Papipapito/MSXimus_138/docs/historico/informes_v2/INFORME_NIQUELADO.md

# Informe final — Investigación "niquelado" del repo MSXimus (v2.0)

**Contexto**: v2.0 recién publicada (V9968 + VRAM DDR3 con refresh arreglado + WiFi C6). Va a venir gente a mirar el repo, sobre todo el `opl4wave`, que quieren copiar. Cinco frentes auditados: opl4wave (bugs), audio OPL4-FM/mixer, shim DDR3, parches V9968, top/relojes, SD/USB/flash, y una pasada de presentabilidad ("opl4wave-bonito"). Todos los hallazgos aquí listados pasaron una fase de verificación adversaria (intento de refutación contra el RTL real); veredictos: **CONFIRMADO** = reproducción lógica cerrada en el código, **PLAUSIBLE** = mecanismo real verificado pero disparador no demostrado.

Rutas relativas a `C:\Users\alber\proyectosAI\msx\MSX_up\`.

---

## 1. Bugs verificados (ranked por severidad)

### Severidad ALTA

| # | Fichero:línea | Veredicto | Bug (una frase) | Esbozo de arreglo |
|---|---|---|---|---|
| 1 | `fpga/v9968/vdp_cpu_interface.v:309` | CONFIRMADO | El latch del bus acepta con `ff_bus_ready` CRUDO mientras el glue espera el `bus_ready` gateado (`:332`), así que una transacción I/O que caiga en el último ciclo de una ventana busy/inflight se ejecuta DOS veces — mecanismo cerrado ciclo a ciclo que explica el residuo histórico del "salto +1 del puerto CPU" (~0,1-0,3%), distinto del router +1 arreglado en _157. | Gatear el latch con las mismas condiciones que el output: `bus_valid && ff_bus_ready && !ff_busy && !ff_pf_inflight`; verificar con tb_t2cpuread + tráfico I/O a 5.37 MHz con latencias forzadas >2 µs. |
| 2 | `fpga/v9968/vdp_command_cache.v:177` | CONFIRMADO | Si un start de comando (escritura de R#46, legal sin esperar CE=0) llega durante un flush ya drenado (típico: comandos de solo lectura como POINT/SRCH/LMCM), `ff_busy` se pone a 1 y ningún camino lo limpia jamás: el comando nuevo nunca se ejecuta, CE cae igualmente y el software ve un rectángulo/copia fantasma; solo recupera la siguiente escritura de R#46. | En la rama start con flush en curso: `ff_busy <= w_dirty_any \| ff_vram_valid;` — o añadir en el estado 3'd1 del flush `if (!ff_vram_valid) ff_busy <= 1'b0;` para que TODO cierre de flush libere busy. |
| 3 | `fpga/src/v9968_vram_shim.v:28` | CONFIRMADO | En el build de respaldo _137 (VRAM del V9968 en la SDRAM compartida) la VRAM en 0x280000 cae DENTRO de la RAM de muestras del OPL4 (0x200000-0x3FFFFF, entera escribible según `opl4_pcm.v:575`): samples >512KB o la detección de RAM de MoonBlaster Wave machacan la VRAM en vivo, y viceversa. Desarmado en la v2.0 (VRAM en DDR3), pero armado en la línea de respaldo documentada. | Mover la familia wv2/wv3 a su propio bloque de filas (`{1'b1,2'b01,addr[21:12]}` en `memory.v`, filas 5120+ libres) o recortar la RAM visible del motor a 512KB (guard `e_addr22[21:19]==3'b100`); como mínimo, documentar el solape en la línea _137. |

### Severidad MEDIA — CONFIRMADOS

| # | Fichero:línea | Veredicto | Bug (una frase) | Esbozo de arreglo |
|---|---|---|---|---|
| 4 | `fpga/top.v:3509` | CONFIRMADO | El tono de test 440 Hz del bug #14 (_127H) sigue armado en release: activar el toggle "Sprite Limit" del menú (config2[3], que ADEMÁS sigue conectado a `maxspr_n` en la build commiteada) sustituye TODO el audio por una cuadrada a -12 dB, y el estado persiste en flash si se guarda la config. | Envolver la rama del tono en `` `ifdef DEBUG_TONE `` (o retirarla) y devolver config2[3] a su función única; si se conserva, moverlo a un bit SWIO no expuesto en el menú. |
| 5 | `fpga/src/opl4_pcm.v:726` | CONFIRMADO | `.IC_N(erst_n)` empatado con `.RST_N(erst_n)` deja muerta la rama de reset de chip del motor: MIXFM arranca en 0x00 en vez del canon 0x1B, así que VGMPlay/OPL3 (que nunca escribe F8) suena con el FM ~2,7× (+8,5 dB) más fuerte que un MoonSound real. | Retrasar IC_N unos ciclos respecto a RST_N en opl4_pcm (contador que suelte IC_N N ciclos después) para que la rama RES_N ejecute tras cada reset; o parchear la rama RST_N del motor con los valores canon (marcado `MSXimus:`). |
| 6 | `fpga/src/opl4_pcm.v:277` | CONFIRMADO | El acumulador de CE (24 bits, sin clamp) se envuelve a los ~32 µs de stall continuo; con los stalls reales de los watchdogs (~0,9 ms wave_ddr3, ~3,5 ms ifw) pierde ~39-153 muestras de crédito y, como productor y consumidor del FIFO _98 usan la fracción exacta 14112/15625, el colchón (armado a 8) cae a 0-1 PARA SIEMPRE: crujidos permanentes tras un único evento de watchdog, hasta reset. | Saturar el acumulador (`if (ce_acc < CE_MAX) ce_acc <= ce_acc + CE_INC`, tope 2-3 muestras) y/o re-armar el colchón del FIFO a 8 cuando `ifw_hits`/`wd_ops` incrementen. |
| 7 | `fpga/src/opl4_pcm.v:124` | CONFIRMADO | El latch host→motor de escrituras OPL4 es de 1 plaza con toggle y sin /WAIT: dos escrituras sin consumo intermedio se ANULAN por paridad (ambas desaparecen), alcanzable cuando el CE del motor se congela más de ~2,2 µs (escenario watchdog ~3,5 ms, con precedente en HW) — instrumento/nota/KEY-ON perdidos. | Mini-FIFO host→motor de 4-8 plazas, o contador Gray de 2 bits (las peticiones dejan de anularse por paridad), y/o extender `wave_wait_n` a las escrituras con la plaza ocupada. |
| 8 | `fpga/top.v:3021` | CONFIRMADO | Con el motor sonando, las escrituras por el puerto debug 34-37h van al puerto HOST de wave_sdram puenteando la caché por-slot de opl4_pcm (cuyo único flush es el wr_edge del propio motor): una palabra ya cacheada se sirve rancia indefinidamente, y para región ROM (parches de la YRW801) no existe NINGUNA vía de invalidación salvo miss o reset. | Cruzar un toggle `host_wrote` de top.v al dominio clk_eng que ejecute el flush total (lb_v/lb_pfb<=0, vaciar pfq), o bloquear las escrituras 34-37h mientras `wl_done==1`. |
| 9 | `fpga/src/opl4_pcm.v:179` | CONFIRMADO | `mix_fm` no está en la rama de reset y solo se refresca cuando el motor emite muestra; como todo reset relanza la copia+verify de 2 MB de la YRW801 (~5 s con el motor parado), si el software anterior dejó F8≠0 (F8=7 = MUTE) el FM del OPL4 arranca atenuado o mudo durante segundos tras cada reset caliente. | Añadir `mix_fm <= 6'd0;` a la rama `!rst_n` (0 dB, igual que el stub sin motor); y muestrear `eng_mixfm` junto al toggle `pcm_t_x` en el lado eng para el cruce de dominio (mismo protocolo que pcm_l_x/pcm_r_x). |
| 10 | `fpga/top.v:3485` | CONFIRMADO | Los dos PSG entran al mixer como unsigned 0..255<<6 (término siempre ≥0, hasta +32640 en mono) frente al resto bipolar: el headroom positivo del sat16 se agota casi solo con los PSG y el mixer recorta sistemáticamente solo el semiciclo positivo (distorsión asimétrica "sucia" al cargar la mezcla). | Centrar el PSG antes de mezclar (DC-blocker de 1 polo: `y = x − lpf(x)`, un acumulador de 24 bits) o restar un offset fijo equivalente al nivel medio; alternativa barata: entrar con `<<5`. |
| 11 | `fpga/top.v:784` | CONFIRMADO | El O_DA del PSG principal está sin conectar y IN 0xA2 devuelve 0xFF para todo registro salvo R14: el patrón canónico RDPSG(R7)→AND/OR→WRTPSG escribe basura en los enables de mezcla (canales deshabilitados), mientras el segundo PSG sí tiene readback real. | Conectar `O_DA` del psg1 y servirlo en IN 0xA2 para `psg_addr_latch != 14` (conservando la inyección de joystick USB en R14), igual que ya se hace con `psg2_dout`. |
| 12 | `fpga/src/v9968_vram_shim.v:1320` | CONFIRMADO | El camino de la VENTANA de prefetch (pww) hereda la carrera fill↔escritura que el _150 solo curó en la sc-cache (sin `wr_accept` en el commit ni matador de pendientes, y `pw_v` es set-only tras _140): una escritura del VDP coincidiendo con la completación del fill deja la ventana válida con el dato PRE-escritura, servido en hit ~1 frame parcial. | Replicar la cura _150 en pww: abortar el commit de `pww_*`/`pwv_set` si en el ciclo de completación hay `wr_accept` o `wrk_p1` con `wrk_addr1==cur_addrw` (comparador FF-FF, mismo coste que la línea 934); el word se autocura por miss. |
| 13 | `fpga/src/v9968_ddr3_backend.v:430` | CONFIRMADO | Todo el servicio de ST_IDLE (hits, emisión Y el rescate FFFF) vive dentro de `if (init_calib_complete)`, y el watchdog se resetea en IDLE con `iss_free`: si la calibración cae en marcha (el caso que `calib_drop` de _95 existe para cazar), una petición pendiente no recibe ni dato ni vacuna — CPU y comandos congelados hasta que el motor de reintentos de ~335 ms/intento (~1/7 de éxito) tenga suerte. | Rama en ST_IDLE: `!init_calib_complete && (a_req&&!a_srv \|\| b_req&&!b_srv) && op_wd[16] → completar FFFF` (dejando que op_wd cuente con petición pendiente sin calibración); motor de reintentos intacto. |
| 14 | `fpga/src/v9968_ddr3_backend.v:522` | CONFIRMADO | En el rescate _95 de ESCRITURA la caché de línea clA/clB ni se actualiza ni se invalida, pero la escritura retenida SÍ aterriza después en la DRAM: los hits de lectura posteriores sirven el dato pre-escritura persistentemente (una línea rancia nunca se autorrepara: leerla es hit) hasta que un miss ajeno la desaloje. | En la rama 522-530 aplicar la misma actualización de clA/clB (op_addr/op_wdata/op_wmask siguen vivos) o, más barato, invalidar (`clA_v/clB_v <= 0`) las líneas cuyo tag case con `op_addr[21:4]`. |
| 15 | `fpga/src/v9968_vram_shim.v:492` | CONFIRMADO | La fusión fill+escritura del _148 FIX B (`pf_one`/`pf_fuse`) es código muerto — cero consumidores en todo fpga/, las tres guardas reales siguen siendo `!pf_dirty` a secas — así que la mejora que la clasificación MISSCLS justificaba (6 de 11 miss de ráfaga) nunca entró en el netlist, y los comentarios de rd_complete describen un comportamiento que el RTL no tiene. | O cablear la fusión como anuncian los comentarios (guardas `!pf_drop`, dato `pf_fuse({w_hi,w_lo})`) y validarla en tb_menu_ddr3/tb_vbcoh, o retirar el bloque 480-510 y corregir los comentarios. |
| 16 | `fpga/v9968/vdp_command_cache.v:697` | CONFIRMADO | Tras abortar un comando con una lectura aceptada pero sin respuesta y caché limpia, la respuesta huérfana (14-90+ ciclos después) resucita una entrada con `ff_update_target` ya reseteado a 0: le cambia la dirección a la de la lectura ABORTADA conservando el byte del comando nuevo → 1 byte de VRAM corrupto en la dirección vieja + píxel perdido + pulso espurio que clobbrea `ff_read_pixel/ff_read_byte`. | Flag `ff_read_discard`: se arma en el start (ambas ramas) si había una lectura aceptada sin respuesta (registrar `ff_read_pending` entre aceptación y rdata_en); la rama 691 consume y descarta la primera respuesta con el flag armado. |
| 17 | `fpga/v9968/vdp_command_cache.v:313` | CONFIRMADO | El start no limpia `ff_cache_vram_rdata_en`: si el R#46 coincide con el pulso (ventana de 1 ciclo) y hay flush sucio, el strobe queda alto todo el flush y al cerrarse la rama :313 gana a la aceptación con ready ya a 1 — el motor cree aceptada su petición y espera un rdata_en que nunca llega (comando colgado con CE=1). | Añadir `ff_cache_vram_rdata_en <= 1'b0;` en AMBAS ramas del start (línea 165): restaura el invariante de 1 ciclo y la carrera del primer ciclo post-flush desaparece. |
| 18 | `fpga/v9968/vdp_timing_control_ssg.v:432` | CONFIRMADO | _120 NO es bit-exacto (ORIGEN.txt refutado): la resta del scroll de sprites usa `reg_horizontal_offset_l` VIVO mientras el original usaba el valor latcheado una vez por par de líneas — un split de R#27 por interrupción llega a los sprites hasta ~2 líneas antes que al fondo (desalineación 1-7 px) y puede desencuadrar la colección de sprites una línea. | Restar el valor que el latch tendrá de verdad: `((ff_v_count[0] && w_h_count_end) ? reg_horizontal_offset_l : ff_horizontal_offset_l)` — ahora sí bit-exacto conservando el registro _120. |
| 19 | `fpga/v9968/vdp_video_out.v:374` | CONFIRMADO | El snap del _142 a 8'd63 no selecciona "un solo píxel": el datapath del bilinear pesa coeff/256, así que 63 = 24,6% de mezcla — 1 de cada 3 fronteras de píxel conserva una columna fantasma al ~25% (y en la columna central la mezcla AUMENTA respecto al bilinear original), justo el artefacto que _142 quería eliminar. | Snap al valor que satura el datapath: `8'd255` (99,6%, error ≤1 LSB), o intercambiar taps; verificable en tb_geomfast/tb_textgeom con una frontera 0x00/0xFF que debe salir binaria. |
| 20 | `fpga/top.v:3650` | CONFIRMADO | El guardado de config (#42 bit6) es un pulso de 1 ciclo que flash_rw solo muestrea en STATE_LOAD_CMD, y el loader del YRW801 ocupa la SPI varios segundos justo cuando el menú ya corre: el guardado se pierde EN SILENCIO (sin busy, sin bit de error legible), y con bit7 el reset procede igualmente descartando los ajustes. | Latch pendiente `flash_write_req` mantenido hasta que el flash lo acepte, con el loader YRW801 pausando entre pasadas cuando haya write pendiente; opcional: bit "save pending/done" legible por el menú. |
| 21 | `fpga/top.v:3524` | CONFIRMADO | El stub `else` de ENABLE_SOUND ata `y8950_int_n` y `opl4pcm_wait_n` pero OLVIDA `opl4_int_n` (declarado solo dentro del bloque de sonido), que cuelga incondicionalmente del INT_n del Z80: un build sin sonido compila con una net implícita de 1 bit sin driver en la señal más crítica del CPU (lección EX3638 del propio repo). | Añadir `wire opl4_int_n = 1'b1;` al stub else (junto a y8950_int_n, línea 3534). |
| 22 | `fpga/top.v:3149` | CONFIRMADO | La matriz de defines ENABLE_* no tiene ninguna guarda y varias combinaciones documentadas solo en comentarios compilan con nets implícitas sin driver: OPL4_WAVE sin WAVE_DDR3 (motor en reset eterno), WAVE_LOADER sin WAVE_DDR3 (dirección de flash truncada a 1 bit), sin CONFIG (warm-reset/turbo huérfanos), sin SDCARD (`sd_busy_w`) — rotura silenciosa dependiente de la herramienta, el patrón exacto que ya mordió en la _40. | Bloque de guardas al inicio de top.v (`` `ifdef ENABLE_OPL4_WAVE `ifndef ENABLE_WAVE_DDR3 `` → instanciar módulo inexistente para forzar error) + stubs en los else de CONFIG/SDCARD (`config_reset_req=0`, `pana41_wr=0`, `sd_busy_w=0`). Coste cero en el build normal. |
| 23 | `fpga/src/wondertang/sd_reader.sv:294` | CONFIRMADO | Los seis estados de la cola de init SD (CMD2/3/9/10/7/16) quedaron fuera del acotado de reintentos del AUDIT #4: en timeout reintentan para siempre, `rbusy` queda a 1 eterno y `timeout_error` nunca sube — tarjeta marginal o extraída a mitad de init = driver Nextor colgado sin bit de error, hasta reset. | Extender el patrón AUDIT #4: en cada uno de esos estados, si `timeout\|\|syntaxe` y `retry_cnt==RETRY_MAX`, volver a IDLING con `retry_fail=1` (que ya se refleja en timeout_error). |
| 24 | `fpga/src/megaram.v:226` | CONFIRMADO | En modo ASCII16 el bit 6 del valor de banco se descarta (se guarda en `megaram_reg_L/H`, registros sin ningún lector — código muerto): los bancos 0x40-0x7F colapsan sobre 0x00-0x3F y una ROM ASCII16 >1 MB (homebrew/traducciones) se ejecuta con el segundo megabyte aliasado sobre el primero. | Usar `{cpu_dout[6:0], mitad}` como página (7 bits de banco de 16K = 2 MB completos); o documentar el límite y que el menú rechace ASCII16 >1 MB. |

### Severidad MEDIA — PLAUSIBLES (mecanismo real, disparador no demostrado)

| # | Fichero:línea | Veredicto | Bug (una frase) | Esbozo de arreglo |
|---|---|---|---|---|
| 25 | `fpga/src/opl4_pcm.v:493` | PLAUSIBLE | El consumo del toggle de done no lleva ID de operación: si un done llegara con >3,5 ms de retraso DESPUÉS de un rescate del watchdog, se atribuiría a la op nueva y envenenaría la caché con tag válido y dato viejo (releído en hit cada muestra) — mecanismo verificado, pero el precedente histórico real es un done PERDIDO (inofensivo), no retrasado, y no hay ruta demostrada al retraso. | Bit/contador de secuencia que viaje con el done (o flag `op_zombie` que el watchdog arme y descarte el PRIMER done posterior sin rellenar la caché), más invalidar la entrada `{cur_op_slot}` implicada al disparar el watchdog. |
| 26 | `fpga/src/v9968_cpu_glue.v:64` | PLAUSIBLE | El glue descarta en silencio un flanco de csw_n/csr_n que llegue con otra transacción en vuelo (sin cola ni /WAIT); la ruta de exposición por escrituras quedó refutada (cpu_vram_ready no se gatea por vram_stall), pero la ventana por LECTURAS/pre-lecturas del #98 (respuesta por rq con prioridad MÍNIMA del backend, inanición no acotada y con precedente _136) sigue abierta sin traza que la demuestre. | Bit `pend` que registre el flanco perdido (addr/dato cuasi-estáticos) y lo despache al liberar bus_ready; o /WAIT al Z80 mientras bus_valid siga pendiente; contador de flancos-descartados hacia la dbg_uart para confirmar en placa. |

---

## 2. Refutados (para el registro)

- **"vdp_int cruza clk_86→clk_54m sin sincronizador y con la ruta cortada en el SDC"** — los hechos citados son correctos (no hay 2FF en top.v, el SDC declara clk_86 asíncrono, t80.vhd:976 captura INT_n con un flop) pero la conclusión de bug es errónea: el clock-enable ES el sincronizador efectivo del camino. No tocar.

---

## 3. Plan de pulido (presentabilidad)

Inventario de hallazgos de presentabilidad (severidad baja + "opl4wave-bonito"), agrupados por lo que cuestan y lo que aportan, en TRES opciones acumulativas.

### Opción A — "Mínimo digno" (~1 sesión)

Lo imprescindible para que quien abra el `opl4wave` no encuentre mentiras ni un incumplimiento de licencia. Cero riesgo de regresión (comentarios + 2 cambios de RTL triviales).

1. **Cabecera del fichero estrella** (`fpga/opl4wave/ymf278b_gowin.v:1`, hallazgo ALTA de presentabilidad): es el único fichero del motor que entra en el build (`build.tcl:52`) y arranca en `module YMF278B (` sin una sola línea de comentario — sin atribución BSD-3 (MAME: Belmont/Galibert/hap), sin el permiso de srg320, sin la marca de GENERADO. Redistribuirlo así incumple la licencia que la cabecera del .sv promete conservar. **Arreglo**: que `postproc.py` inyecte una cabecera fija al regenerar (procedencia srg320+MAME, BSD-3 con titulares, "FICHERO GENERADO por sv2v — NO EDITAR; regenerar con convert.sh", fecha/hash de fuentes). ~10 líneas de Python.
2. **Cabeceras con contratos falsos** (`opl4_pcm.v:9`, `wave_sdram.v:15/35`, `opl4fm.v:22`, hallazgo ALTA): las tres cabeceras cuentan TRES contratos de reloj/backend distintos y ninguno es el del build (real: clk_eng=37.5 MHz CLKOUT4, acumulador 14112/15625, backend wave_sdram; y la IRQ del OPL3 SÍ está cableada desde _108 — un porter que se fíe de la cabecera la omite y rompe VGMPlay/MBWave). **Arreglo**: actualizar las tres al estado _104+/_108+ con nota histórica de wave_ddr3.
3. **Changelog de `YMF278B.sv:19`** ("la lógica del motor está INTACTA / Sin cambios MSXimus" — falso a la vista de los parches _114 y compañía): reescribirlo enumerando los cambios reales marcados `MSXimus:`.
4. **Telemetría que miente** (`opl4_pcm.v:836`): restaurar `fr[15] <= {ifw_hits, alive}` como documenta la propia spec de la trama (:758) y espera `tools/dbg_reader.py` — el diagnóstico _114diag dejó `{vid_s1, alive}` y los hits del watchdog (el centinela de los bugs #6 y #25 de este informe) son hoy invisibles por UART.
5. **Borrar lógica muerta delatora**: el always 299-308 + declaraciones de `vdp_vram_interface.v` (selector de fase fija pre-_157) y el bloque `pf_fuse` 480-510 del shim con sus comentarios corregidos (o nota "NO CABLEADO", si se pospone la decisión del bug #15).

**Gana el visitante**: el fichero que va a copiar tiene licencia y procedencia, los comentarios que lea dicen la verdad, y la telemetría cuadra con su documentación.

### Opción B — "Escaparate" (A + ~2-3 sesiones más)

Para que el que viene a copiar el opl4wave pueda PORTARLO sin arqueología, y el repo quede legalmente impecable.

6. **Paquete opl4wave portable + `PORTING.md`**: documento único con (a) inventario de ficheros y cuál compila el build (ymf278b_gowin.v generado vs YMF278B*.sv fuente, convert.sh/postproc.py); (b) contrato de relojes real (clk_eng 37.5 MHz, CE fraccionario 14112/15625, por qué); (c) contrato del puerto de memoria (wave_sdram vs wave_ddr3, latencias, watchdogs, qué asume el motor); (d) requisitos de la YRW801 (loader, 2 MB, verify) y el mapa de puertos MSX (C4-C7/7E-7F, 34-37h debug); (e) formato de la trama de telemetría + dbg_reader.py; (f) lista exacta de defines necesarios.
7. **Guardas de la matriz ENABLE_*** (= aplicar el fix del bug #22): bloque de `ifdef que fuerza error de compilación en combinaciones rotas + stubs (`opl4_int_n`, `config_reset_req`, `pana41_wr`, `sd_busy_w`). Protege directamente a los porters, que son quienes van a tocar los defines.
8. **Licencias y créditos repo-wide**: NOTICE/sección de créditos por origen (MAME BSD-3, srg320, jtopl2 LGPL, upstream V9958, hra1129, tiny9990 BSD-3...) — cierra además el pendiente "Créditos del MSXimus" ya anotado para la publicación.
9. **Quick-wins de vergüenza visible**: retirar/ifdef el tono 440 Hz (bug #4 — dos líneas, y es lo primero que un usuario del menú va a pisar), `psgPB` reg de 1 bit conducido por O_IOB (`top.v:2247` — mina para cuando se arregle el bug #11), comentario RWAIT desfasado de `sd_reader.sv:414`.

**Gana el visitante**: puede levantar el opl4wave en su placa siguiendo un documento, sin leerse 4000 líneas de top.v; y nadie puede acusar al repo de redistribuir MAME sin aviso.

### Opción C — "Museo" (B + ~3-5 sesiones más)

Repo auditable de punta a punta; cada comentario dice la verdad.

10. **Pasada completa de comentarios fósiles**: `pw_v` "gana la INVALIDACIÓN" (pre-_140), coeficientes "0..63" del bilinear, "~36us" del acumulador CE, comentarios de contrato en cabecera de CADA fichero tocado por un _NNN; instaurar y documentar la regla de casa: *cuando un _NNN cambia un contrato, se retoca la cabecera del fichero, no solo el punto del cambio*.
11. **Robustez "baja" restante** (mecánica, sin rediseño): resets simétricos del bridge CDC (`v9968_sdram_bridge.v:83`) y de wave_sdram (`wave_sdram.v:147`, done fantasma); 2FF para `init_calib_complete` (`v9968_ddr3_backend.v:134`); gate RstSeq en los takes de `memory.v:392`; contador `c_rqdrop` + `rq_room_soft<=11` en el shim (`v9968_vram_shim.v:1181`); filtro de plausibilidad del termómetro RO (`ro_osc.v:70`/`fan_ctrl.v:146`); puente de desaserción de reset por dominio y retirar `clock_reset` del SDC (`msx_console60k.sdc:59`); re-init SD en caliente (`top.v:4284` + IDLING→CMD0); timeouts SD recalibrados a la frecuencia real (`sd_reader.sv:478`); decode Konami4 fiel (`megaram.v:148`); clear del teclado companion (`hid.v:93`); unificar bloqueante/no-bloqueante en flash_rw/top; off-by-one del psg_filter (`psg_filter.v:28`); anti-alias barato en la decimación 3.6M→44.1k (`msx2hdmi_v9968.sv:594`, CIC/media móvil).
12. **Poda de docs/ y tools/**: dejar en raíz solo lo vigente; mover crónicas de investigación a `docs/history/`; que ningún .md contradiga al RTL (verificado contra los hallazgos de este informe).

**Gana el visitante**: cualquier auditoría externa (y el Albert de dentro de un año) encuentra un repo donde código, comentarios y docs son coherentes al 100%.

---

## 4. Recomendación

**Opción B**, y en paralelo un **v2.0.1 correctivo** con los cuatro arreglos de pocas líneas y máximo retorno: los tres ALTA (#1 doble ejecución I/O — además el mejor candidato de siempre al salto +1 en caza —, #2 deadlock del flush, y para #3 basta de momento documentar el solape en la línea de respaldo _137) más el tono 440 Hz (#4), que es la única bomba que un usuario normal pisa desde el menú. La opción A se queda corta justo en lo que la gente viene a buscar (portar el opl4wave necesita el PORTING.md y las guardas de defines), y la C no bloquea a nadie: puede fluir después como sesiones sueltas de la lista del punto 11, empezando por las que tocan ficheros que ya se abran por otros motivos.
