Papipapito/MSXimus_138/docs/tecnica/05-v9968.md

# 05. El V9968 en el MSXimus

Qué es el V9968, de dónde sale el que lleva el MSXimus_138, en qué versión está, qué se le ha cambiado y cómo se comprueba. Sale de `fpga/v9968/ORIGEN.txt`, del RTL y del repositorio de HRA!. El core y su integración son los mismos que en el MSXimus 60K; lo que cambia en el 138K es el reloj del dominio del VDP y el arranque del PLL de la DDR3, apartado 5.

## 1. Qué es

El **V9968** es el VDP que diseñó Takayuki Hara (HRA!) como continuación del V9958: un superconjunto reimplementado desde cero en Verilog, pensado para un "MSX2++". Se presenta como un V9958 hasta que el software le pide lo nuevo:

- Comandos de bloque más rápidos (modo HS) y dos comandos nuevos: LRMM, que rota y escala una imagen al copiarla, y LFMM.
- Paleta ampliada de 5 bits por componente, 32768 colores.
- Modo 3 de sprites: 16 por línea, escalado y translucidez, con conjuntos de paleta por sprite.
- VRAM de 256 KB.
- Entrelazado plano, interrupción de fin de comando, sprites que no siguen al scroll vertical.

Todo se activa por registros, así que el software de MSX2 y MSX2+ corre sin enterarse. HRA! lo desarrolla como cartucho para la Tang Nano 20K y documenta el interfaz en su manual del programador; el MSXimus lo integra como VDP interno.

## 2. De dónde sale el nuestro

| | |
|---|---|
| Repositorio | `hra1129/V9968_Cartridge`, carpeta `fpga/V9968_Cartridge_TangNano20K/src/v9968` |
| Revisión fijada | `5978d18`, 8 de julio de 2026 |
| Licencia | La de HRA!, tipo BSD, no comercial: redistribución con los avisos intactos, venta no |
| Clon local para comparar | `proyectosAI/msx/V9968_Cartridge` |

Los 21 ficheros del core están en `fpga/v9968/`. Dos llevan parches del MSXimus marcados en el código con "MSXimus:": el interfaz de VRAM, que enruta las respuestas por etiqueta para admitir latencia variable, y el módulo superior, que saca esas etiquetas al exterior. El resto está intacto respecto a la revisión fijada, más los parches de temporización y las correcciones que enumera `ORIGEN.txt`, cada una con el commit del MSXimus donde entró y, cuando viene de HRA!, con el commit suyo.

`ORIGEN.txt` es el documento canónico del árbol: lleva la lista de fixes de HRA! posteriores al snapshot y dice cuáles están aplicados, cuáles ya los teníamos y cuáles se descartaron y por qué.

## 3. Las generaciones del interfaz de registros

El V9968 ha tenido tres definiciones de los registros de control R#20 y R#21, y no son compatibles entre sí. Es la fuente principal de confusión alrededor de este chip, así que va con detalle.

| Generación | Desde | R#20 | R#21 | Quién la lleva |
|---|---|---|---|---|
| **A**, "th9958" | Octubre de 2025 hasta el 2 de junio de 2026 (tag v0.5) | bit 5 comandos extendidos, bit 6 VRAM de 256 KB | bit 0 identificador falso, bit 6 entrelazado plano, bit 7 interrupción de fin de comando | TangCartMSX, el openMSX de buppu3, DEVCON con 0xFF, las demos de terceros de septiembre de 2026 compiladas contra el emulador |
| **B**, "V58" | 2 de junio de 2026 (tags v0.6 a v0.72) | bit 0 HS, 1 SVNS, 2 ILNS, 3 modo 3 de sprites, 4 paleta ampliada, 5 entrelazado plano, 6 interrupción de fin de comando, 7 16 sprites por línea | bit 0 V58: a 1 se presenta como V9958 y es el valor por defecto; a 0 pasa a identificarse como V9968 con comandos nuevos y 256 KB, todo junto | El MSXimus desde la build _163 del 30 de julio de 2026 hasta la v3.6g del 60K, DEVCON y V9968DM con 0x9F, el manual del programador |
| **C**, "bloqueo" | 4 de agosto de 2026, sin tag ni manual | Como B | Como B, pero las escrituras a R#20 y R#21 se ignoran mientras el bit 7 del puerto 4 esté a 1, que es el estado tras reset | El bitstream actual del cartucho de HRA! y **el MSXimus desde la v3.6h del 60K (17 de septiembre de 2026, commit 679b8f0), que es lo que hereda la v3.7 del 138** |

Detección canónica de un V9968 en generación B: escribir 3Ah en R#21, leer S#1 y mirar el identificador en los bits 5-1: 2 es un V9958, 3 es un V9968.

Compatibilidad cruzada, que es lo que importa al probar software:

- Software B en hardware B: bien. Fue nuestro caso, con DEVCON, V9968DM y el benchmark de renatus, hasta la v3.6g del 60K.
- Software A en hardware B: **mal**. El bit 5 de R#20, que para él significa comandos extendidos, aquí es entrelazado plano, y la imagen sale revuelta a franjas. La cura es un byte: el valor de R#20 (0xFF pasa a 0x9F en DEVCON, 0x31 pasa a 0x11 en la demo técnica de renatus).
- Software C en hardware B: bien. La escritura de desbloqueo va a un puerto que aquí no responde, y el resto es B.
- Software B en hardware C: no detecta el V9968, porque R#21 se ignora. Es nuestro caso desde la v3.6h del 60K y en la v3.7 del 138: DEVCON con 0x9F, V9968DM y la demo técnica no ven el V9968 hasta que hagan `OUT (9Ch),0` antes de tocar R#20 y R#21.

La decisión de julio de 2026 fue quedarse en B porque es la que HRA! documenta en su manual y la que había aguantado sin cambios; el bloqueo C apareció después sin documentar y sin que su propio DEVCON lo use. El 15 de septiembre de 2026 la caza del marcador en blanco de Xevious Fardraut Saga, en la Zynq y en la Console 60K, obligó a portarlo (commit 679b8f0, v3.6h del 60K, heredado por la v3.7 del 138): la BIOS MSX2 escribe R#20..R#23 = 0 en cada init del VDP y, en B, ese R#21[0] = 0 encendía el modo nativo, con el A17 vivo en las bases de tabla, sin que nadie lo pidiera. Con el bloqueo, más la máscara del A17 en las cinco bases de tabla en modo V9958, el marcador aparece. Portarlo exigía primero lo del apartado siguiente.

## 4. El puerto 4

El V9968 define un cuarto puerto, 9Ch en el rango interno y 8Ch en el de cartucho, con los flags de interrupción de cuadro, línea y fin de comando en lectura y su borrado en escritura, y desde la generación C el bit 7 que bloquea R#20 y R#21. Hasta la v3.6g el MSXimus no lo decodificaba: el decodificador de `top.v` solo aceptaba los rangos 98h-9Bh y 88h-8Bh, y el glue fijaba a cero el bit de dirección que lo distinguía. Desde la v3.6h del 60K, y por tanto en la v3.7 del 138, `top.v` acepta también 9Ch y 8Ch (9Dh-9Fh y 8Dh-8Fh siguen fuera) y el modo del glue, `fpga/src/v9968_cpu_glue.v`, pasó de 2 a 3 bits. Lo que hace el puerto:

- Lectura: bit 7 el bloqueo de R#20/R#21, bits 2-0 los flags de fin de comando, línea y cuadro. Escritura: un 1 en los bits 0, 1 o 2 borra el flag correspondiente, y el bit 7 se copia al bloqueo. Con ello la interrupción de fin de comando (CEIE) ya es utilizable desde el software.
- Tras el reset el bloqueo está a 1: el software de generación B tiene que hacer `OUT (9Ch),0` antes de tocar R#20 y R#21; el de generación C ya lo hace.
- El core lo lleva en `fpga/v9968/vdp_cpu_interface.v`, marcado con el commit `ceeecd7` de HRA!. En el 138 está compilado, no visto en placa (pendiente de verificar en placa).

## 5. Cómo está integrado

El core va en su propio dominio de 85,909 MHz, 27 × 35/11, cero ppm respecto a 24 veces la subportadora de color NTSC. En el 138K ese reloj sale de `pll_86` en cascada desde los 27,000 MHz exactos de `pll_27`, porque el GW5AST no tiene PLLA y sus PLL van con `PLL_INIT` (capítulo 01), y su dominio `clk_86` está **sobre-restringido a 11,30 ns** en `fpga/constraints/msx_v9968.sdc` cuando el periodo real es 11,64: es la forma de obligar al rutador de Gowin, que cumple el periodo y para, a dejar margen. Un gate OK con 0,07 ns contra 11,30 son unos 0,41 ns reales. Este dominio, con el shim de VRAM como peor camino, es el que decide las campañas del 138: cierra alrededor de uno de cada tres dados (capítulo 07). Entre él y el resto del MSXimus hay tres piezas propias:

| Pieza | Fichero | Qué hace |
|---|---|---|
| Glue del bus | `fpga/src/v9968_cpu_glue.v` | Registra el bus del Z80 y emite una transacción valid/ready por ciclo de E/S. Hace el alias de 88h-8Bh sobre el mismo chip |
| Shim de VRAM | `fpga/src/v9968_vram_shim.v` | Sirve el contrato de ocho ciclos del core con una caché de línea y prefetch, y traduce a palabras de 32 bits con máscara de bytes hacia el backend. Dos canales en paralelo para los modos de 256 bytes por línea |
| Backend DDR3 | `fpga/src/v9968_ddr3_backend.v` | Los 256 KB de VRAM en la DDR3 del SOM, con su propio controlador: la misma IP x16 a 297 MHz que el 60K. En el 138K el `pll_stop` de la IP va directo a `ENCLK2` del PLL de 297, en vez de la danza mDRP con `pll_mDRP_intf` del 60K; el motor de reintentos escalonado y los puertos 2Ah-2Ch de la V3.7b son los mismos, así que la lotería de calibración por dado del 60K es igual de aplicable aquí (pendiente de verificar en placa). La alternativa con la VRAM en la SDRAM compartida, `v9968_sdram_bridge.v`, se conserva como respaldo |
| Puente HDMI | `fpga/video720/msx2hdmi_v9968.sv` | De la salida del VDP a 720p60, con el audio embebido |

El detalle de esa cadena está en el capítulo 01. Las cazas de errores de la integración, desde las rayas del DEVCON hasta el salto de dirección en la VRAM, están contadas en los informes de `docs/historico/`.

## 6. Cómo comprobarlo

**En placa**. Tres programas de referencia, todos en generación B, así que desde la v3.6h necesitan el `OUT (9Ch),0` previo del apartado 4 para detectar el V9968. En el 138K ninguno se ha ejecutado todavía: el V9968 del porte está compilado y verificado en simulación, y lo que sigue está validado en el 60K.

- **DEVCON.COM** de HRA!: detección, paletas por conjunto, sprites volteados, VRAM alta. Es el examen final.
- **V9968DM.COM**: la demo del cartucho.
- **ru66-v9968-demo** de herraa1: el DEVCON portado a MSXgl, que busca el V9968 en 88h-8Bh y por eso existe el alias.

Más las demos de terceros de septiembre de 2026: el benchmark de renatus-xxxx corre tal cual, la demo técnica con el byte de R#20 cambiado, y en el MSXimus 60K dan los mismos cuadros por segundo que el emulador con Z80. Están preparadas en `files/20260911/demos_v9968/` del repositorio del 60K.

**En el emulador**. Hay un solo emulador con V9968, el fork de openMSX de buppu3 (`buppu3/openMSX`, rama `v9968`, binario `d884c4b` sobre openMSX 21.0), y está en **generación A**. Sirve como referencia visual de las demos de esa generación y de todo lo que es V9958 estándar; no sirve para software de generación B. Se instala poniendo su `openmsx.exe` sobre una instalación normal de openMSX 21.0 y una máquina con `<version>V9968</version>` en el VDP; en este PC está montado aparte en `proyectosAI/msx/openmsx-v9968/` con la máquina C-BIOS del instalador de renatus-xxxx. Sus diferencias declaradas con el silicio: los tiempos de vídeo son los de un V9958, no hay exclusión entre comandos y el puerto 0, y los contadores NX y NY cuentan hacia abajo.

**En simulación**. `tools/v9968_sim/` tiene los bancos en Icarus Verilog que se usaron en las cazas: `tb_skip1` para el salto de dirección, `tb_sprite3` y `tb_textgeom` para los sprites y la geometría de texto, y `alias_idx.py` para el índice de la caché del shim.

## 7. Lo que queda

- Pasar DEVCON, V9968DM y las demos en una placa 138K: el V9968 del porte nunca se ha visto en pantalla, y con él la calibración de la DDR3 con el `pll_stop` en `ENCLK2` y el margen real del dominio `clk_86`.
- Que HRA! documente la generación C en su manual; mientras tanto, DEVCON, V9968DM y la demo técnica necesitan el `OUT (9Ch),0` previo para detectar el V9968.
- La geometría de 50 Hz no está medida; el puente solo hace 720p60.
- Vigilar `hra1129/V9968_Cartridge`: dos commits después de nuestro snapshot, el bloqueo y una revisión del manual, y nada más desde el 4 de agosto.
