Papipapito/MSXimus_138/docs/historico/GW5A_IP.md

# Port MSXnano → Tang Console 60K (GW5AT-60): regeneración de IPs de reloj y memoria (GW5A)

**Objetivo del documento.** Plan para regenerar, para la familia **Gowin GW5A / GW5AT-60 (Arora V)**, las
cuatro IPs de reloj actuales del core MSXnano (rPLL 108 MHz, dos CLKDIV, rPLL 135 MHz TMDS) y el
controlador de memoria (SDRAM → **DDR3 512 MB**), preservando el contrato de la interfaz `ram_*` / `vram_*`.

**Regla de anclaje.** Todo lo que sigue está anclado a `file:line` del árbol limpio
`C:\Users\alber\proyectosAI\msx\_MSXnano_dev_ref`. Los datos externos citan fuente. Lo que no he podido
confirmar contra fuente primaria va marcado **INCIERTO** con el motivo.
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
