Papipapito/MSXimus_138/docs/historico/MEMORY_CONTRACT.md

# MEMORY_CONTRACT.md — Contrato de la interfaz de memoria a preservar en el port SDRAM → DDR3

**Proyecto**: MSXnano — port Tang Nano 20K (Gowin GW2AR-18C, SDRAM integrada) → Tang Console 60K (SOM Tang Mega 60K = Gowin GW5AT-60, DDR3 512MB).
**Fuente**: copia limpia de `dev` en `C:/Users/alber/proyectosAI/msx/_MSXnano_dev_ref`.
**Regla**: todo anclado a `file:line` real. Lo no confirmado va marcado **INCIERTO**.
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
