Papipapito/MSXimus_138/fpga/top.v

`define ENABLE_V9958
`define ENABLE_BIOS
`define ENABLE_SOUND //v9958, bios required
`define ENABLE_MAPPER //bios required
`define ENABLE_SCAN_LINES
`define ENABLE_SDCARD
`define ENABLE_CONFIG
`define ENABLE_MIXER  //V3.7 (17/09/2026): mezclador por fuente (puerto #44 extendido) traido de la Zynq (5d3b409); niveles persistidos en la cola del pack (bytes 6..10)
`define ENABLE_WAIT //extra wait state for mreq+wr
//`define ENABLE_WAIT_ADAPTIVE //wait required
`define ENABLE_M1_WAIT //STANDALONE: 1 wait-state per M1 opcode fetch (the real-MSX brake). Comment out to disable.
//`define SWAP23
// ============ v3.0 BASE MINIMA (Fase 1-REDUX, 2026-07-09) ============
// Video 720p por puente BRAM (video720/msx2hdmi.sv) + subsistemas fuera.
// IMPORTANTE: VIDEO720 tambien esta `define'd en tn_vdp_v3_v9958/src/
// v9958_top.v (ficheros de compilacion distintos) — mantener SINCRONIZADOS.
`define VIDEO720
`define ENABLE_WIFI       // F1 (_73): WiFi UNAPI por el BL616 ONBOARD (UART en V14/U15, ver uwifi)
`define ENABLE_WIFI_ESP32 // _153: la UART del WiFi va al ESP32-C6 externo por el conector J10 (2x20 libre, fila PAR: 12=GND, 14=TX(W21), 16=RX(N17)) en vez del BL616 (sin antena/fw). Mismo wifi_lite, mismo baud 27M/31: el fw ducasp/ESP32-UNAPI a 859372 ya esta validado con este prescaler en el MSXnano.
//`define WIFI_PMOD_TEST  // (_77diag) UART del WiFi al PMOD1 — apagado
//`define WIFI_TAP_BL616TX  // _78diag (APAGADO en _111c: llevaba desde la _78 robandole E22 a todo; la telemetria _111 nunca salio por su culpa)
`define ENABLE_OPLL         // F3 (_38): OPLL de vuelta — 1a pieza re-añadida sobre la base validada
`define ENABLE_Y8950        // F2 (_79): MSX-Audio (Y8950) FM via jtopl2 (core ya vendido en fpga/jtopl/), puertos C0/C1. VALIDADO EN HW (juego OK)
`define ENABLE_Y8950_ADPCM  // F2 (_80): ADPCM-B del Y8950 — y8950_adpcm.v (glue openMSX-exacto) + decoder jt10_adpcmb + RAM samples 32KB BSRAM (NMS-1205 de serie). VALIDADO HW+VGMPlay
`define ENABLE_Y8950_IRQ    // F2 (_81): IRQ del Y8950 (timers+EOS+BUF ya enmascarados) al /INT del Z80 (wired-AND como el Music Module real). Arranca todo enmascarado = sin IRQ hasta que el software la pida
`define ENABLE_OPL4FM       // F2 (_82-_85): MoonSound FM (OPL3) en C4-C7 + stub wave 7E/7F. VALIDADO EN HW (reloj 96/98, limpio)
`define ENABLE_WAVE_DDR3    // F2 (_86): bring-up de la DDR3 del SOM para la memoria de ondas OPL4 (cliente independiente + puerto debug I/O 34-37h). Fase wavetable
`define ENABLE_WAVE_LOADER  // F2 (_87): carga de la YRW801 (2MB) de flash 0x500000 a DDR3 en BACKGROUND tras el boot (no bloquea el arranque). Status: bit2 de IN 36h = cargando
`define ENABLE_OPL4_WAVE    // F2 (_89): motor PCM 24 slots del OPL4 (YMF278B.sv de srg320 + permiso) en clk_x1 de la DDR3, CE fraccionario 44.1kHz con stall. REQUIERE ENABLE_WAVE_DDR3+LOADER. Con esto el MoonSound esta COMPLETO (FM+wavetable)
`define ENABLE_USB_KBD      // F3 (_39): teclado por USB-A DIRECTO al fabric (usb_hid_host, sin hub)
`define ENABLE_SCC          // F3 (_40): SCC de vuelta — scc_wave2v Verilog puro (el VHDL scc_wave_mul era BARRIDO por la sintesis GW5A)
`define ENABLE_TURBO       // P1: turbo WSX 5.37 de vuelta con la receta v1.9 (turbo_eff sin glitch + boot-turbo solo en frio)
// ¡OJO! ENABLE_V9968_VDP y ENABLE_VRAM_DDR3 se ven comentados AQUI y aun
// asi ESTAN ACTIVOS en las entregas: tools/lanzar_campana.ps1 los descomenta
// en el CLON antes de sintetizar (y aborta si no lo consigue). O sea que
// leer este fichero a secas te dice lo que NO lleva el bitstream. Para saber
// que hay de verdad en un .fs, mira el script de campana, no estas lineas.
//`define ENABLE_V9968_VDP   // F1 V9968: VDP de HRA! (fpga/v9968, tag+eco) + shim VRAM a SDRAM compartida (puerto wv2) + puente 800px (msx2hdmi_v9968). Sustituye v9958_top ENTERO. Activar en el build _117
//`define ENABLE_VRAM_DDR3   // _128X EXPERIMENTO: la VRAM del V9968 en la DDR3 del SOM (v9968_ddr3_backend; requiere ENABLE_V9968_VDP y USE_VRAM_DDR3=1 en build.tcl). ADVERTENCIA: DDR3 analogicamente marginal en esta placa (saga _94-_103)
//`define TURBO_SIN_GUARDA_SDRAM  // 🧪 EXPERIMENTO 26/08 — **PROBADO Y DESCARTADO**: sin la guarda el MSX SE CUELGA al poner el turbo (placa, 26/08). La guarda NO estaba obsoleta pese a que la VRAM se mudo a la DDR3: lo que la justifica no es la CONTENCION del VDP sino la LATENCIA de la SDRAM (y su refresco), que a 5,37 no cabe en un T-estado de 186 ns. Se deja el define por si algun dia se acelera el controlador. Coste medido de la guarda: 18% (4,41 de 5,37).
`define ENABLE_TURBOR_ID   // V3.1: S1990 del turboR (E4h-E7h) — la maquina se identifica como turboR y CHGCPU mueve el turbo. NO hay R800: ver fpga/src/msx_s1990.v
// ---- DIETA 16/09 (V3.6h): fuera de produccion la telemetria COM11, la tira
// WS2812, el ventilador por temperatura y el segundo PSG, y un solo
// decodificador de teclado. RETIRADA el 17/09: con un 5 % menos de logica el
// placer 1 rutaba PEOR (0 de 13 colocaciones distintas sin rutar, contra 9 de
// 16 con el netlist completo; el control v36q sin dieta dio 2 de 2 al primer
// intento, dado 4001 con 0,771 ns). Es la leccion del 08/08 otra vez: al 96-98 %
// de CLS manda la congestion local, no el area. Queda como opcion por si sirve
// en una caza: DIETA_V36H enciende el conjunto.
//`define DIETA_V36H
`ifndef DIETA_V36H
`define ENABLE_TELEMETRIA  // dbg_uart por E22/USB-C con los contadores del shim, DDR3, audio, fan
`define ENABLE_WS2812      // tira de 8 LEDs WS2812 en la carcasa
`define ENABLE_FAN_TEMP    // ventilador por temperatura (fan_ctrl + oscilador de anillo); sin el, fijo a ON
`define ENABLE_PSG2        // segundo PSG (OCM 2a gen) en 10h-12h con su filtro
`endif
`define ENABLE_IOSYS       // V3.1 PELDANO 1 (TangCore): iosys_bl616 + textdisp por la UART del BL616 (V14/U15) y overlay sobre el HDMI. Sin firmware en el MCU todavia: el overlay se enciende solo unos segundos al arrancar para demostrar la cadena y luego se aparta.
//`define DISABLE_BOOT_MENU  // _127D: arranque MSX DIRECTO (enmascara la firma AB del menu; tambien salta el init FM de esa pagina). Solo builds de prueba.

// _159: la RAM de muestras del ADPCM-B pasa de 32KB en BSRAM a los 256KB
// COMPLETOS del Y8950 servidos desde la SDRAM (adpcm_sdram.v -> puerto wv2,
// filas 5120+). Esto NO se decide a mano: se DERIVA, porque solo es legal
// cuando wv2 esta libre. Lo esta con el V9968 apagado y con el V9968 + VRAM
// en DDR3 (la linea principal _138); en la linea de respaldo _137 (VRAM del
// V9968 en la SDRAM) lo conduce el bridge del V9968 y el ADPCM cae solo a
// los 32KB de BSRAM de siempre (adpcm_sdram con FALLBACK_BSRAM=1). Derivarlo
// hace IMPOSIBLE por construccion la combinacion con dos drivers de wv2.
`ifdef ENABLE_Y8950_ADPCM
 `ifndef ENABLE_V9968_VDP
  `define ENABLE_ADPCM_SDRAM
 `else
  `ifdef ENABLE_VRAM_DDR3
   `define ENABLE_ADPCM_SDRAM
  `endif
 `endif
`endif

module top
#(
    parameter SD_SLOT = 3
)(
    input wire ex_clk_27m,  // Console 60K: 50 MHz (pin V22); el nombre se conserva del TN20K
    input wire s1,
    input wire s2,

    // --- STANDALONE MERGE: MSX bus ports removed; replaced by USB (BL616) + LED ---
    // The old external MSX bus signals (ex_bus_wait_n/int_n/reset_n/clk_3m6,
    // ex_bus_data, ex_msel, ex_bus_m1_n/rfsh_n/mreq_n/iorq_n/rd_n/wr_n,
    // ex_bus_data_reverse_n, ex_bus_mp) are now INTERNAL wires/tie-offs (see below).

    // SPI to on-board BL616 (FPGA Companion) - USB KEYBOARD and gamepads
    // (Console 60K: puertos m0s del dock M0S eliminados; companion BL616 onboard)
    input  wire spi_sclk,
    input  wire spi_csn,
    output wire spi_dir,
    input  wire spi_dat,
    output wire spi_irqn,
    // _153: WiFi por ESP32-C6 externo (Waveshare C6-LCD-1.3, fw ESP32-UNAPI-
    // Firmware rama msxnano, 859372 bps) en el CONECTOR J10 (el 2x20 libre,
    // "SDRAM1 CONN." del esquematico oficial 32001C; el modulo SDRAM del core
    // va en el otro). Peticion de Albert (v2, foto de la placa): los pines en
    // FILA UNICA para cable plano de una hilera -> COLUMNA PAR, pines 12-14-16
    // consecutivos: GND(12) TX(14=W21) RX(16=N17). El +5V (pin 11) queda en la
    // columna impar, asi que el C6 se alimenta por su USB-C.
    // esp_rx_i PULL_UP = idle UART correcto sin modulo pinchado.
    // ⚠ Si algun dia se pincha un 2o modulo SDRAM en J10, esto se muda.
    input  wire esp_rx_i,    // N17 = J10 pin 16 (SDRAM1_D10) <- IO16 (TX) del C6
    output wire esp_tx_o,    // W21 = J10 pin 14 (SDRAM1_D12) -> IO17 (RX) del C6
    // _156: indicador de TURBO en la pantalla del C6 (mismo esquema que el
    // nano: turbo_status pin 29 -> GPIO3, Display.ino TURBO_PIN con pulldown).
    // J10 pin 18 = el siguiente par del bloque => cable plano de 4 seguidos:
    // 12=GND 14=TX 16=RX 18=TURBO. Cablear al GPIO3 del C6. Peticion de Albert.
    output wire esp_turbo_o, // N13 = J10 pin 18 (SDRAM1_D8) -> GPIO3 del C6
    // Console 60K, mecánica JTAG→SPI (estilo C64Nano): jtagseln (NET_LOC
    // V_JTAGSELN) entrega los pines JTAG al fabric cuando vale 1; el BL616
    // reclama JTAG subiendo bl616_jtagsel (PULL_UP: sin firmware companion la
    // placa queda en modo JTAG = siempre reprogramable).
    input  wire bl616_jtagsel,
    output wire jtagseln,
    // V3.1 (TangCore): TX del enlace con el BL616. U15 = GPIO27 RX del MCU, y
    // quedo LIBRE cuando el companion SPI se mudo al J10 (spi_irqn -> AB22).
    // El RX no necesita pad nuevo: bl616_jtagsel YA ES el V14 = GPIO28 TX.
    output wire iosys_uart_tx,

    // discrete status LEDs (active low)
    output wire [5:0] led,
    output wire ws2812_led,   // external WS2812B status strip (case)

    // ---- DEBUG BRING-UP 60K: "electrocardiograma" por los dos PMODs ----
    //  (se retirará al terminar el bring-up; pines de C64Nano, LVCMOS33)
    //  PMOD1 io[0..5]=W19,W20,F19,F20,E22,D22 · PMOD0=V19,V18,G22,G21,E18
    output wire [4:0] dbg_pmod1,   // (D22/bit5 liberado para uart_pmod_rx)
    output wire [4:0] dbg_pmod0,
    input  wire uart_pmod_rx,      // PMOD1 D22: RX del WiFi en modo WIFI_PMOD_TEST (PC-de-ESP)

    //hdmi out
    output wire [2:0] data_p,
    output wire [2:0] data_n,
    output wire clk_p,
    output wire clk_n,

    // flash
    output wire mspi_cs,
    output wire mspi_sclk,
    inout wire mspi_miso,
    inout wire mspi_mosi,
    // Console 60K: la flash va cableada QSPI (W25Q64) — /WP y /HOLD deben ir a
    // nivel alto o la flash puede bloquearse/pausarse con los pines flotando.
    output wire mspi_wp,
    output wire mspi_hold,

    // MicroSD
    output wire sd_sclk,
    inout wire sd_cmd,      // MOSI
    inout  wire sd_dat0,     // MISO
    output wire sd_dat1,     // 1
    output wire sd_dat2,     // 1
    output wire sd_dat3,     // 1

    // F1 (_73): los puertos uart_tx/uart_rx del ESP-01S (nano) NO existen en el
    // 60K — la UART del WiFi va al BL616 ONBOARD por los pads ya constreñidos
    // bl616_jtagsel (V14 = GPIO28 TX del BL616) y spi_irqn (U15 = GPIO27 RX).

    //usb uart
    output wire usb_uart_tx,

`ifdef ENABLE_USB_KBD
    // F3 (_39): los 2 USB-A de la Console 60K van DIRECTOS al fabric
    // (H13/G13, M15/M16 — verificado en los .cst de TangCore; el esquematico
    // de Sipeed esta mal). Soft-host low-speed 1.5Mbps por puerto.
    inout wire usb1_dp,
    inout wire usb1_dn,
    inout wire usb2_dp,
    inout wire usb2_dn,
`endif

    // Magic ports for SDRAM to be inferred
    output wire O_sdram_clk,
    output wire O_sdram_cke,
    output wire O_sdram_cs_n, // chip select
    output wire O_sdram_cas_n, // columns address select
    output wire O_sdram_ras_n, // row address select
    output wire O_sdram_wen_n, // write enable
    inout wire [15:0] IO_sdram_dq, // 16 bit bidirectional data bus (Console 60K: SDR externa W9825G6KH)
    output wire [12:0] O_sdram_addr, // 13 bit multiplexed address bus
    output wire [1:0] O_sdram_ba, // two banks
    output wire [1:0] O_sdram_dqm, // 16/2

    // ---- _86: DDR3 del SOM (memoria de ondas OPL4; cliente independiente,
    //      la SDRAM/memory.v NO se toca). Pines del ddr3_framebuffer_gowin.
    output wire [14:0] ddr_addr,
    output wire [2:0]  ddr_bank,
    output wire        ddr_cs,
    output wire        ddr_ras,
    output wire        ddr_cas,
    output wire        ddr_we,
    output wire        ddr_ck,
    output wire        ddr_ck_n,
    output wire        ddr_cke,
    output wire        ddr_odt,
    output wire        ddr_reset_n,
    output wire [1:0]  ddr_dm,
    inout  wire [15:0] ddr_dq,
    inout  wire [1:0]  ddr_dqs,
    inout  wire [1:0]  ddr_dqs_n,

    // Ventilador de la Console 60K (FAN_EN, pin AB12 Bank9 1.5V): la placa
    // conmuta los 5V del conector SH1.0 con 1 = ON. Gobernado por fan_ctrl
    // (termometro de anillo de latches, ver fan_ctrl.v / ro_osc.v).
    output wire        fan_en_o

    //output wire SLTSL3

);

// ============================================================================
// GUARDAS de la matriz ENABLE_* (niquelado B, bug #22 del informe): las
// combinaciones rotas COMPILABAN con nets implicitas de 1 bit sin driver
// (el patron que ya mordio en la _40). Ahora fallan en sintesis instanciando
// un modulo inexistente cuyo NOMBRE es el mensaje de error. Coste cero en
// builds sanos.
`ifdef ENABLE_OPL4_WAVE
 `ifndef ENABLE_WAVE_DDR3
    ERROR_ENABLE_OPL4_WAVE_requiere_ENABLE_WAVE_DDR3 u_guarda_def1();
 `endif
 `ifndef ENABLE_WAVE_LOADER
    ERROR_ENABLE_OPL4_WAVE_requiere_ENABLE_WAVE_LOADER u_guarda_def2();
 `endif
 `ifndef ENABLE_OPL4FM
    ERROR_ENABLE_OPL4_WAVE_requiere_ENABLE_OPL4FM u_guarda_def3();
 `endif
`endif
`ifdef ENABLE_WAVE_LOADER
 `ifndef ENABLE_WAVE_DDR3
    ERROR_ENABLE_WAVE_LOADER_requiere_ENABLE_WAVE_DDR3 u_guarda_def4();
 `endif
`endif
`ifdef ENABLE_VRAM_DDR3
 `ifndef ENABLE_V9968_VDP
    ERROR_ENABLE_VRAM_DDR3_requiere_ENABLE_V9968_VDP u_guarda_def5();
 `endif
`endif
// Stubs para builds SIN estos subsistemas (nets que el resto del top consume
// incondicionalmente — sin ellos, net implicita sin driver):
`ifndef ENABLE_CONFIG
    wire config_reset_req = 1'b0;   // warm-reset: sin bloque config no hay peticion
    wire pana41_wr        = 1'b0;   // turbo Panasonic: sin config no hay decode
`endif
`ifndef ENABLE_SDCARD
    wire sd_busy_w = 1'b0;
`endif

initial begin

end
    //`default_nettype none

    //assign SLTSL3 = bus_mreq_disable ^ bus_iorq_disable ^ xffh ^ xffl ^ mapper_read ^ exp_slotx_req_r ^ bios_req ^ subrom_req ^ vdp_csr_n;

    // ===== STANDALONE MERGE: internalized MSX bus signals =====
    // These used to be top-level ports driven/sensed by a real MSX board.
    // Now: data bus is internal, WAIT/INT tied inactive, RESET from button + PLL lock,
    // 3.58MHz CPU clock generated internally. (Ported verbatim from MSXnano/fpga/top.v.)
    wire [7:0] ex_bus_data;          // internal (no external bus); see assign below
    wire ex_bus_wait_n  = 1'b1;      // no external wait
    wire opl4pcm_wait_n;             // _89: /WAIT del motor PCM OPL4 (IN 7Fh)
    wire ex_bus_int_n   = 1'b1;      // INT comes from internal VDP only

    wire clock_locked;
    wire ex_bus_reset_n;
    // Console 60K: los botones S1/S2 son ACTIVOS A NIVEL BAJO (PULL_UP en el CST,
    // reposo=1, pulsado=0 — C64Nano los llama key_*_n). En el TN20K eran activos
    // a nivel ALTO: con el pull-up del 60K, el ~s1 original dejaba ex_bus_reset_n
    // =0 PERMANENTE = todo el core MSX en reset eterno (causa raiz del bring-up
    // muerto 2026-07-07/08). Normalizamos a "press" activo-alto:
    wire s1_press = ~s1;
    wire s2_press = ~s2;
    assign ex_bus_reset_n = ~s1_press && clock_locked;   // s1 pulsado = reset


    // 108 MHz / 30 = 3.6 MHz internal CPU clock (replaces ex_bus_clk_3m6 pin)
    wire ex_bus_clk_3m6;
    reg [4:0] div30_cnt;
    reg clk_3m6_internal;

    // dangling sinks for the (now internal) bus-control nets the old logic still drives
    wire [1:0] ex_msel;
    wire ex_bus_m1_n;
    wire ex_bus_rfsh_n;
    wire ex_bus_mreq_n;
    wire ex_bus_iorq_n;
    wire ex_bus_rd_n;
    wire ex_bus_wr_n;
    wire ex_bus_data_reverse_n;
    wire [7:0] ex_bus_mp;

    //clocks
    // Console 60K: un unico Gowin_PLL (PLLA GW5A) sustituye a las 3 IPs GW2A
    // (rPLL CLK_108P + CLKDIV /4 + CLKDIV /2). clk_108m_n (fase CLKOUTP del
    // rPLL viejo) no tenia consumidores y se ha eliminado.
    wire clk_108m;
    wire clk_135;               // TMDS x5 del HDMI (mismo VCO: 135 = 5 x 27 exacto)
    wire clk_wave375; // _104: 37.5 MHz del PLLA (motor OPL4) — declarado ANTES
                      // de su primer uso (leccion Gowin de los implicitos)
    // 138K: CASCADA. El PLL del 138 exige PFD 19-81,25 MHz y VCO 650-1300: desde el
    // pad de 50 no salen 108/54/27 exactos y enteros. pll_27 (50/2 x27 = VCO 675)
    // da 27,000 exactos y de ahi cuelgan pll_main (x40 = VCO 1080), pll_86 y
    // pll_ddr3 (x33 = VCO 891), que a su vez presta 891/12 = 74,25 al PLL del HDMI.
    wire clk27_video;           // 27,000 de pll_27: referencia de pll_main, pll_86 y pll_ddr3
    wire clk_hdmi;              // 74.25 MHz pixel 720p
    wire clk_hdmi5;             // 371.25 MHz TMDS x5
    wire pll27_lock;            // gatea el reset de pll_main y del PLL DDR3
    wire clk_7425;              // 74,25 del PLL de la DDR3 (VCO 891/12): referencia de pll_74
    Gowin_PLL pll_main (
        .clkin  (clk27_video),  // 138K: 27,000 de pll_27 (cascada; PFD 27, VCO 1080)
        .reset  (~pll27_lock),  // 138K: PLL_INIT en reset hasta que el 27 engancha
        .clkout0(clk_108m),     // 108.000000 MHz (fraccional, exacto)
        .clkout1(clk_54m),      //  54.000000 MHz
        .clkout2(clk_27m),      // v3.0: 27M del PLLA (fase CONOCIDA vs 54/108, como el
                                //  rPLL del TN20K). Ya NO alimenta ningun OSER10 (el
                                //  TMDS vive a 74.25/371.25 en pll_74) -> la restriccion
                                //  que motivo el CLKDIV desaparece con el video 720p.
        .clkout3(clk_135),      // 135.000000 MHz (TMDS; sustituye al CLK_135 del tn_vdp)
        .clkout4(clk_wave375),  // 138K: 36.000 MHz (motor OPL4 wave; VCO 1080/30, misma fase que 27/54/108)
        .lock   (clock_locked),
        .mdclk  (ex_clk_27m)    // reloj de init del PLLA (secuencia mDRP)
    );

    // clk_27m = CLKDIV ÷5 del 135 (patrón nestang/z8086/Gowin en GW5A): el par
    // PCLK(27)/FCLK(135) de los OSER10 del TMDS queda alineado POR CONSTRUCCIÓN.
    // Dos salidas independientes del PLLA NO garantizan la fase de arranque de
    // sus divisores → serialización TMDS muerta (bring-up 2026-07-07: z8086
    // funcionaba en la placa y nuestro _06 no; este era el delta restante).
    // v2.4: CLKDIV/5 RESTAURADO (el OSER10 lo exige; _28 lo demostro en placa).
    // Su fase vs 54M es arbitraria -> NADA con bus de CPU debe clockear a 27M:
    // el PSG se movio al dominio 54M (v2.4); el arbitro DH/DL queda como unico
    // frente de fase pendiente (F11) — plan B: cruce en el linebuffer.
    // ================================================================
    // v3.0 FASE 1-REDUX: cadena de video 720p CALCADA de monitorcore
    // (la plantilla oficial de nand2mario para esta placa, validada por
    // Albert 10/10 arranques compilada con NUESTRA toolchain). Cascada
    // 50(pad) -> pll_27 -> 27 -> pll_74 -> 74.25 (pixel) + 371.25 (x5
    // TMDS), PLLA crudas identicas a las suyas. El CLKDIV desaparece:
    // clk_27m del MSX sale ahora del PLLA principal (clkout2, arriba) y
    // el HDMI ya no comparte NADA con el arbol del MSX — el cruce es
    // solo el ring BRAM dual-clock + toggles 2FF de msx2hdmi.
    // ================================================================
    pll_27 pll27_video (
        .init_clk(ex_clk_27m),  // 138K: reloj del PLL_INIT (50 MHz)
        .clkin  (ex_clk_27m),   // pad 50 MHz
        .clkout0(clk27_video),
        .lock_o (pll27_lock)
    );
    pll_74 pll74_video (
        .init_clk(ex_clk_27m),  // 138K: reloj del PLL_INIT (50 MHz)
        .clkin  (clk_7425),     // 138K: 74,25 del PLL de la DDR3 -> x10 entero (VCO 742,5)
        .clkout0(clk_hdmi),
        .clkout1(clk_hdmi5)
    );

    // _84: el OPL3 corre en clk_27m (PLLA principal, HERMANO de clk_54m):
    // cruce host_if emparentado que el STA cronometra (la afifo llevaba
    // ASYNC_REG de Xilinx que Gowin ignora — con PLLs distintos el CDC iba
    // sin blindar: candidato a las escrituras poco fiables de la _82/_83).
    // Sin 3er PLL. El pkg compensa: CLK_DIV_COUNT=545 -> fs 49.541 kHz
    // (+0.05%). pll_3375.v queda en el arbol por si se quiere volver.

    // JTAG→SPI del companion (estilo C64Nano): los pines JTAG se entregan al
    // fabric (SPI del BL616) solo con el PLL en lock y sin petición de JTAG del
    // BL616 (bl616_jtagsel, PULL_UP). Sin término de botón: s2 es el reset MSX
    // y no debe flapear el modo JTAG.
`ifdef ENABLE_WIFI
    // F1 (_73): GPIO28 del BL616 pasa a ser su UART TX (idle ALTO + trafico) ->
    // la mecanica jtagsel/companion queda invalida (el companion-SPI se
    // sacrifica: el teclado sigue por el soft-host USB-A). JTAG fijo en modo
    // JTAG: el flasheo del FPGA via partner queda intacto y sin flapeos.
    assign jtagseln = 1'b0;
`else
`ifdef ENABLE_IOSYS
    // 🚨 CON EL FIRMWARE TANGCORE, V14 YA NO SIGNIFICA "reclamo el JTAG":
    // es el TX de la UART del MCU (GPIO28) a 2 Mbps. Mantener la mecanica
    // C64Nano aqui haria que el fabric arrebatase y soltase los pines JTAG
    // con CADA BIT que mande el MCU -- y son justo los pines por los que el
    // BL616 programa la FPGA.
    // Se le dejan al BL616 y punto. No cuesta nada: el companion SPI que
    // vivia en ellos se mudo al J10 hace tiempo, asi que hoy no hay ni una
    // senal del diseno en esos pads (verificado en el .cst).
    assign jtagseln = 1'b0;
`else
    assign jtagseln = clock_locked & ~bl616_jtagsel;
`endif
`endif

    // ================================================================
    //  VENTILADOR por temperatura, TOMA 2 (_122): en HW la toma 1 no
    //  disparo con el disipador caliente (umbral +30C demasiado alto o
    //  pendiente del anillo menor que la estimada). Albert pide disparo
    //  ~40C: umbral RELATIVO bajado a ~+7-10C sobre el arranque
    //  (K_ON=10/1024 ~1%, K_OFF=5/1024) — con el die tibio deberia
    //  arrancar solo. Fail-safe intacto (anillo muerto -> ON).
    //  TOMA 3 (_123): en HW _122 TAMPOCO disparo con el disipador bien
    //  caliente — la pendiente real del anillo es aun menor. Umbral a
    //  K_ON=5/1024 (~0.5%) y, sobre todo, dbg_cnt del termometro SALE
    //  por el COM11 (4a palabra de la telemetria) para calibrar de una
    //  vez con lecturas reales frio/caliente en vez de seguir adivinando.
    //  TOMA 4 (_124): CALIBRADO con la telemetria de HW _123 — pendiente
    //  real ~6x menor (frio 386400, caliente-que-Albert-quiere-fan
    //  ~385400, WIN 2^17). Umbrales ABSOLUTOS (inmunes al reflasheo en
    //  caliente que envenenaba la baseline relativa) con WIN doblada a
    //  2^18 (menos ruido; cuentas x2: frio ~772800, ON <771600,
    //  OFF >772300).
    // ================================================================
    wire        fan_ro_en, fan_ro_rst;
    wire [19:0] fan_ro_cnt;
    wire [19:0] fan_dbg_cnt;
    //  TOMA 5 (_125): los umbrales ABSOLUTOS de la toma 4 murieron al
    //  rebuild (el anillo de la _124 corria un 8% mas rapido que el de la
    //  _123: la frecuencia depende del placement). Modo RELATIVO con la K
    //  real medida (K_ON=2/1024 = -0.195%, el punto de Albert era -0.26%)
    //  + garantia por tiempo: fan FIJO a los 6 min si no ha disparado.
    // _152: ventilador ~5 grados MAS TARDE + EL DOBLE DE HISTERESIS.
    // Albert reporto DOS cosas: que arranca pronto y que "se enciende y apaga
    // bastante" (ciclado audible, visible en el COM11: la columna fan alterna
    // ON/of cada pocos segundos). Lo segundo es histeresis corta, no umbral.
    // Un paso de K vale 1/1024 = 0.0977% de la cuenta del anillo; con la
    // pendiente REAL medida en placa (~0.0167%/grado, ver cabecera de
    // fan_ctrl.v: 6x menor que la teorica de 0.1%/grado) eso son ~5.9 grados.
    // Subiendo SOLO K_ON se arreglan las dos a la vez: el arranque sube ~5.9
    // grados y la banda pasa de 1 a 2 unidades (~5.9 -> ~11.7 grados), asi que
    // una vez encendido sopla el doble antes de parar y cicla la mitad.
    //   K_ON  2->3 : arranca a ~17.5 grados sobre el frio (antes ~11.7)
    //   K_OFF 1    : para    a  ~5.9 grados sobre el frio (SIN CAMBIO)
    // _173 EXPERIMENTO (peticion de Albert, 03/08): VENTILADOR SIEMPRE ON.
    // Motivo doble: (1) en placa el ventilador NO gira NUNCA, ni siquiera
    // pasados los 360 s de la garantia FORCE_ON_SEC — o sea que o el control
    // no llega al pin o el camino fisico (conector/polaridad/fan) esta mal, y
    // clavar el pin a 1 separa las dos cosas; (2) hay sospecha de margen
    // TERMICO en el arranque (bucle de resets en SCREEN 1 con la placa
    // caliente): con el fan fijo la temperatura deja de ser variable.
    // El fan_ctrl se queda instanciado SOLO como termometro: fan_dbg_cnt
    // sigue saliendo por el COM11 (columna T), su decision se ignora.
    wire fan_en_ctrl;  // decision del control, hoy ignorada (telemetria)
`ifdef ENABLE_FAN_TEMP
    fan_ctrl #(.WIN_CYC(32'd262144), .K_ON(10'd3), .K_OFF(10'd1),
               .FORCE_ON_SEC(32'd360)) u_fanctrl (
        .clk        (clk_27m),
        .reset_n    (clock_locked),
        .ro_en      (fan_ro_en),
        .ro_cnt_rst (fan_ro_rst),
        .ro_cnt     (fan_ro_cnt),
        .fan_en     (fan_en_ctrl),
        .dbg_cnt    (fan_dbg_cnt)
    );
`else
    // DIETA 16/09: ventilador FIJO a ON (decision de Albert). Fuera el control
    // por temperatura y su oscilador de anillo (el que daba los holds del
    // gate). El termometro nunca estuvo calibrado.
    assign fan_en_ctrl = 1'b1;
    assign fan_dbg_cnt = 20'd0;
    assign fan_ro_en   = 1'b0;
    assign fan_ro_rst  = 1'b0;
`endif
    // _175: experimento _173 CERRADO — con el pin a 1 el ventilador giro
    // perfecto en placa (03/08): el camino fisico (AB12/conector/fan) esta
    // BIEN. El "no gira nunca" de las s006/s007 tiene explicacion mundana:
    // sesiones con power-cycle cada 100-200s (up_sec nunca llega a los 360
    // de FORCE_ON_SEC) + baseline envenenada por reflasheo en caliente
    // (leccion _124). Vuelta al control automatico como en la v2.0.
    assign fan_en_o = fan_en_ctrl;
`ifdef ENABLE_FAN_TEMP
    ro_osc u_roosc (
        .ro_en   (fan_ro_en),
        .cnt_rst (fan_ro_rst),
        .cnt_out (fan_ro_cnt)
    );
`else
    assign fan_ro_cnt = 20'd0;
`endif

    // ================================================================
    //  DEBUG BRING-UP 60K — latidos de reloj y estado vital por PMODs
    // ================================================================
    wire [5:0] dbg_video_w;   // sondas de video r2: {reset_w, video_reset, tick_pal, tick_ntsc, vdp_hdmi_reset, pal_mode}
`ifdef VIDEO720
    wire [5:0] dbg_bridge_w;  // v3.1: diagnostico del puente msx2hdmi (a PMOD0)
`endif
    reg [24:0] dbg_cnt50  = 0;  always @(posedge ex_clk_27m) dbg_cnt50  <= dbg_cnt50  + 1'b1;  // XO 50MHz REAL (independiente del PLL)
    reg [23:0] dbg_cnt27  = 0;  always @(posedge clk_27m)    dbg_cnt27  <= dbg_cnt27  + 1'b1;
    reg [24:0] dbg_cnt54  = 0;  always @(posedge clk_54m)    dbg_cnt54  <= dbg_cnt54  + 1'b1;
    reg [25:0] dbg_cnt108 = 0;  always @(posedge clk_108m)   dbg_cnt108 <= dbg_cnt108 + 1'b1;
    reg [26:0] dbg_cnt135 = 0;  always @(posedge clk_135)    dbg_cnt135 <= dbg_cnt135 + 1'b1;

    // PMOD1 = relojes: [0] lock fijo · [1] 50M · [2] 27M · [3] 54M · [4] 108M · [5] 135M(TMDS)
    // (los assigns de dbg_pmod1 viven en el bloque de debug del final del
    //  fichero, junto a los divisores de frame que los alimentan)

    wire clk_enable_27m;
    wire clk_enable_54m;
    reg [1:0] cnt_clk_enable_27m;
    always @ (posedge clk_108m) begin
        cnt_clk_enable_27m <= cnt_clk_enable_27m + 1;
    end
    assign clk_enable_27m = ( cnt_clk_enable_27m == 2'b00 ) ? 1: 0;
    assign clk_enable_54m = ( cnt_clk_enable_27m[0] == 1 ) ? 1: 0;


    wire bus_clk_3m6;
    PINFILTER dn1(
        .clk(clk_54m),
        .reset_n(1),
        .din(ex_bus_clk_3m6),
        .dout(bus_clk_3m6)
    );

    reg bus_clk_3m6_27;
    reg bus_clk_3m6_27_0;
    reg bus_clk_3m6_27_1;
    reg bus_clk_3m6_27_2;
    reg bus_clk_3m6_27_3;
    reg bus_clk_3m6_27_4;
    reg bus_clk_3m6_27_5;
    reg bus_clk_3m6_27_6;

    always @ (posedge clk_27m) begin
        bus_clk_3m6_27_6 <= bus_clk_3m6;
        bus_clk_3m6_27_5 <= bus_clk_3m6_27_6;
        bus_clk_3m6_27_4 <= bus_clk_3m6_27_5;
        bus_clk_3m6_27_3 <= bus_clk_3m6_27_4;
        bus_clk_3m6_27_2 <= bus_clk_3m6_27_3;
        bus_clk_3m6_27_1 <= bus_clk_3m6_27_2;
        bus_clk_3m6_27_0 <= bus_clk_3m6_27_1;
        bus_clk_3m6_27 <= bus_clk_3m6_27_0;
    end

    wire clk_enable_3m6_27;
    wire clk_falling_3m6_27;
    reg bus_clk_3m6_prev_27;
    always @ (posedge clk_27m) begin
        bus_clk_3m6_prev_27 <= bus_clk_3m6_27;
    end
    assign clk_enable_3m6_27 = (bus_clk_3m6_prev_27 == 0 && bus_clk_3m6_27 == 1);
    assign clk_falling_3m6_27 = (bus_clk_3m6_prev_27 == 1 && bus_clk_3m6_27 == 0);

    wire clk_54m;   // Console 60K: generado por pll_main (clkout1); antes Gowin_CLKDIV2 /2

    wire clk_enable_3m6_54;
    wire clk_falling_3m6_54;
    reg bus_clk_3m6_54;
    reg bus_clk_3m6_prev_54;
    always @ (posedge clk_54m) begin
        bus_clk_3m6_54 <= bus_clk_3m6;
        bus_clk_3m6_prev_54 <= bus_clk_3m6_54;
    end
    assign clk_enable_3m6_54 = (bus_clk_3m6_54 == 0 && bus_clk_3m6 == 1);
    assign clk_falling_3m6_54 = (bus_clk_3m6_54 == 1 && bus_clk_3m6 == 0);

    wire bus_wait_n;
    PINFILTER dn2(
        .clk(clk_54m),
        .reset_n(1),
        .din(ex_bus_wait_n),
        .dout(bus_wait_n)
    );

    wire bus_reset_n;
    // (Se probo meter aqui un warm-reset pedido por el lanzador y se REVIRTIO:
    // pulsar S1 -- que hace exactamente eso -- NO recuperaba la maquina, o sea
    // que el problema no era ese. Y tocar bus_reset_n es de las cosas mas caras
    // de equivocar: si el termino se queda pegado, la maquina no arranca nunca.)
    PINFILTER dn3(
        .clk(clk_54m),
        .reset_n(1),
        .din(ex_bus_reset_n & ~config_reset),
        .dout(bus_reset_n)
    );

    // STANDALONE: generate the 3.58MHz CPU bus clock internally (was ex_bus_clk_3m6 pin).
    // 108 MHz / 30 = 3.6 MHz. (Ported verbatim from MSXnano/fpga/top.v.)
    always @(posedge clk_108m or negedge bus_reset_n) begin
        if (~bus_reset_n) begin
            div30_cnt <= 0;
            clk_3m6_internal <= 0;
        end else begin
            if (div30_cnt == 5'd14) begin
                clk_3m6_internal <= ~clk_3m6_internal;
                div30_cnt <= 0;
            end else begin
                div30_cnt <= div30_cnt + 1;
            end
        end
    end
    assign ex_bus_clk_3m6 = clk_3m6_internal;

    wire bus_int_n;
//    PINFILTER dn4(
//        .clk(clk_108m),
//        .reset_n(1),
//        .din(ex_bus_int_n),
//        .dout(bus_int_n)
//    );
    denoise dn4 (
		.data_in (ex_bus_int_n),
		.clock(clk_54m),
		.data_out (bus_int_n)
    );

    reg [7:0] bus_data;
    genvar i;
    generate
        for (i = 0; i <= 7; i++)
        begin: bus_din
            PINFILTER dn(
                .clk(clk_54m),
                .reset_n(1),
                .din(ex_bus_data[i]),
                .dout(bus_data[i])
            );
//            denoise2 dn (
//                .data_in (ex_bus_data[i]),
//                .clock(clk_108m),
//                .data_out (bus_data[i])
//            );
        end
    endgenerate

//    always @ (posedge clk_108m) begin
//        bus_data <= ex_bus_data;
//    end

    // ========================================================================
    // 16/09 (V3.6g): EL MSX NO ARRANCA HASTA QUE LA DDR3 DE LA VRAM HA CALIBRADO
    // ------------------------------------------------------------------------
    // La VRAM del V9968 vive en la DDR3 del SOM y su calibracion es una loteria
    // con reintentos de 335 ms (v9968_ddr3_backend, _131). Hasta hoy NADIE
    // esperaba a `ready`: la secuencia reset1/2/3 soltaba el streamer del pack y
    // el Z80 a los ~120 ms, y si la calibracion iba por el 2o o 3er intento la
    // BIOS escribia la VRAM en el vacio (o el bridge se quedaba esperando un
    // done que no llega) = PANTALLA EN NEGRO SIN LOGO, y la maquina viva por
    // debajo. Como cada dado calibra distinto, unos arrancaban y otros no con el
    // MISMO RTL: el 3557 (v36e) y el 3623 (v36h) se quedaban en negro desde el
    // cargador y arrancaban desde el USB del PC (otra rampa, otro tiempo); el
    // 3593 arrancaba siempre. Puede que la V3.6d nunca tuviera la culpa.
    // Ahora el paso a reset3_n espera a `vddr_ready` (sincronizado a 27 MHz),
    // con un tope de ~5 s (127 pasos de rst_step de ~39 ms) para que una DDR3
    // que no calibre nunca deje arrancar a ciegas como hasta ahora, en vez de
    // dejar la placa muerta.
    // ========================================================================
    wire vddr_ready_por;                       // ready del backend DDR3 (1 sin DDR3)
    reg  [1:0] vddr_rdy_s = 2'b00;             // 2 FF a clk_27m (viene del dominio x1)
    always @(posedge clk_27m) vddr_rdy_s <= {vddr_rdy_s[0], vddr_ready_por};
    // V3.7b: tope de ~10 s (255 pasos de ~39 ms): el motor de reintentos de la
    // DDR3 ya escalona las ventanas y un dado lento (4139: >10 s) calibra sin
    // que el MSX haya arrancado a ciegas y perdido el logo. Sin video no hay
    // nada que hacer antes, asi que esperar no cuesta.
    reg  [7:0] vddr_wait_steps = 8'd0;         // pasos de rst_step esperando (255 = tope)
    // V3.7b: diagnostico del arranque de la DDR3 (puertos 2Ah-2Ch, ver ver_req_r)
    wire [6:0] vddr_att;                       // intentos de calibracion fallidos
    wire [7:0] vddr_calib10, vddr_boot100;     // duracion del intento bueno (10 ms) / arranque (100 ms)

    //startup logic
    reg reset1_n_ff;
    reg reset2_n_ff;
    reg reset3_n_ff;
    wire reset1_n;
    wire reset2_n;
    wire reset3_n;

    reg [20:0] counter_reset = 0;
    reg [1:0] rst_seq;
    reg rst_step;

    always @ (posedge clk_27m or negedge bus_reset_n) begin
        if (bus_reset_n == 0) begin
            rst_step <= 0;
            counter_reset <= 0;
        end
        else begin
            rst_step <= 0;
            if ( counter_reset <= 21'b100000000000000000000 ) 
                counter_reset <= counter_reset + 1;
            else begin
                rst_step <= 1;
                counter_reset <= 0;
            end
        end
    end

    always @ (posedge clk_27m or negedge bus_reset_n ) begin
        if (bus_reset_n == 0 ) begin
            rst_seq <= 2'b00;
            reset1_n_ff <= 0;
            reset2_n_ff <= 0;
            reset3_n_ff <= 0;
            vddr_wait_steps <= 8'd0;
        end
        else begin
            case ( rst_seq )
                2'b00:
                    if (rst_step == 1 ) begin
                        reset1_n_ff <= 1;
                        rst_seq <= 2'b01;
                    end
                2'b01:
                    if (rst_step == 1) begin
                        reset2_n_ff <= 1;
                        rst_seq <= 2'b10;
                    end
                2'b10:
                    // V3.6g: reset3_n (streamer del pack + Z80) solo cuando la
                    // DDR3 de la VRAM esta calibrada, o tras ~10 s a ciegas (V3.7b).
                    if (rst_step == 1) begin
                        if (vddr_rdy_s[1] || vddr_wait_steps == 8'd255) begin
                            reset3_n_ff <= 1;
                            rst_seq <= 2'b11;
                        end
                        else
                            vddr_wait_steps <= vddr_wait_steps + 8'd1;
                    end
            endcase
        end
    end
    assign reset1_n = reset1_n_ff;
    assign reset2_n = reset2_n_ff;
    assign reset3_n = reset3_n_ff;

    //bus demux
    reg [1:0] msel;
    reg [7:0] bus_mp;
    reg [4:0] mp_cnt;
    wire [15:0] bus_addr;
    assign ex_msel = msel;
    assign ex_bus_mp = bus_mp;

    localparam IDLE = 2'd0;
    localparam LATCH = 2'd1;
    localparam FINISH1 = 2'd3;
    localparam FINISH2 = 2'd2;
    localparam [3:0] TON = 4'd3;
    localparam [3:0] TP = 4'd1; //prefetch time
    reg [1:0] state_demux;
    reg [3:0] counter_demux;
    reg low_byte_demux;
    wire update_demux;
    assign bus_mp = ( low_byte_demux == 0 ) ? bus_addr[15:8] : bus_addr[7:0];
    always @ (posedge clk_108m) begin
        if (~bus_reset_n) begin
            state_demux <= LATCH;
            counter_demux <= 4'd0;
            low_byte_demux <= 0;
        end 
        else begin
            counter_demux = counter_demux + 4'd1;
            casex ({state_demux, counter_demux})
                {IDLE, 4'bxxxx}: begin
                    msel <= 2'b00;
                    counter_demux <= 4'd0;
                    low_byte_demux <= 0;
                    if (update_addr == 1 ) begin
                        state_demux <= LATCH;
                    end
                end
                {LATCH, 4'd1} : begin
                    msel[1] <= 1;
                end
                {LATCH, 4'd1 + TON} : begin
                    msel[1] <= 0;
                end
                {LATCH, 4'd1 + TON + TP} : begin
                    low_byte_demux <= 1;
                end
                {LATCH, 4'd1 + TON + TP + TP} : begin
                    msel[0] <= 1;
                end
                {LATCH, 4'd1 + TON + TP + TP + TON} : begin
                    msel[0] <= 0;
                    msel[1] <= 0;
                    state_demux <= FINISH1;
                end
                {FINISH1, 4'bxxxx}: begin
                    if (update_addr == 0 ) begin
                        state_demux <= IDLE;
                    end
                end
                {FINISH2, 4'bxxxx}: begin
                    if (update_addr == 0 ) begin
                        state_demux <= IDLE;
                    end
                end
            endcase
        end
    end




    //bus isolation
    wire bus_data_reverse;
    wire bus_m1_n;
    wire bus_mreq_n;
    wire bus_iorq_n;
    wire bus_rd_n;
    wire bus_wr_n;
    wire bus_rfsh_n;
    reg [7:0] cpu_din;
    wire [7:0] cpu_dout;
    wire bus_mreq_disable;
    wire bus_iorq_disable;
    wire bus_disable;
    assign ex_bus_m1_n = bus_m1_n;
    assign ex_bus_rfsh_n = bus_rfsh_n;
    assign ex_bus_data_reverse_n = ~ bus_data_reverse;
    //assign ex_bus_data_reverse = bus_data_reverse;
    //assign ex_bus_mreq_n = bus_mreq_n;
    //assign ex_bus_iorq_n = bus_iorq_n;
    //assign ex_bus_rd_n = bus_rd_n;
    //assign ex_bus_wr_n = bus_wr_n;

    assign bus_mreq_disable = 0;
    assign bus_iorq_disable = (
                                0
                        `ifdef ENABLE_V9958
                                || vdp_csr_n == 0 || vdp_csw_n == 0 
                        `endif 
                                ) ? 1 : 0;

    assign bus_disable = bus_mreq_disable | bus_iorq_disable;
//    assign ex_bus_data = ( bus_data_reverse == 1 && slot0_req_w == 0 ) ? cpu_dout : 
//                         ( slot0_req_w == 1 ) ? 8'hff :  8'hzz;
`ifndef SWAP23
    assign ex_bus_data =  ( bus_data_reverse == 1 ) ? cpu_dout : 8'hzz;
`else

    function [1:0] swap;
        input [1:0] entrada;
        begin
            case (entrada)
                2'b00: swap = 2'b00;
                2'b01: swap = 2'b01;
                2'b10: swap = 2'b11;
                2'b11: swap = 2'b10;
                default: swap = 2'b00; // Por seguridad
            endcase
        end
    endfunction

    wire [7:0] cpu_dout_swap;
    assign cpu_dout_swap = { swap(cpu_dout[7:6]), swap(cpu_dout[5:4]), swap(cpu_dout[3:2]), swap(cpu_dout[1:0]) };

    reg ppi_swap;
    always @ (posedge clk_27m) begin
        if (~bus_reset_n) begin
            ppi_swap <= 0;
        end
        else begin
            if (ppi_swap == 0) begin
                if (bus_data_reverse == 1  && ppi_req_w == 1) begin
                    ppi_swap <= 1;
                end
            end
            else begin
                if (bus_data_reverse == 0) begin
                    ppi_swap <= 0;
                end
            end
        end
    end

    assign ex_bus_data =  ( bus_data_reverse == 1  && ppi_swap == 0) ? cpu_dout :
                          ( bus_data_reverse == 1  && ppi_swap == 1) ? cpu_dout_swap : 8'hzz;
`endif

// ===== STANDALONE MERGE: USB joystick (PSG 0xA2/reg14) — ported from MSXnano/fpga/top.v =====
wire psg_req_r;
assign psg_req_r = (bus_addr[7:0] == 8'hA2 && bus_iorq_n == 0 && bus_m1_n == 1 && bus_rd_n == 0) ? 1 : 0;

// Gamepads USB. Antes los servia el companion SPI (el ESP32-S3); desde el
// 25/08 los lee el BL616 y llegan por hid1/hid2 del iosys (comando 9).
wire [7:0] joystick0;
wire [7:0] joystick1;

// Track which PSG register was last latched via I/O A0h
reg [3:0] psg_addr_latch;
always @(posedge clk_54m or negedge bus_reset_n) begin
    if (!bus_reset_n)
        psg_addr_latch <= 4'd0;
    else if (bus_addr[7:0] == 8'hA0 && bus_iorq_n == 0 && bus_wr_n == 0 && bus_m1_n == 1)
        psg_addr_latch <= cpu_dout[3:0];
end

// Seleccion de puerto de joystick: registro 15 del PSG, BIT 6 Y SOLO EL BIT 6.
//   bit6 = 0 -> puerto 1     bit6 = 1 -> puerto 2
//
// ⚠️ CORREGIDO 18/08. Antes esto miraba los bits [7:6] y trataba el bit 7 como
// "seleccionar puerto 2" activo a nivel bajo. El bit 7 del registro 15 NO es
// un selector: es el LED DE KANA. Con el bit 7 en alto (que es lo normal, LED
// apagado) el puerto 2 devolvia 0xFF SIEMPRE, hiciera lo que hiciera el
// software. Por eso el raton no se detectaba, y por eso el joystick USB del
// puerto 2 tampoco podia funcionar.
//
// Verificado contra el One Chip MSX (esemsx3/src/sound/psg/psg.vhd:115-119),
// que lo dice con todas las letras:
//     -- psg register #15 bit6 - joystick select : 0=port-a, 1=port-b
// y en la misma fuente, los pines 8: stra <= regb(4), strb <= regb(5).
reg psg_reg15_port2;
always @(posedge clk_54m or negedge bus_reset_n) begin
    if (!bus_reset_n)
        psg_reg15_port2 <= 1'b0;
    else if (bus_addr[7:0] == 8'hA1 && bus_iorq_n == 0 && bus_wr_n == 0 && bus_m1_n == 1
             && psg_addr_latch == 4'd15)
        psg_reg15_port2 <= cpu_dout[6];
end

// ===== AUTOFIRE (turbo) on the otherwise-unused joystick buttons 3 & 4 =====
// The FPGA-Companion joy byte uses bits 0-5 (dirs + A + B); bits 6/7 carry the
// extra pad buttons 3/4 (unused by the MSX 2-button joystick). While button 3
// is held it pulses TrigA, button 4 pulses TrigB, at ~10 Hz (50 ms ON / 50 ms
// OFF). Each phase must outlast one MSX PSG scan (~1 frame @50/60 Hz) so every
// press AND release is sampled; 50 ms = 2.5-3 frames is safe even on PAL.
// Ported from the goauld+RP2040 fork (there it lived in firmware; here, no
// RP2040 -> it lives in the FPGA on the PSG joystick-injection path).
//   54 MHz * 0.050 s = 2,700,000 cycles per half period.
reg        af_phase = 1'b0;
reg [21:0] af_cnt   = 22'd0;
always @(posedge clk_54m) begin
    if (af_cnt >= 22'd2700000) begin
        af_cnt   <= 22'd0;
        af_phase <= ~af_phase;
    end else begin
        af_cnt   <= af_cnt + 22'd1;
    end
end
// fire = manual press OR (autofire button held AND square-wave high). If the pad
// has no button 3/4 (bits 6/7 stay 0) this reduces to the original behaviour.
wire af_fa0 = joystick0[4] | (joystick0[6] & af_phase);   // joy0 TrigA: manual + btn3 turbo
wire af_fb0 = joystick0[5] | (joystick0[7] & af_phase);   // joy0 TrigB: manual + btn4 turbo
wire af_fa1 = joystick1[4] | (joystick1[6] & af_phase);   // joy1 TrigA
wire af_fb1 = joystick1[5] | (joystick1[7] & af_phase);   // joy1 TrigB

// Companion joy byte (active-high): bit0=Right, bit1=Left, bit2=Down, bit3=Up, bit4=A, bit5=B
// MSX PSG Port A (active-low):      bit0=Up,    bit1=Down,  bit2=Left, bit3=Right, bit4=TrigA, bit5=TrigB
wire [7:0] joy0_msx = {2'b11, ~af_fb0, ~af_fa0, ~joystick0[0], ~joystick0[1], ~joystick0[2], ~joystick0[3]};
wire [7:0] joy1_msx = {2'b11, ~af_fb1, ~af_fa1, ~joystick1[0], ~joystick1[1], ~joystick1[2], ~joystick1[3]};
// ===== RATON MSX (era V3) =====
// Emulado sobre un raton USB de PC. Vive en el PUERTO 2, que es donde lo
// espera el software de MSX, y solo se hace cargo del puerto cuando hay un
// raton USB enchufado; si no lo hay, el puerto 2 sigue siendo joystick como
// siempre. El protocolo entero esta en fpga/src/msx_mouse.v (y su banco en
// tools/mouse_sim). Los drivers detectan el raton solos ejecutando el
// handshake, asi que no hay nada que configurar en el MSX.
wire [7:0] msx_mouse_data;      // lo que el raton presenta en el registro 14
wire       msx_mouse_present;   // hay un raton USB vivo

wire [7:0] psg_joy_data = (!psg_reg15_port2) ? joy0_msx
                                              : (msx_mouse_present ? msx_mouse_data
                                                                   : joy1_msx);

// ===== STANDALONE MERGE: USB keyboard (PPI port B 0xA9 read / port C 0xAA latch) =====
wire ppi_portb_req_r = (bus_addr[7:0] == 8'hA9 && bus_iorq_n == 0 && bus_m1_n == 1 && bus_rd_n == 0) ? 1 : 0;
wire ppi_portc_req_w = (bus_addr[7:0] == 8'hAA && bus_iorq_n == 0 && bus_m1_n == 1 && bus_wr_n == 0);

// 🚨 PUERTO ABh — REGISTRO DE CONTROL DEL 8255. Faltaba, y por eso el LED de
// CAPS no funcionaba NUNCA (descubierto el 26/08 al no verse en el OSD).
//
// El MSX no enciende el CAPS escribiendo el puerto C entero por AAh: la rutina
// CHGCAP de la BIOS hace `OUT (0ABh),A` con el comando de BIT SET/RESET del
// 8255. Sin decodificar ABh esa escritura se perdia y ppi_port_c[6] se quedaba
// como estuviera. Como su unico consumidor era la tira WS2812 (que no siempre
// esta conectada), el fallo llevaba ahi sin que nadie lo viera.
//
// Formato del comando (bit 7 = 0 lo distingue del comando de MODO, que no nos
// afecta porque el modo del PPI del MSX es fijo):
//     bit 7   = 0   -> bit set/reset
//     bits 3:1      -> que bit del puerto C
//     bit 0         -> 1 = ponerlo, 0 = quitarlo
// Con esto funcionan de golpe los tres usos reales del MSX: LED de CAPS (bit 6),
// click de tecla (bit 7) y motor del casete (bit 4).
wire ppi_ctrl_req_w = (bus_addr[7:0] == 8'hAB && bus_iorq_n == 0 && bus_m1_n == 1 && bus_wr_n == 0);

// 🚨 LECTURA DEL PUERTO C (AAh) — FALTABA, Y ERA LA CAUSA DE RAIZ.
//
// El 8255 en modo 0 con el puerto C de salida deja RELEER el latch, y la BIOS
// del MSX cuenta con ello: para cambiar de fila de teclado hace
//     IN A,(0AAh) / AND 0F0h / OR fila / OUT (0AAh),A
// o sea LEE, conserva los bits altos (CAPS, click, motor) y devuelve el byte.
//
// Sin camino de lectura, ese IN devolvia FF del bus flotante -> la BIOS se
// quedaba con F0 -> y escribia F0|fila, BORRANDO los tres bits altos en CADA
// barrido del teclado (~60 veces por segundo).
//
// Medido en placa el 26/08 con la sonda del OSD: `ab6 225` (la BIOS SI escribia
// el bit del CAPS por ABh, 225 veces) y `PC FA` (= F0|fila 10) -- el valor
// exacto que predice esta explicacion.
//
// Esto es tambien la causa REAL del bug del motor de casete del MSXnano, que
// alli se parcheo con un registro aparte (`cas_motor_on`): no era solo que
// faltara decodificar ABh, es que ademas le borraban el bit.
wire ppi_portc_req_r = (bus_addr[7:0] == 8'hAA && bus_iorq_n == 0 && bus_m1_n == 1 && bus_rd_n == 0);

wire [3:0] keyboard_addr;
reg [7:0] keyboard_data;
wire [1:12] function_keys;

reg [7:0] ppi_port_c = 8'h00;   // R4: ppi_port_c did not exist in base — created here
always @(posedge clk_54m or negedge bus_reset_n) begin
    if (!bus_reset_n)
        ppi_port_c <= 8'h00;
    else if (ppi_portc_req_w)
        ppi_port_c <= cpu_dout;
    else if (ab_fin && ab_dat[7] == 1'b0)
        ppi_port_c[ab_dat[3:1]] <= ab_dat[0];
end

// 🚨 EL BIT SET/RESET SE APLICA UNA VEZ, AL TERMINAR LA ESCRITURA.
//
// La primera version lo hacia por NIVEL (`if (ppi_ctrl_req_w) ...`), igual que
// la escritura de AAh. Para AAh eso es inofensivo: escribe el byte ENTERO en
// cada flanco y gana el ultimo, que es el estable. Pero aqui el dato elige
// QUE BIT se toca, asi que un valor intermedio inestable escribe un bit AL AZAR
// -- incluyendo los bits 0..3, que son la SELECCION DE FILA DEL TECLADO.
//
// La pista estaba delante y la desprecie: la sonda del 26/08 veia pasar valores
// como 0xD0 y 0xF7, con el bit 7 a uno, o sea comandos de MODO del 8255 que
// ninguna BIOS manda a ese ritmo. Eran datos a medio formar. Con el uso normal
// no se notaba porque la BIOS reescribe constantemente; con INDEV.COM, que
// sondea el hardware a conciencia, la maquina se colgaba.
//
// Ahora se sigue el dato mientras dura la escritura y se aplica UNA sola vez,
// en el flanco de subida de la peticion, con el ultimo valor -- que es el que el
// Z80 mantiene hasta el final del ciclo.
reg       ab_req_d = 1'b0;
reg [7:0] ab_dat   = 8'd0;
wire      ab_fin   = ab_req_d & ~ppi_ctrl_req_w;
always @(posedge clk_54m or negedge bus_reset_n) begin
    if (!bus_reset_n) begin
        ab_req_d <= 1'b0; ab_dat <= 8'd0;
    end else begin
        ab_req_d <= ppi_ctrl_req_w;
        if (ppi_ctrl_req_w) ab_dat <= cpu_dout;
    end
end

// SONDA (26/08): ¿escribe la BIOS en ABh, y con que? Sin esto solo se puede
// adivinar. Se manda en el estado del OSD reaprovechando los dos bytes que
// eran del termometro (retirado por inutil).
assign keyboard_addr = ppi_port_c[3:0];

    // FPGA/bitstream version readable on I/O port 0x2F. The boot menu reads it and
    // warns if you flashed mismatched .fs/.bin (e.g. a v1.8 bitstream + a v1.7 BIOS pack).
    // Encoding 0xMN = version M.N. Bump FPGA_VERSION each release together with the pack.
    //
    // era V3 (18/08): 0x19 -> 0x30. La linea v3 es la version 3.0, la primera
    // sin SSRAM (problema de silicio del GW5AT-60B) y la que estrena el raton
    // MSX sobre raton USB.
    //
    // ⚠️ ESTO VA EMPAREJADO CON EL PACK. El menu de arranque compara este byte
    // con el que espera y AVISA si no cuadra. El fuente del menu NO esta en
    // este repo (docs/ROADMAP.md:39: "traerlo a la carpeta menu/ cuando toque
    // tocarlo"), asi que hasta que se regenere el pack con el menu esperando
    // 0x30, arrancar este bitstream con el pack_bios_v2.1b da un aviso de
    // version desemparejada. Es cosmetico -- el sistema arranca igual -- pero
    // hay que cerrarlo antes de publicar la 3.0.
    // V3.5 (06/09/2026): 0x30 -> 0x35. Ajustes lo muestra como "3.5".
    localparam [7:0] FPGA_VERSION = 8'h38;   // V3.8: OSD con color + actualizar el core desde el MSX (flash_bridge.v)
    // 27/09/2026 (regla de Albert): las lineas Tang solo reciben ARREGLOS y estos suben el tercer digito: 3.7.1, 3.7.2...
    // Puerto #29 (lectura) = FPGA_PATCH; el menu lo imprime tras "M.m" si vale 1..15 (un core sin el puerto devuelve FFh).
    // 3.7.1 = HRA x3 (sprites borde izq., R#26/27 por linea, colision 1/linea) + HMMM SCREEN 2 CMD=1 + menu EXTBIO/ASCII16-X.
    // 3.7.2 = + mandos HID genericos (Report ID, hat, sticks) por los USB-A (usb_pad_rid.v).
    // 3.7.3 = + host USB robusto ante mandos que responden rapido (alineacion al SYNC) y sin IZQUIERDA pegada tras enumerar.
    // 3.7.4 = + mux de lectura de la CPU (cpu_din) por grupos (timing) y navegador ordenado sin ocultos (menu).
    // 3.7.5 = + mando USB-A: un ZLP ya no deja IZQUIERDA clavada (el eje X del byte 0 se decide con el 2o byte; con
    //         Report ID el decodificador SNES suelta sus direcciones). En el menu devolvia 18 atras toda seleccion >= 18.
    //         Y (timing) las escrituras a los puertos de config #40-#46 y al mapper FC-FF con una etapa de registro,
    //         como el #44 de la V3.7: su cruce 54->27 era el peor camino de casi todos los dados rechazados.
    // 3.7.6 = + tres arreglos del upstream de HRA del 29/09 (V9968): el par del puerto 1 se cancela con cualquier lectura y
    // con una escritura al puerto 0 (Fleet Commander II), DIY con el origen arriba (ds4), paso de pixel registrado.
    // 3.8   = 01/10/2026: version NUEVA (Albert, 01/10: "ya sera una version nueva"): el OSD del BL616 con color
    //         (textdisp.v, BSRAM 2048x9 con tabla de atributos por fila) y el estado del core con version, ajustes,
    //         USB e idioma del menu; puente de la flash SPI para actualizar el core sin programador.
    localparam [7:0] FPGA_PATCH   = 8'd0;
    wire ver_req_r = (bus_iorq_n == 1'b0 && bus_m1_n == 1'b1 && bus_rd_n == 1'b0 && bus_addr[7:0] == 8'h2F);
    // 2Fh y 29h en UN solo termino del mux de cpu_din (un escalon mas en esa cadena costo -0,1 ns en el 60K): las dos
    // constantes se eligen por bus_addr[2] (2Fh = ...1111, 29h = ...1001) y la sintesis las pliega por bit.
    wire verpat_req_r = (bus_iorq_n == 1'b0 && bus_m1_n == 1'b1 && bus_rd_n == 1'b0 && bus_addr[7:3] == 5'b00101 && bus_addr[0] == 1'b1 && bus_addr[2] == bus_addr[1]);
    wire [7:0] verpat_data = bus_addr[2] ? FPGA_VERSION : FPGA_PATCH;   // 3.7.x

    // Puerto 0x2E — DIAGNOSTICO DEL RATON. Desde BASIC: PRINT HEX$(INP(&H2E))
    //   bit7 = hay raton USB detectado (typ==2 en alguno de los USB-A)
    //   bit6 = el MSX tiene seleccionado el PUERTO 2 (reg15 bit6)
    //   bit5 = nivel del pin 8 del puerto 2 (reg15 bit5) = el strobe
    //   bit4..2 = fase de la maquina del raton (0..7)
    //   bit1..0 = cuenta de informes USB recibidos (deberia cambiar al mover)
    // Lo que dice cada cosa si el raton no va:
    //   bit7=0            -> el USB no lo ha enumerado como raton
    //   bit7=1, bit6=0    -> el software esta sondeando el PUERTO 1, no el 2
    //   bit5 no cambia    -> el software no mueve el pin 8: no habla el protocolo
    //   bits1..0 quietos  -> el raton USB no envia informes
    wire mdbg_req_r = (bus_iorq_n == 1'b0 && bus_m1_n == 1'b1 && bus_rd_n == 1'b0 && bus_addr[7:0] == 8'h2E);
    wire [7:0] mouse_dbg = {msx_mouse_present, psg_reg15_port2, psgPB[5], msx_mouse_phase, mo_rep_cnt[1:0]};

    // Puerto 0x2D — DIAGNOSTICO DEL LADO USB. PRINT HEX$(INP(&H2D))
    //   bit7   = error de conexion en USB2
    //   bit6   = error de conexion en USB1
    //   bit5-4 = typ de USB2   (0 nada, 1 teclado, 2 RATON, 3 gamepad)
    //   bit3-2 = typ de USB1
    //   bit1-0 = cuenta de informes de CUALQUIER tipo (mueve el raton: si esto
    //            cambia, el USB habla; si no, no llega nada)
    // Este puerto existe porque el 0x2E solo dice "no hay raton" sin decir POR
    // QUE: con el typ a la vista se distingue "no enumerado" de "enumerado como
    // otra cosa" (que es lo que pasaba: los ratones sin subclass Boot se
    // clasificaban como gamepad).
    wire udbg_req_r = (bus_iorq_n == 1'b0 && bus_m1_n == 1'b1 && bus_rd_n == 1'b0 && bus_addr[7:0] == 8'h2D);
    wire [7:0] usb_dbg = {usb2_conerr, usb1_conerr, usb2_typ, usb1_typ, any_rep_cnt[1:0]};
    // V3.7b: puertos 2Ah-2Ch = DIAGNOSTICO DEL ARRANQUE DE LA DDR3 (la VRAM). Desde BASIC:
    //   ?INP(&H2C) AND 127  -> intentos de calibracion FALLIDOS (0 = a la primera)
    //   ?INP(&H2C) AND 128  -> 128 = la DDR3 esta calibrada
    //   ?INP(&H2B)*10       -> ms que tardo el intento que calibro (255 = 2,55 s o mas)
    //   ?INP(&H2A)/10       -> segundos del arranque a la calibracion (255 = 25 s o mas)
    // Es la respuesta al negro-desde-el-cargador de los dados 3557/3623/4139/4153.
    wire ddra_req_r = (bus_iorq_n == 1'b0 && bus_m1_n == 1'b1 && bus_rd_n == 1'b0 && bus_addr[7:0] == 8'h2A);
    wire ddrb_req_r = (bus_iorq_n == 1'b0 && bus_m1_n == 1'b1 && bus_rd_n == 1'b0 && bus_addr[7:0] == 8'h2B);
    wire ddrc_req_r = (bus_iorq_n == 1'b0 && bus_m1_n == 1'b1 && bus_rd_n == 1'b0 && bus_addr[7:0] == 8'h2C);
    reg [23:0] vddr_dbg_s1 = 24'd0, vddr_dbg_s2 = 24'd0;   // 2 FF desde el dominio g50 (cuasi-estaticos)
    always @ (posedge clk_54m) begin
        vddr_dbg_s1 <= {vddr_rdy_s[1], vddr_att, vddr_calib10, vddr_boot100};
        vddr_dbg_s2 <= vddr_dbg_s1;
    end
    // El mux de lectura de la CPU (cpu_din) esta al final del modulo, por grupos.


//    wire ex_bus_rd_n_test;
//    wire ex_bus_wr_n_test;
//    wire ex_bus_iorq_n_test;
//    wire ex_bus_mreq_n_test;
    reg ex_bus_rd_n_ff;
    reg ex_bus_wr_n_ff;
    reg ex_bus_iorq_n_ff;
    reg ex_bus_mreq_n_ff;
    localparam IDLE_ISO = 2'd0;
    localparam ACTIVE_ISO = 2'd1;
    localparam WAIT_ISO = 2'd2;
    reg [1:0] state_iso;
    reg [2:0] counter_iso;
    wire io_active;

    //assign ex_bus_rd_n = ( bus_rd_n | ex_bus_rd_n_ff | bus_disable);
    assign ex_bus_rd_n = bus_rd_n;
    //assign ex_bus_wr_n = ( bus_wr_n | ex_bus_wr_n_ff | bus_disable);
    assign ex_bus_wr_n = bus_wr_n;
    assign ex_bus_iorq_n = ( bus_iorq_n | bus_iorq_disable );
    assign ex_bus_mreq_n = ( bus_mreq_n | bus_mreq_disable );
    assign io_active = ( state_iso != IDLE_ISO ) ? 1 : 0;

    always @ ( posedge clk_108m ) begin
        if (~bus_reset_n) begin
            state_iso <= IDLE_ISO;
            ex_bus_rd_n_ff <= 1;
            ex_bus_wr_n_ff <= 1;
        end 
        else begin
            counter_iso = counter_iso + 3'd1;
            casex ({state_iso, counter_iso})
                {IDLE_ISO, 3'bxxx}: begin
                    ex_bus_rd_n_ff <= 1;
                    ex_bus_wr_n_ff <= 1;
                    counter_iso <= 3'd0;
                    if (bus_rd_n == 0 || bus_wr_n == 0 ) begin
                        state_iso <= ACTIVE_ISO;
                    end
                end
                {ACTIVE_ISO, 3'd2} : begin
                    ex_bus_rd_n_ff <= bus_rd_n;
                    ex_bus_wr_n_ff <= bus_wr_n;
                    state_iso <= WAIT_ISO;
                end
                {WAIT_ISO, 3'bxxx} : begin
                    if ( bus_rd_n == 1 && bus_wr_n == 1 ) begin
                        state_iso <= IDLE_ISO;
                    end
                end
            endcase
        end
    end

    // v2.1 60K: declarados AQUI (antes del FSM de waits) para poder alinear la
    // LIBERACION del wait al tren ACTIVO de la CPU en turbo. En el 60K el tren
    // 3m6 nace del dominio 27M (CLKDIV, fase arbitraria) y el 5m4 del 108M:
    // liberar con uno y consumir con el otro = carrera dependiente de fase
    // (en el TN20K ambos dominios salian ALINEADOS del mismo rPLL).
    reg  turbo = 1'b0;
    reg  turbo_eff = 1'b0;   // P1-iter.2: adelantado (el FSM de waits lo consume)
    wire clk_enable_cpu_54;
    wire clk_falling_cpu_54;

`ifdef ENABLE_WAIT
    wire wait_io;
    reg wait_io_ff = 1;

    reg [6:0] wait_cycles;
    reg [6:0] state_wait;
    localparam WAIT_IDLE = 7'd0;
    localparam WAIT_STATE1 = 7'd1;
    localparam WAIT_STATE2 = 7'd3;
    localparam WAIT_STATE3 = 7'd2;
    localparam WAIT_STATE4 = 7'd4;
    localparam WAIT_RELEASE = 7'd5;

    assign wait_io = wait_io_ff;

  `ifndef ENABLE_WAIT_ADAPTIVE
    always @ (posedge clk_54m) begin
        if (~bus_reset_n) begin
            state_wait <= WAIT_IDLE;
            wait_io_ff <= 1;
        end 
        else begin
            case (state_wait)
                WAIT_IDLE: begin
                    // P1-iter.2 (_64): handshake de LECTURA con la SDRAM, SOLO en
                    // turbo (turbo_eff) — a 5.37 los T-states (186ns) ya no tapan
                    // la latencia/contencion de la SDRAM externa (VDP+refresh) y
                    // la CPU leia basura ("se vuelve loco y se cuelga"; la nota
                    // iter.2 del port lo predijo). A 3.58 el termino es INERTE:
                    // camino validado byte-identico.
                    // P1-iter.2b (_66, DEFINITIVA): guard por NIVEL en TODA lectura
                    // SDRAM turbo, ciclos M1 incluidos. Post-mortem de las variantes:
                    //  - iter.2c (_67, flanco): bench 10-12 "MHz" de basura -> lecturas
                    //    corruptas. RETIRADA.
                    //  - iter.2d (_68, eximir M1): NI ARRANCA en turbo -> el T-state del
                    //    freno M1 NO cubre la latencia real de la SDRAM; los fetch salian
                    //    corruptos. RETIRADA.
                    // Moraleja: cuando ram_busy=1 los datos NO estan; no hay margen en el
                    // handshake. Ir mas alla de ~4.3 efectivos exige acelerar el propio
                    // controlador de memoria (P1c), no apostar en el guard.
`ifdef TURBO_SIN_GUARDA_SDRAM
                    // 🧪 sin el termino de ram_busy: queda EXACTAMENTE la
                    // condicion del MSXnano, que llega a 5,36 sin problemas.
                    if ( ram_write == 1 || (ex_bus_iorq_n == 0)&& (bus_rd_n == 0 || bus_wr_n == 0) ) begin
`else
                    if ( ram_write == 1 || (turbo_eff == 1 && bus_mreq_n == 0 && bus_rd_n == 0 && ram_busy == 1) || (ex_bus_iorq_n == 0)&& (bus_rd_n == 0 || bus_wr_n == 0) ) begin  // P2: sin Compatible Mode (= v1.9 nano)
`endif
                        wait_io_ff <= 0;
                        state_wait <= WAIT_STATE1;
                    end
                end
                // P1-iter.2b (_66): medir y liberar con el tren ACTIVO de la CPU
                // (la intencion declarada del v2.1). Con el release fijo a 3m6,
                // cada espera en turbo costaba hasta 280ns (cuantizacion del tren
                // lento) y z80bench leia 4.11 en vez de 5.37 (medido en HW). A
                // 3.58 (turbo_eff=0) las expresiones colapsan al 3m6 original:
                // camino validado byte-identico. OJO: pulsos SIN gatear (los
                // gateados estan parados por el propio wait -> deadlock).
                WAIT_STATE1: begin
                    if ( (turbo_eff ? clk_enable_5m4_54 : clk_enable_3m6_54) == 1 ) begin
                        state_wait <= WAIT_STATE2;
                    end
                end
                // P1-iter.2: en turbo, ademas, NO liberar con la SDRAM ocupada.
                WAIT_STATE2: begin
`ifdef TURBO_SIN_GUARDA_SDRAM
                    if ( (turbo_eff ? clk_falling_5m4_54 : clk_falling_3m6_54) == 1 ) begin
`else
                    if ( (turbo_eff ? clk_falling_5m4_54 : clk_falling_3m6_54) == 1 && (turbo_eff == 0 || ram_busy == 0) ) begin
`endif
                        wait_io_ff <= 1;
                        state_wait <= WAIT_STATE3;
                    end
                end
                WAIT_STATE3: begin
                    if ( bus_rd_n == 1 && bus_wr_n == 1) begin
                        state_wait <= WAIT_IDLE;
                    end
                end
            endcase
        end
    end
  `else
    always @ (posedge clk_54m) begin
        if (~bus_reset_n) begin
            state_wait <= WAIT_IDLE;
            wait_io_ff <= 1;
        end 
        else begin
            case (state_wait)
                WAIT_IDLE: begin
                    if ( (ex_bus_iorq_n == 0 || bus_mreq_n == 0 ) && (bus_rd_n == 0 || bus_wr_n == 0) ) begin
                        wait_io_ff <= 0;
                        wait_cycles <= 7'd6;
                        state_wait <= WAIT_STATE1;
                    end
                end
                WAIT_STATE1: begin
                    wait_cycles <= wait_cycles - 1;
                    if ( wait_cycles == 0 ) begin
                        state_wait <= WAIT_STATE2;
                    end
                end
                WAIT_STATE2: begin
                    if ( ram_busy == 0 && clk_enable_3m6_54 == 1 ) begin
                        state_wait <= WAIT_STATE3;
                    end
                end
                WAIT_STATE3: begin
                    // v2.2: semantica v1.9 restaurada — con la fase 27<->54
                    // alineada (clk27_align) la disciplina original es valida
                    if ( clk_falling_3m6_54 == 1 ) begin
                        wait_io_ff <= 1;
                        state_wait <= WAIT_STATE4;
                    end
                end
                WAIT_STATE4: begin
                    if ( bus_rd_n == 1 && bus_wr_n == 1) begin
                        state_wait <= WAIT_IDLE;
                    end
                end
            endcase
        end
    end
  `endif

`endif

    // v1.9: los wires de cadencia de CPU estan declarados ARRIBA (v2.1) junto
    // al FSM de waits; se asignan en el bloque de turbo de abajo.

`ifdef ENABLE_M1_WAIT
    // ===== STANDALONE M1 wait-state generator (frenado a ~100% MSX) =====
    // A real MSX inserts exactly 1 wait-state in every M1 (opcode-fetch) cycle.
    // The goauld got this from the MSX board via ex_bus_wait_n; standalone tied
    // ex_bus_wait_n=1 (top.v ~95), losing the brake -> CPU ran ~16% too fast.
    //
    // MECHANISM: GATE the CPU clock-enable, do NOT use WAIT_n.
    // The earlier WAIT_n version released the pulse at the T1->T2 boundary, so it
    // was already high when the core sampled WAIT_n inside T2 -> no wait inserted
    // (bench stayed at 116%). Instead we mirror the proven wait_io stall: mask
    // exactly one full CPU-clock period (one clk_enable_cpu_54 + one
    // clk_falling_cpu_54, i.e. the ACTIVE cadence) per M1 opcode fetch. Skipping one
    // removes exactly one T-state of progress = one wait-state, independent of
    // the core's internal T-state sampling. RFSH is T3/T4 with M1_n already high
    // (t80.vhd:1077), so refresh cycles are NOT slowed. clk_54m domain.
    reg  wait_m1 = 1'b1;            // active-high CPU clock-enable allow (0 = stall)
    reg  bus_m1_n_prev_54 = 1'b1;
    reg  m1_active = 1'b0;          // currently inserting the wait for this M1
    reg  m1_masked_en = 1'b0;       // masked one clk_enable pulse this wait
    reg  m1_masked_fall = 1'b0;     // masked one clk_falling pulse this wait

    always @ (posedge clk_54m) begin
        if (~bus_reset_n) begin
            wait_m1          <= 1'b1;
            bus_m1_n_prev_54 <= 1'b1;
            m1_active        <= 1'b0;
            m1_masked_en     <= 1'b0;
            m1_masked_fall   <= 1'b0;
        end else begin
            bus_m1_n_prev_54 <= bus_m1_n;
            if (!m1_active) begin
                // Falling edge of M1_n = new opcode fetch -> start one wait.
                if (bus_m1_n_prev_54 == 1'b1 && bus_m1_n == 1'b0) begin
                    m1_active      <= 1'b1;
                    wait_m1        <= 1'b0;   // stall CPU clock from next cycle
                    m1_masked_en   <= 1'b0;
                    m1_masked_fall <= 1'b0;
                end
            end else begin
                // While stalled (wait_m1==0) the coincident enable/falling pulses
                // are masked out of the CPU clock-enable. Track one of each, then
                // release -> exactly one CPU-clock period (one T-state) inserted.
                // v1.9: tracks the MUXED cadence so the wait is exactly 1 T-state
                // in both 3.6 (normal) and 5.37 (turbo) modes.
                if (clk_enable_cpu_54)  m1_masked_en   <= 1'b1;
                if (clk_falling_cpu_54) m1_masked_fall <= 1'b1;
                if ((m1_masked_en  || clk_enable_cpu_54) &&
                    (m1_masked_fall || clk_falling_cpu_54)) begin
                    wait_m1   <= 1'b1;   // release on next cycle
                    m1_active <= 1'b0;
                end
            end
        end
    end
`endif

    // ===== v1.9-fh: retraso de power-on para el ESP-01S (WiFi) =====
    // El INIT del driver ESP corre en el escaneo de slots ~1-2s tras dar
    // corriente, pero el ESP-01S tarda ~3-5s en arrancar: quedaba instalado
    // "sin ESP" (discovery UNAPI = 0 implementaciones) hasta re-init manual
    // via el setup W. Retener el Z80 en reset ~3s SOLO en el power-on da
    // tiempo al ESP y el INIT lo encuentra a la primera. El contador SATURA
    // y no se re-arma: los soft-reset siguen siendo instantaneos (regla de la
    // megaram) y el coste real es ~1.5-2s extra (el stream de flash ya tapa
    // parte). Sin ENABLE_WIFI no aplica.
    // El LANZADOR POR SPI DEL ESP32-S3 (destinos 2 y 3) se RETIRA el 25/08.
    // Nunca llego a leer la SD de forma fiable y el enlace SPI resulto
    // intermitente; su sustituto es el iosys_bl616 de TangCore por UART, que
    // ya pinta y detecta el core (core_id=77 validado en placa).
    // Con el se van launcher_svc, sdc_bridge, mcu_spi, hid y sysctrl:
    // ~3.325 LUT y ~4.749 registros, y -- lo que mas importa -- CINCO
    // multiplexores que vivian en el bus del V9968, en clk_86.

`ifdef ENABLE_WIFI
    reg [26:0] esp_boot_cnt = 0;
    reg        esp_boot_tmr = 0;
    always @(posedge clk_27m) begin
        if (!esp_boot_tmr) begin
            if (esp_boot_cnt == 27'd81000000)   // ~3.0s @ 27 MHz
                esp_boot_tmr <= 1;
            else
                esp_boot_cnt <= esp_boot_cnt + 1'b1;
        end
    end
    // Sin lanzador, el temporizador vuelve a ser lo que era: dar tiempo al ESP
    // antes de soltar al Z80.
    wire esp_boot_ok = esp_boot_tmr;
`else
    wire esp_boot_ok = 1'b1;
`endif

    // ===== S1990 del turboR (puertos E4h-E7h) =====
    // Se declara aqui porque el mux de lectura de E/S vive mas arriba en el
    // fichero; la instancia va abajo, junto al resto de dispositivos.
    wire [7:0] s1990_dout;
    wire       s1990_req;
    wire       s1990_turbo_set, s1990_turbo_val;

    // ===== Turbo mode toggle (F11) =====
    // Default turbo=0 -> M1 wait active -> ~100% real-MSX speed (3.58MHz behaviour).
    // Press F11 (USB HID usage 0x44 = keyboard[68]) to toggle. v1.9: turbo=1 switches
    // the CPU cadence to 5.37 MHz (WSX-style) while the per-M1 wait STAYS active, like
    // the real T9769 does at 5.37 MHz -> benchmarks report ~5.37 (150%). (The v1.8
    // "bypass M1 wait" turbo stacked on the 5.4 clock read as ~6.2 MHz on HW.)
    // Toggle survives MSX soft-reset; powers on in real-MSX mode. LED5 shows the state.
    // NOTE: F12 is captured by the BL616 FPGA-Companion firmware (its OSD) and never
    // reaches the FPGA, so F11 (which does reach it, verified on HW) is used instead.
    // (reg turbo declarado arriba, v2.1)
    // P1 (receta MSXnano v1.9 ce46ef9): los eventos escriben `turbo` DIRECTO y el
    // conmutado seguro lo hace turbo_eff (mas abajo): limite de T-estado limpio
    // (fix de cadencia del nano, validado en su HW) COMBINADO con el guard de
    // bus/memoria en reposo propio del 60K (SDRAM externa: no conmutar con un
    // acceso en vuelo). El esquema turbo_req anterior queda sustituido.
`ifdef ENABLE_TURBOR_ID
    // clk_27m -> clk_54m. El pulso se convierte en un TOGGLE que sobrevive al
    // cruce; el valor viaja al lado y se muestrea cuando el toggle cambia (para
    // entonces lleva ciclos estable).
    reg s1990_tg = 1'b0, s1990_val_h = 1'b0;
    always @(posedge clk_27m) if (s1990_turbo_set) begin
        s1990_tg    <= ~s1990_tg;
        s1990_val_h <= s1990_turbo_val;
    end
    reg s1990_tg_s1 = 1'b0, s1990_tg_s2 = 1'b0, s1990_tg_s3 = 1'b0;
    reg s1990_val_s1 = 1'b0, s1990_val_s2 = 1'b0;
    always @(posedge clk_54m) begin
        s1990_tg_s1 <= s1990_tg;   s1990_tg_s2 <= s1990_tg_s1;  s1990_tg_s3 <= s1990_tg_s2;
        s1990_val_s1 <= s1990_val_h; s1990_val_s2 <= s1990_val_s1;
    end
`endif

    reg boot_done = 1'b0;   // 1 tras la PRIMERA (fria) salida de reset; sobrevive warm resets
    reg f11_s0  = 1'b0;
    reg f11_s1  = 1'b0;
    reg f11_prev= 1'b0;
    always @ (posedge clk_54m) begin
        f11_s0   <= keyboard[68];   // sync HID F11 state into clk_54m domain
        f11_s1   <= f11_s0;
        f11_prev <= f11_s1;
`ifdef ENABLE_TURBO
        if (f11_s1 & ~f11_prev)     // rising edge = F11 pressed
            turbo <= ~turbo;        // toggle real-MSX <-> turbo
`endif
`ifdef ENABLE_TURBOR_ID
        // Tercera fuente: CHGCPU por el S1990. El software pide "R800" y aqui
        // eso significa turbo. Llega de clk_27m, asi que se cruza por TOGGLE
        // (un pulso de un ciclo de 27 MHz podria no verse desde 54, o verse dos
        // veces). FIJA el valor, no conmuta: el software dice cual quiere.
        if (s1990_tg_s2 != s1990_tg_s3)
            turbo <= s1990_val_s2;
`endif
        // v1.9: control software Panasonic — OUT &H41,n con el dispositivo 8
        // seleccionado (decode pana41_wr junto al bloque config). bit0 activo-bajo:
        // 0 = turbo 5.37 MHz, 1 = 3.58. Puesto tras el F11: si coinciden en el
        // mismo ciclo gana el software (en el T9769 real el puerto es el unico control).
`ifdef ENABLE_TURBO
        if (pana41_wr)
            turbo <= ~cpu_dout[0];
`endif
        // v1.9: "Boot Turbo" persistido (ajuste del menu, puerto #45). Siembra el
        // turbo durante la ventana config_init del stream de flash. Va el ULTIMO
        // del bloque de eventos: domina sobre F11/puerto durante el boot.
        // v1.9b FIX pantalla-negra Save&Reset-con-turbo: el boot-turbo (5.37) SOLO
        // se aplica en arranque en FRIO (boot_done=0). En warm reset -> 3.58 (= un
        // Save&Reset normal); el boot-turbo entra al PROXIMO encendido.
`ifdef ENABLE_TURBO
        if (config_init)
            turbo <= (~boot_done && !s2_press && config_sig[4] == 8'h54) ? 1'b1 : 1'b0;
        // estado conocido de `turbo` en cualquier reset (mirror del cold boot). Ultimo = prioridad.
        if (~bus_reset_n)
            turbo <= 1'b0;
`endif
    end
    // boot_done: se pone a 1 la primera vez que el CPU sale de reset (arranque en
    // frio) y NO se borra nunca (sin clausula de reset -> sobrevive warm resets;
    // GSR lo inicia a 0 al encender). Discriminador frio/warm del boot-turbo.
    always @ (posedge clk_54m)
        if (bus_reset_n & reset3_n & flash_idle & esp_boot_ok & ~config_init)
            boot_done <= 1'b1;   // ~config_init: no marcar boot_done durante la siembra

    // ===== v1.9 Panasonic-WSX turbo: 5.37 MHz CPU cadence =====
    // /20 divider on 108 MHz -> 5.40 MHz base cadence + "period swallow" trim ->
    // EXACT WSX 5.369318 MHz (see below). The sound chips keep the /30
    // clk_enable_3m6_27 (untouched). At turbo=0 the CPU uses the ORIGINAL
    // clk_enable_3m6_54 verbatim (3.58 behaviour byte-identical). NOTE: NO
    // ram_busy handshake yet, so if HW shows corruption during active display,
    // add the handshake (dormant ENABLE_WAIT_ADAPTIVE, top.v ~707) in iter.2.
    //
    // Divisor /20 PURO (mitades de 10 ciclos, pares: fase constante vs clk_54m).
    // NOTA: durante el desarrollo se probo un divisor fraccionario (17x10+1x11,
    // 5.37 directo reformando el reloj) y se descarto; los "cuelgues" que se le
    // atribuyeron resultaron ser un falso contacto del teclado, pero el esquema
    // /20 puro + trago (abajo) es mas simple, conserva las fases 108->54
    // validadas y da el 5.37 EXACTO. Validado en HW (juegos/DOS en turbo).
    reg [4:0] div20_cnt;
    reg       clk_5m4_internal;
    always @(posedge clk_108m or negedge bus_reset_n) begin
        if (~bus_reset_n) begin div20_cnt <= 0; clk_5m4_internal <= 0; end
        else if (div20_cnt >= 5'd9) begin clk_5m4_internal <= ~clk_5m4_internal; div20_cnt <= 0; end
        else div20_cnt <= div20_cnt + 1;
    end
    wire clk_enable_5m4_raw, clk_falling_5m4_raw;
    reg  s5m4_a, s5m4_b;
    always @(posedge clk_54m) begin s5m4_a <= clk_5m4_internal; s5m4_b <= s5m4_a; end
    assign clk_enable_5m4_raw  = (s5m4_b == 0 && s5m4_a == 1);
    assign clk_falling_5m4_raw = (s5m4_b == 1 && s5m4_a == 0);

    // Ajuste EXACTO a 5.37: "trago" de periodo. De cada 176 periodos de 5.4 MHz
    // se enmascara 1 completo (su enable Y su falling, en pareja) ->
    // 5.4 MHz * 175/176 = 5 369 318 Hz = el turbo WSX exacto (315/88 * 1.5 MHz).
    // Mismo mecanismo probado que los waits M1/IO (saltar pulsos de enable en el
    // dominio 54), SIN tocar la forma del reloj 5m4 ni sus fases 108->54. El CPU
    // solo percibe una pausa de 1 T-state cada ~33 us; la alternancia
    // enable/falling se conserva (se traga la pareja completa).
    reg [7:0] pana_per_cnt   = 0;
    reg       pana_skip_pend = 0;   // enmascarando el falling del periodo tragado
    wire      pana_skip_now  = (pana_per_cnt == 8'd175) && clk_enable_5m4_raw;
    always @(posedge clk_54m) begin
        if (~bus_reset_n) begin
            pana_per_cnt   <= 0;
            pana_skip_pend <= 0;
        end else begin
            if (clk_enable_5m4_raw) begin
                if (pana_per_cnt == 8'd175) begin
                    pana_per_cnt   <= 0;
                    pana_skip_pend <= 1;    // el falling de ESTE periodo tambien se traga
                end else
                    pana_per_cnt <= pana_per_cnt + 1'b1;
            end
            if (pana_skip_pend && clk_falling_5m4_raw)
                pana_skip_pend <= 0;
        end
    end
    wire clk_enable_5m4_54  = clk_enable_5m4_raw  & ~pana_skip_now;
    wire clk_falling_5m4_54 = clk_falling_5m4_raw & ~pana_skip_pend;
    // ===== v1.9: conmutado de cadencia SIN glitch =====
    // El mux elige entre dos cadencias de FASE INDEPENDIENTE (3.6 del /30, 5.37
    // del /20). Conmutar sobre `turbo` crudo a mitad de T-estado puede entregar
    // al Z80 dos ENABLE (o dos FALLING) seguidos sin pareja -> opcode mal
    // latcheado -> cuelgue (el F11 en el menu del nano). turbo_eff (el select
    // REAL) solo adopta `turbo` cuando AMBAS cadencias estan bajas Y el CPU no
    // esta en ningun wait (receta v1.9, validada en el TN20K) Y ADEMAS el bus
    // Z80 y la SDRAM estan en reposo (guard 60K: memoria externa, no conmutar
    // con un acceso en vuelo). En reset adopta directo (semilla del boot-turbo).
    wire cadence_safe = (bus_clk_3m6 == 1'b0 && bus_clk_3m6_54 == 1'b0) &&
                        (s5m4_a == 1'b0 && s5m4_b == 1'b0);
    // v1.9b: un warm reset EN CURSO debe CRUZAR la entrada del reset a 3.58
    // (la grabacion en flash tarda decenas de ms con bus_reset_n aun alto).
    wire warm_reset_pending = flash_write_busy | config_reset_req;
    // _177: /WAIT del puerto CPU del V9968 (glue en clk_86) re-sincronizado
    // al dominio del T80 con 2FF. Latencia de asercion total ~60-70ns desde
    // la caida de IORQ — dentro de la ventana de muestreo de WAIT del Z80
    // incluso en turbo (T=186ns). Seguro por diseno: el glue lo gatea al
    // ciclo I/O del VDP y lleva timeout fail-open (~12us); el stall ya no
    // puede matar de hambre al refresco de la SDRAM (autonomo desde _175).
    wire v68_wait86_n;
    reg [1:0] v68_wait_s = 2'b11;
    always @(posedge clk_54m) v68_wait_s <= {v68_wait_s[0], v68_wait86_n};
    wire vdp_wait54_n = v68_wait_s[1];
    // V3.6: DMA de la SD (sd_dma.sv). frz = CPU congelada con el bus en reposo:
    // el puerto de RAM de la CPU pasa a la DMA por el camino del streamer de la
    // flash (stream_*, mas abajo). Se declaran aqui porque el T80 y el mux de
    // ram_addr los usan antes de la instancia (Gowin crea implicitos de 1 bit).
    wire        dma_frz;
    wire        dma_active;
    wire        dma_rfsh_ok;
    wire        dma_ram_req;
    wire [23:0] dma_ram_addr;       // 24/09/2026: 24 bits (bit 23 = fila 11 de la SDRAM, megaram de 8 MB)
    wire [7:0]  dma_ram_din;
    // (reg turbo_eff adelantado junto al FSM de waits, P1-iter.2)
    always @ (posedge clk_54m) begin
        if (!(bus_reset_n & reset3_n & flash_idle & esp_boot_ok))
            turbo_eff <= turbo;                                 // en reset: sigue a turbo (semilla / 0)
        else if (cadence_safe & wait_io & wait_m1
                 & bus_rd_n & bus_wr_n & bus_mreq_n & ex_bus_iorq_n & (ram_busy == 0))
            turbo_eff <= warm_reset_pending ? 1'b0 : turbo;     // corriendo: 3.58 si hay warm-reset pendiente
    end
    // CPU cadence mux: turbo_eff (conmutado sin glitch) elige 5.37; si no, la 3.6 intacta.
    assign clk_enable_cpu_54  = turbo_eff ? clk_enable_5m4_54  : clk_enable_3m6_54;
    assign clk_falling_cpu_54 = turbo_eff ? clk_falling_5m4_54 : clk_falling_3m6_54;

    // ----- M1-wait fallback (divisor) -----
    // If on real HW the benchmark still does not land near 100% with the WAIT_n
    // brake above, comment out `define ENABLE_M1_WAIT and instead SLOW the CPU
    // clock by changing the 108MHz divider at top.v ~223 from /30 (3.6MHz) to
    // /35 (~3.09MHz): replace `if (div30_cnt == 5'd14)` with a half-period of
    // ~17.5 -> alternate 17/18, e.g.:
    //     reg div_tgl;  // toggles every edge to alternate 17/18
    //     if (div30_cnt == (div_tgl ? 5'd17 : 5'd16)) begin
    //         clk_3m6_internal <= ~clk_3m6_internal; div30_cnt <= 0; div_tgl <= ~div_tgl;
    //     end else div30_cnt <= div30_cnt + 1;
    // This lowers the clock instead of inserting a wait (less authentic, but a
    // guaranteed % knob). Do NOT enable both at once.

    wire update_addr;
    G80a  #(
        .Mode    (0),     // 0 => Z80, 1 => Fast Z80, 2 => 8080, 3 => GB
        //.T2Write (0),     //0 => WR_n active in T3, /=0 => WR_n active in T2
        .IOWait   (1)      // 0 => Single I/O cycle, 1 => Std I/O cycle
    ) cpu1 (
        .RESET_n   (bus_reset_n & reset3_n & flash_idle & esp_boot_ok),
        .CLK_n     (clk_54m),
    `ifdef ENABLE_WAIT
      `ifdef ENABLE_M1_WAIT
        // v1.9: M1 wait is NOT bypassed in turbo (real WSX keeps it at 5.37 MHz);
        // the speed change comes only from the 3.6/5.37 cadence mux.
        .clk_enable (clk_enable_cpu_54 & wait_io & wait_m1 & ~dma_frz),
        .clk_falling (clk_falling_cpu_54 & wait_io & wait_m1 & ~dma_frz),
      `else
        .clk_enable (clk_enable_3m6_54 & wait_io & ~dma_frz),
        .clk_falling (clk_falling_3m6_54 & wait_io & ~dma_frz),
      `endif
    `else
      `ifdef ENABLE_M1_WAIT
        // (inactive branch) v1.9 semantics: cadence mux + M1 wait always on
        .clk_enable (clk_enable_cpu_54 & wait_m1 & ~dma_frz),
        .clk_falling (clk_falling_cpu_54 & wait_m1 & ~dma_frz),
      `else
        .clk_enable (clk_enable_3m6_54 & ~dma_frz),
        .clk_falling (clk_falling_3m6_54 & ~dma_frz),
      `endif
    `endif
    `ifdef ENABLE_WIFI
      `ifndef ENABLE_WAIT_ADAPTIVE
        .WAIT_n    (bus_wait_n & wait_uart & opl4pcm_wait_n & vdp_wait54_n),
      `else
        .WAIT_n    (wait_uart & opl4pcm_wait_n & vdp_wait54_n),
      `endif
    `else
      `ifndef ENABLE_WAIT_ADAPTIVE
        .WAIT_n    (bus_wait_n & opl4pcm_wait_n & vdp_wait54_n),
      `else
        .WAIT_n    (opl4pcm_wait_n & vdp_wait54_n),
      `endif
    `endif
    `ifdef ENABLE_V9958
        .INT_n     (bus_int_n & vdp_int & y8950_int_n & opl4_int_n),  // _81 Y8950 + _108 OPL4
    `else
        .INT_n     (bus_int_n & y8950_int_n & opl4_int_n),
    `endif
        .NMI_n     (1),
        .BUSRQ_n   (1),
        .M1_n      (bus_m1_n),
        .MREQ_n    (bus_mreq_n),
        .IORQ_n    (bus_iorq_n),
        .RD_n      (bus_rd_n),
        .WR_n      (bus_wr_n),
        .RFSH_n    (bus_rfsh_n),
        .HALT_n    ( ),
        .BUSAK_n   ( ),
        .A         (bus_addr),
        .update_addr(update_addr),
        .DI         (cpu_din),
        .DO         (cpu_dout),
        .Data_Reverse (bus_data_reverse)
    );

    //slots decoding
    reg [7:0] ppi_port_a = 8'h00;
    wire ppi_req_r;
    wire ppi_req_w;
    wire [1:0] pri_slot;
    wire [3:0] pri_slot_num;
    wire [3:0] page_num;

    //----------------------------------------------------------------
    //-- PPI(8255) / primary-slot
    //----------------------------------------------------------------
    assign ppi_req_r = (bus_addr[7:0] == 8'ha8 && bus_iorq_n == 0 && bus_m1_n == 1 && bus_rd_n == 0)? 1:0;
    assign ppi_req_w = (bus_addr[7:0] == 8'ha8 && bus_iorq_n == 0 && bus_m1_n == 1 && bus_wr_n == 0)? 1:0;

    always @ (posedge clk_27m or negedge bus_reset_n) begin
        if ( bus_reset_n == 0)
            ppi_port_a <= 8'h00;
        else begin
            if (ppi_req_w == 1 ) begin
                ppi_port_a <= cpu_dout;
            end
        end
    end

    //expanded slots 0 & 3
    reg [7:0] exp_slot0;
    wire [1:0] exp_slot0_page;
    wire [3:0] exp_slot0_num;
    reg exp_slot0_req_r;
    reg exp_slot0_req_w;
    reg [7:0] exp_slotx;
    wire [1:0] exp_slotx_page;
    wire [3:0] exp_slotx_num;
    reg exp_slotx_req_r;
    reg exp_slotx_req_w;
    wire xffff;
    reg xffh;
    reg xffl;
    always @ (posedge clk_54m) begin
        xffh <= bus_addr[15:8] == 8'hff;
        xffl <= bus_addr[7:0] == 8'hff;
        exp_slot0_req_w <= ( bus_mreq_n == 0 && bus_wr_n == 0 && xffh == 1 && xffl == 1 && pri_slot_num[0] == 1 ) ? 1: 0;
        exp_slot0_req_r <= ( bus_mreq_n == 0 && bus_rd_n == 0 && xffh == 1 && xffl == 1 && pri_slot_num[0] == 1 ) ? 1: 0;
        exp_slotx_req_w <= ( bus_mreq_n == 0 && bus_wr_n == 0 && xffh == 1 && xffl == 1 && pri_slot_num[SD_SLOT] == 1 ) ? 1: 0;
        exp_slotx_req_r <= ( bus_mreq_n == 0 && bus_rd_n == 0 && xffh == 1 && xffl == 1 && pri_slot_num[SD_SLOT] == 1 ) ? 1: 0;
    end
    //assign xffff = ( bus_addr == 16'hffff ) ? 1 : 0;
    assign xffff = xffh & xffl;

//    assign exp_slotx_req_w = ( bus_mreq_n == 0 && bus_wr_n == 0 && xffff == 1 && pri_slot_num[0] == 1 ) ? 1: 0;
//    assign exp_slotx_req_r = ( bus_mreq_n == 0 && bus_rd_n == 0 && xffff == 1 && pri_slot_num[0] == 1 ) ? 1: 0;

    // slot #0
    always @ (posedge clk_27m or negedge bus_reset_n) begin
        if ( bus_reset_n == 0 )
            exp_slot0 <= 8'h00;
        else begin
            if (exp_slot0_req_w == 1 ) begin
                exp_slot0 <= cpu_dout;
            end
        end
    end

    // slot #3
    always @ (posedge clk_27m or negedge bus_reset_n) begin
        if ( bus_reset_n == 0 )
            exp_slotx <= 8'h00;
        else begin
            if (exp_slotx_req_w == 1 ) begin
                exp_slotx <= cpu_dout;
            end
        end
    end

    // slots decoding
    assign pri_slot = ( bus_addr[15:14] == 2'b00) ? ppi_port_a[1:0] :
                      ( bus_addr[15:14] == 2'b01) ? ppi_port_a[3:2] :
                      ( bus_addr[15:14] == 2'b10) ? ppi_port_a[5:4] :
                                             ppi_port_a[7:6];

    assign pri_slot_num = ( pri_slot == 2'b00 ) ? 4'b0001 :
                          ( pri_slot == 2'b01 ) ? 4'b0010 :
                          ( pri_slot == 2'b10 ) ? 4'b0100 :
                                                  4'b1000;

    assign page_num = ( bus_addr[15:14] == 2'b00) ? 4'b0001 :
                      ( bus_addr[15:14] == 2'b01) ? 4'b0010 :
                      ( bus_addr[15:14] == 2'b10) ? 4'b0100 :
                                                    4'b1000;
    assign exp_slot0_page = ( bus_addr[15:14] == 2'b00) ? exp_slot0[1:0] :
                            ( bus_addr[15:14] == 2'b01) ? exp_slot0[3:2] :
                            ( bus_addr[15:14] == 2'b10) ? exp_slot0[5:4] :
                                                          exp_slot0[7:6];

    assign exp_slot0_num = ( exp_slot0_page == 2'b00 ) ? 4'b0001 :
                           ( exp_slot0_page == 2'b01 ) ? 4'b0010 :
                           ( exp_slot0_page == 2'b10 ) ? 4'b0100 :
                                                         4'b1000;

    assign exp_slotx_page = ( bus_addr[15:14] == 2'b00) ? exp_slotx[1:0] :
                            ( bus_addr[15:14] == 2'b01) ? exp_slotx[3:2] :
                            ( bus_addr[15:14] == 2'b10) ? exp_slotx[5:4] :
                                                          exp_slotx[7:6];

    assign exp_slotx_num = ( exp_slotx_page == 2'b00 ) ? 4'b0001 :
                           ( exp_slotx_page == 2'b01 ) ? 4'b0010 :
                           ( exp_slotx_page == 2'b10 ) ? 4'b0100 :
                                                         4'b1000;

    reg slot0_req_r;
    reg slotx_req_r;
    always @ (posedge clk_54m) begin
        slot0_req_r <= ( bus_mreq_n == 0 && bus_rd_n == 0 && pri_slot_num[0] == 1 ) ? 1 : 0;
        slotx_req_r <= ( ( config_enable_mapper3 == 1 || config_enable_megaram3 == 1 || config_enable_sdcard == 1 ) && bus_mreq_n == 0 && bus_rd_n == 0 && pri_slot_num[SD_SLOT] == 1 ) ? 1 : 0;
    end

`ifdef ENABLE_BIOS
    //bios
    reg bios_req;
    wire [7:0] bios_dout;
    always @ (posedge clk_54m) begin
        bios_req <= ( bus_mreq_n == 0 && bus_rd_n == 0 && pri_slot_num[0] == 1 && exp_slot0_num[0] == 1) ? 1 : 0;
    end

    //subrom
    reg subrom_req;
    wire [7:0] subrom_dout;
    always @ (posedge clk_54m) begin
        subrom_req <= ( bus_mreq_n == 0 && bus_rd_n == 0 && pri_slot_num[SD_SLOT] == 1 && page_num[0] == 1 && exp_slotx_num[1] == 1 ) ? 1 : 0;
    end

    //msx logo
    reg msx_logo_req;
    wire [7:0] msx_logo_dout;
    always @ (posedge clk_54m) begin
        msx_logo_req <= ( bus_mreq_n == 0 && bus_rd_n == 0 && page_num[1] == 1 && pri_slot_num[SD_SLOT] == 1 && exp_slotx_num[1] == 1 ) ? 1 : 0;
    end

    //subrom + logo
    reg subrom_logo_req;
    always @ (posedge clk_54m) begin
        subrom_logo_req <= ( bus_mreq_n == 0 && bus_rd_n == 0 && (page_num[0] == 1 || page_num[1] == 1) && pri_slot_num[SD_SLOT] == 1 && exp_slotx_num[1] == 1 ) ? 1 : 0;
    end

    // V3.5: SEGUNDA PAGINA DEL MENU. El menu deja de desempaquetarse en RAM y
    // corre desde ROM como cartucho de 32 KB: pagina 1 (4000-7FFF) = la ROM de
    // siempre del pack (0x6C000, con la FM-BIOS), pagina 2 (8000-BFFF) = una
    // ventana NUEVA de 16 KB en la posicion que ocupaba la primera mitad del
    // driver KANJI (pack 0x70000). El driver KANJI (CALL KANJI de BASIC, slot
    // 0-1) desaparece del MSXimus; la FUENTE kanji (256 KB por puertos) sigue.
    // Misma expresion que subrom_logo_req (slot 3-1) pero solo pagina 2.
    reg menu2_req;
    always @ (posedge clk_54m) begin
        menu2_req <= ( bus_mreq_n == 0 && bus_rd_n == 0 && page_num[2] == 1 && pri_slot_num[SD_SLOT] == 1 && exp_slotx_num[1] == 1 ) ? 1 : 0;
    end


`else

    wire bios_req;
    wire [7:0] bios_dout;
    wire subrom_req;
    wire [7:0] subrom_dout;
    wire msx_logo_req;
    wire [7:0] msx_logo_dout;
    wire menu2_req;
    wire subrom_logo_req;

`endif

    //logo ROM: SIEMPRE (v3.0 — estaba atrapado en ENABLE_WIFI; es del menu, no del WiFi)
`ifdef ENABLE_WIFI

    //wifi driver
    reg wifi_req;
    always @ (posedge clk_54m) begin
        wifi_req <= ( bus_mreq_n == 0 && bus_rd_n == 0 && page_num[1] == 1 && pri_slot_num[0] == 1 && exp_slot0_num[2] == 1 ) ? 1 : 0;
    end
`endif

    //logo ROM (FREE16KB del pack @0x7C000) en slot 0-3 pagina 1: pantalla de
    //marca del menu (rutina+imagen autocontenidas; el menu la llama con CALLF)
    reg logo_req;
    always @ (posedge clk_54m) begin
        logo_req <= ( bus_mreq_n == 0 && bus_rd_n == 0 && page_num[1] == 1 && pri_slot_num[0] == 1 && exp_slot0_num[3] == 1 ) ? 1 : 0;
    end

`ifdef ENABLE_WIFI
    //uart
    wire uart_req;
    wire wait_uart;
    wire [7:0] uart_dout;

    assign uart_req = (bus_addr[7:1] == 7'b0000011 && bus_iorq_n == 0 && bus_m1_n == 1 && bus_rd_n == 0)? 1 : 0; // ESP ports 06-07h

    // F1 (_73): la UART va al BL616 ONBOARD (firmware UNAPI propio, repo
    // BL616-UNAPI-Firmware). RX = pad bl616_jtagsel (V14 <- GPIO28 TX del
    // BL616, PULL_UP = idle UART correcto). TX = pad spi_irqn (U15 -> GPIO27
    // RX del BL616), robado al companion (sacrificado en F1). Baud del core:
    // 27M/31 = 870968; el firmware BL616 va a 869565 (-0.16%).
    wire bl616_uart_tx_w;
    // _95: BUS REGISTRADO (patron _91) — uwifi vive en clk_27m y decodificaba
    // el bus del T80 (lanzado en bajada de 54M) directo: camino de medio
    // ciclo que perdio la loteria de placement en la _95 (p1r1: -0.905 en
    // cpu1/RD->my_rx_state). Flop directo en 27M = cono trivial; el modulo
    // ve el bus 1 ciclo de 27M tarde (37ns, nada frente a los ~560ns del
    // ciclo I/O en turbo). wait_o llega <100ns tras IORQ: el T80 muestrea
    // /WAIT a >=186ns — margen sobrado. Sin tocar wifi_lite.vhd.
    reg        w27_iorq_n, w27_wr_n, w27_rd_n;
    reg [15:0] w27_addr;
    reg [7:0]  w27_din;
    always @(posedge clk_27m) begin
        w27_iorq_n <= bus_iorq_n;
        w27_wr_n   <= bus_wr_n;
        w27_rd_n   <= bus_rd_n;
        w27_addr   <= bus_addr;
        w27_din    <= cpu_dout;
    end
    wifi uwifi (
        .clk_i      (clk_27m),
        .wait_o     (wait_uart),
        .reset_i    (bus_reset_n),
        .iorq_i     (w27_iorq_n),
        .wrt_i      (w27_wr_n),
        .rd_i       (w27_rd_n),
`ifdef WIFI_PMOD_TEST
        .rx_i       (uart_pmod_rx),          // TEST: RX por PMOD1 D22 (CH340 TX / PC-de-ESP)
`elsif ENABLE_WIFI_ESP32
        .rx_i       (esp_rx_i),              // _153c: J10 pin 16 (N17) <- ESP32-C6 IO16
`else
        .rx_i       (bl616_jtagsel),         // onboard: V14 <- BL616 IO28 TX
`endif
        .tx_o       (bl616_uart_tx_w),
        .adr_i      (w27_addr),
        .db_i       (w27_din),
        .db_o       (uart_dout),
        .dbg_overflow_o (wifi_ovf_p),
        .dbg_underrun_o (wifi_unr_p)
    );

    // ===== V3.1: CAZA DE LAS DESCARGAS CORRUPTAS =====
    // Los DOS unicos mecanismos de perdida, contados por separado porque cada
    // uno apunta a un culpable distinto:
    //   OVERFLOW = el ESP escribio con la FIFO llena -> byte TIRADO. Hasta
    //              ahora esto era INVISIBLE (fifo.vhd tiraba el byte sin
    //              dejar rastro). Si sube: falta control de flujo en el
    //              enlace, y migrar al S3 SE LO LLEVA PUESTO.
    //   UNDERRUN = el Z80 leyo y no habia datos. Si sube y el fichero sale
    //              con bloques a CERO pero alineado -- que es la firma
    //              observada (Fleet cada 25 sectores, Aleste cada 49) --
    //              entonces el driver UNAPI esta entregando ceros sin avisar,
    //              y el bug es del lado MSX.
    // Si NO sube ninguno, los dos mecanismos quedan descartados de golpe.
    wire wifi_ovf_p, wifi_unr_p;
    reg [15:0] wifi_ovf_cnt = 16'd0;
    reg [15:0] wifi_unr_cnt = 16'd0;
    reg        wifi_ovf_d = 1'b0, wifi_unr_d = 1'b0;
    always @(posedge clk_27m) begin
        wifi_ovf_d <= wifi_ovf_p;
        wifi_unr_d <= wifi_unr_p;
        if (wifi_ovf_p && !wifi_ovf_d) wifi_ovf_cnt <= wifi_ovf_cnt + 16'd1;
        if (wifi_unr_p && !wifi_unr_d) wifi_unr_cnt <= wifi_unr_cnt + 16'd1;
    end

`endif 

    //rtc
    wire rtc_req_r;
    wire rtc_req_w;
    wire [7:0] rtc_dout;
    assign rtc_req_w = (bus_addr[7:1] == 7'b1011010 && bus_iorq_n == 0 && bus_m1_n == 1 && bus_wr_n == 0)? 1 : 0; // I/O:B4-B5h   / RTC
    assign rtc_req_r = (bus_addr[7:1] == 7'b1011010 && bus_iorq_n == 0 && bus_m1_n == 1 && bus_rd_n == 0)? 1 : 0; // I/O:B4-B5h   / RTC

    rtc rtc1(
        .clk21m(clk_27m),
        .reset(0),
        .clkena(clk_enable_3m6_27),
        .req(rtc_req_w | rtc_req_r),
        .ack(),
        .wrt(rtc_req_w),
        .adr(bus_addr),
        .dbi(rtc_dout),
        .dbo(cpu_dout)
    );

    //vdp
	wire vdp_csw_n; //VDP write request
	wire vdp_csr_n; //VDP read request	
    wire [7:0] vdp_dout;
    wire vdp_int;
    wire WeVdp_n;
    wire [16:0] VdpAdr;
    wire [15:0] VrmDbi;
    wire [7:0] VrmDbo;
    wire VideoDHClk;
    wire VideoDLClk;
    //decode del VDP: 98-9Bh
    wire vdp_io_hit;
`ifdef ENABLE_V9968_VDP
    // _140 ESPEJO 88-8Bh: la demo ru66-v9968-demo y el software de cartucho
    // V9968 EXTERNO hablan SOLO por 88-8Bh (nunca 98-9B). En HW real son dos
    // chips (V9968 externo en 88-8B + VDP interno en 98-9B, "switch to the
    // V9968 display"); en el MSXimus el V9968 YA ES el VDP interno, asi que
    // aliasamos AMBOS rangos al mismo chip. Se ignora bus_addr[4]: 98-9B
    // (bit4=1) y 88-8B (bit4=0) son las UNICAS combinaciones con [7:5]=100 y
    // [3:2]=10 (0x88-8B libre en el MSXimus; vecinos PSG A0-A2/PPI A8-AA/
    // Y8950 C0-C1). mode = bus_addr[1:0] es identico en ambos rangos, asi
    // que el glue recibe el mismo puerto; BIOS/DOS siguen en 98-9B intactos.
    // 15/09 (gen C de HRA, ceeecd7): + puerto #4 = 9Ch (y su espejo 8Ch): flags de
    // interrupcion y el bit 7 que desbloquea R#20/R#21. 9Dh-9Fh/8Dh-8Fh siguen fuera.
    assign vdp_io_hit = ( bus_addr[7:5] == 3'b100 && (bus_addr[3:2] == 2'b10 || bus_addr[3:0] == 4'b1100) );
`else
    assign vdp_io_hit = ( bus_addr[7:2] == 6'b100110 );
`endif
    assign vdp_csw_n = (vdp_io_hit == 1 && bus_iorq_n == 0 && bus_m1_n == 1 && bus_wr_n == 0)? 0:1; // VDP write
    assign vdp_csr_n = (vdp_io_hit == 1 && bus_iorq_n == 0 && bus_m1_n == 1 && bus_rd_n == 0)? 0:1; // VDP read

`ifndef ENABLE_V9968_VDP
    v9958_top vdp4 (
        .clk (clk_27m),
        .clk_135 (clk_135),           // legado (sin uso con VIDEO720)
        .clk_135_lock (clock_locked), // mismo PLL -> mismo lock (antes: lock del CLK_135 propio)
`ifdef VIDEO720
        .clk_hdmi  (clk_hdmi),        // v3.0: pixel 720p 74.25 (pll_74, cascada monitorcore)
        .clk_hdmi5 (clk_hdmi5),       // v3.0: TMDS x5 371.25
        .dbg_bridge(dbg_bridge_w),    // v3.1: diagnostico del puente -> PMOD0
`endif
        .dbg_video (dbg_video_w),     // sondas de video del bring-up
        .s1 (0),
        .clk_50 (0),
        .clk_125 (0),

    `ifdef ENABLE_V9958
        .reset_n (bus_reset_n ),
    `else
        .reset_n (0),
    `endif
        .mode    (bus_addr[1:0]),
        .csw_n   (vdp_csw_n),
        .csr_n   (vdp_csr_n),

        .int_n   (vdp_int),
        .gromclk (),
        .cpuclk  (),
        .cdi     (vdp_dout),
        .cdo     (cpu_dout),

        .audio_sample   (audio_sample),
        .audio_sample_r (audio_sample_r),
        .aspect_16_9    (config_enable_16_9),

        .adc_clk  (),
        .adc_cs   (),
        .adc_mosi (),
        .adc_miso (0),

    `ifdef ENABLE_CONFIG
        .maxspr_n    (~config_enable_8sprites),  // Sprite Limit 8/linea (menu, config2[6]); 1 = limite clasico 4
    `else
        .maxspr_n    (1),
    `endif
    `ifdef ENABLE_SCAN_LINES
        .scanlin_n   (~config_enable_scanlines),
    `else
        .scanlin_n   (1),
    `endif
        .gromclk_ena_n (1),
        .cpuclk_ena_n  (1),

        .WeVdp_n(WeVdp_n),
        .VdpAdr(VdpAdr),
        .VrmDbi(VrmDbi2),
        .VrmDbo(VrmDbo),

        .VideoDHClk(VideoDHClk),
        .VideoDLClk(VideoDLClk),

        .tmds_clk_p    (clk_p),
        .tmds_clk_n    (clk_n),
        .tmds_data_p   (data_p),
        .tmds_data_n   (data_n)
    );

`else  // ==================== ENABLE_V9968_VDP ====================
    // F1 V9968: el VDP de HRA! (fpga/v9968, parche tag+eco) sustituye al
    // v9958_top ENTERO. VRAM en la SDRAM compartida via shim (contrato 8
    // ciclos) + bridge CDC al puerto wv2 de memory.v. Video: puente 800px
    // msx2hdmi_v9968 (ring BRAM, back-end TMDS intacto). v1: NTSC (la
    // geometria 50Hz del V9968 esta sin medir; pal_mode=0).

    // ---- reloj maestro 85.909 MHz (27 x 35/11, 0 ppm vs 24x colorburst) ----
    wire clk_86, pll86_lock;
    pll_86 pll86_vdp ( .init_clk(ex_clk_27m), .clkout0(clk_86), .lock(pll86_lock), .clkin(clk27_video) );   // 138K: init_clk

    // _125b: syn_maxfan — rst86_n abanica a TODO el dominio clk_86 (shim +
    // core V9968) y su ultima etapa aparecio como migaja de -0.063 en el
    // roll P235 (rst86_sync[3] -> CEs de pfq). La replica de la herramienta
    // (identica por construccion) acorta las redes del arbol de reset.
    (* syn_maxfan = 16 *) reg [3:0] rst86_sync = 4'd0;
    always @(posedge clk_86) rst86_sync <= {rst86_sync[2:0], bus_reset_n & pll86_lock};
    wire rst86_n = rst86_sync[3];

    // ---- glue bus T80 -> valid/ready (una transaccion por ciclo I/O) ----
    wire [2:0] v68_bus_address;
    wire       v68_ioreq, v68_write, v68_valid, v68_ready;
    wire [7:0] v68_wdata, v68_rdata;
    wire       v68_rdata_en;
    v9968_cpu_glue u_v68glue (
        .clk_86(clk_86), .rst_n(rst86_n),
        .csw_n(vdp_csw_n), .csr_n(vdp_csr_n),
        .mode(bus_addr[2:0]), .cdo(cpu_dout), .cdi_r(vdp_dout),   // [2] = puerto #4 (9Ch)
        .wait_n(v68_wait86_n),   // _177: /WAIT del puerto CPU del V9968
        .bus_address(v68_bus_address), .bus_ioreq(v68_ioreq),
        .bus_write(v68_write), .bus_valid(v68_valid), .bus_ready(v68_ready),
        .bus_wdata(v68_wdata), .bus_rdata(v68_rdata), .bus_rdata_en(v68_rdata_en)
    );

    // ---- el V9968 ----
    wire [17:2] v68_vram_address;
    wire        v68_vram_write, v68_vram_valid, v68_vram_refresh;
    wire [31:0] v68_vram_wdata, v68_vram_rdata;
    wire [3:0]  v68_vram_mask;
    wire [4:0]  v68_vram_tag, v68_vram_rtag;
    wire        v68_vram_rdata_en;
    wire        v68_vram_stall;
    wire        v68_hs, v68_vs, v68_de;
    wire [7:0]  v68_r8, v68_g8, v68_b8;
    // 🏆 AQUI VIVIAN CINCO MULTIPLEXORES, y estaban EN clk_86 -- el reloj por
    // el que llevamos toda la sesion peleando picosegundos. Los ponia el
    // lanzador del S3 para robarle el bus del VDP al Z80. Retirado el lanzador,
    // el camino queda directo: los alias los pliega la sintesis y el
    // instanciado de abajo no se toca.
    wire [2:0] v68_addr_mx  = v68_bus_address;
    wire       v68_ioreq_mx = v68_ioreq;
    wire       v68_write_mx = v68_write;
    wire       v68_valid_mx = v68_valid;
    wire [7:0] v68_wdata_mx = v68_wdata;

    vdp u_v9968 (
        .reset_n(rst86_n), .clk(clk_86), .initial_busy(1'b0),
        .bus_address(v68_addr_mx), .bus_ioreq(v68_ioreq_mx), .bus_write(v68_write_mx),
        .bus_valid(v68_valid_mx), .bus_ready(v68_ready),
        .bus_wdata(v68_wdata_mx), .bus_rdata(v68_rdata), .bus_rdata_en(v68_rdata_en),
        .int_n(vdp_int),
        .vram_address(v68_vram_address), .vram_write(v68_vram_write),
        .vram_valid(v68_vram_valid), .vram_wdata(v68_vram_wdata),
        .vram_wdata_mask(v68_vram_mask),
        .vram_rdata(v68_vram_rdata), .vram_rdata_en(v68_vram_rdata_en),
        .vram_tag(v68_vram_tag), .vram_rtag(v68_vram_rtag),
        .vram_stall(v68_vram_stall),
        .vram_refresh(v68_vram_refresh),
        .display_hs(v68_hs), .display_vs(v68_vs), .display_en(v68_de),
        .display_r(v68_r8), .display_g(v68_g8), .display_b(v68_b8),
        .force_highspeed(1'b0), .button(2'b00),
        .pulse0(), .pulse1(), .pulse2(), .pulse3(),
        .pulse4(), .pulse5(), .pulse6(), .pulse7()
    );

    // ---- shim VRAM (contrato 8 ciclos) + bridges CDC 85.9<->108 ----
    // _120: DOS canales — las lecturas de palabra piden las dos mitades en
    // paralelo (bk por wv2, bk2 por wv3): los modos de 256B/linea (SC7/8/12)
    // consumen 1 palabra/730ns y un canal solo daba ~800ns.
    wire [31:0] v68dbg_miss, v68dbg_bka, v68dbg_bkb;   // _121diag → COM11
    wire [31:0] v68dbg_park;                           // _124: park del shim
    wire [31:0] v68dbg_drops;                          // _154: {s1_pfq, wq_full} — drops reales
    wire        v68bk_req, v68bk_we, v68bk_done_t;
    wire [21:0] v68bk_addr;
    // _148 FIX B: el shim escribe PALABRAS de 32b con mascara de bytes (1 op de
    // backend por palabra en vez de hasta 4). Ver v9968_vram_shim.v.
    wire [31:0] v68bk_wdata;
    wire [3:0]  v68bk_wmask;
    wire [15:0] v68bk_rword;
    wire        v68bk2_req, v68bk2_done_t;
    wire [21:0] v68bk2_addr;
    wire [15:0] v68bk2_rword;
    v9968_vram_shim #(.VRAM_BASE(22'h280000)) u_v68shim (
        .clk_vdp(clk_86), .rst_n(rst86_n),
        .vram_address(v68_vram_address), .vram_write(v68_vram_write),
        .vram_valid(v68_vram_valid), .vram_wdata(v68_vram_wdata),
        .vram_wdata_mask(v68_vram_mask), .vram_tag(v68_vram_tag),
        .vram_rdata(v68_vram_rdata), .vram_rdata_en(v68_vram_rdata_en),
        .vram_rtag(v68_vram_rtag),
        .bk_req(v68bk_req), .bk_we(v68bk_we), .bk_addr(v68bk_addr),
        .bk_wdata(v68bk_wdata), .bk_wmask(v68bk_wmask),
        .bk_rword(v68bk_rword), .bk_done_t(v68bk_done_t),
        .bk2_req(v68bk2_req), .bk2_addr(v68bk2_addr),
        .bk2_rword(v68bk2_rword), .bk2_done_t(v68bk2_done_t),
        .vram_stall(v68_vram_stall),
        .diag(),
        .dbg_miss(v68dbg_miss), .dbg_bka(v68dbg_bka), .dbg_bkb(v68dbg_bkb),
        .dbg_park(v68dbg_park),
        .dbg_drops(v68dbg_drops)
    );
`ifdef ENABLE_VRAM_DDR3
    // ==== EXPERIMENTO _128X: la VRAM del V9968 vive en la DDR3 del SOM ====
    // Los MISMOS bridges CDC, con el lado far a clk_x1 (74.25, lo genera la
    // IP DDR3) y hablando con v9968_ddr3_backend en vez de memory.v. Los
    // puertos wv2/wv3 de memory.v quedan inertes (reqs a 0, abajo). El shim
    // NO se toca. ADVERTENCIA saga _94-_103: la DDR3 de esta placa es
    // analogicamente marginal (loteria de calibracion) — telemetria
    // vddr_diag en cnt_c[23:16] del COM11.
    wire        vddr_clk_x1;
    wire        vddr_a_req, vddr_a_we, vddr_b_req;
    wire [21:0] vddr_a_addr, vddr_b_addr;
    wire [31:0] vddr_a_wdata;      // _148 FIX B: palabra de 32b + mascara
    wire [3:0]  vddr_a_wmask;
    wire [15:0] vddr_a_dout, vddr_b_dout;
    wire        vddr_a_done, vddr_b_done;
    wire        vddr_ready;
    wire [7:0]  vddr_diag;
    assign vddr_ready_por = vddr_ready;    // V3.6g: la secuencia de arranque espera a esto
    wire [31:0] vddr_ops;      // _129b: {lecturas[31:16], escrituras[15:0]}

    v9968_sdram_bridge u_v68bridge (
        .clk_vdp(clk_86), .rst_n(rst86_n),
        .bk_req(v68bk_req), .bk_we(v68bk_we), .bk_addr(v68bk_addr),
        .bk_wdata(v68bk_wdata), .bk_wmask(v68bk_wmask),
        .bk_rword(v68bk_rword), .bk_done_t(v68bk_done_t),
        .clk_108m(vddr_clk_x1),
        .wv2_req(vddr_a_req), .wv2_we(vddr_a_we), .wv2_addr(vddr_a_addr),
        .wv2_wdata(vddr_a_wdata), .wv2_wmask(vddr_a_wmask),
        .wv2_dout(vddr_a_dout), .wv2_done(vddr_a_done)
    );
    v9968_sdram_bridge u_v68bridge2 (
        .clk_vdp(clk_86), .rst_n(rst86_n),
        .bk_req(v68bk2_req), .bk_we(1'b0), .bk_addr(v68bk2_addr),
        .bk_wdata(32'd0), .bk_wmask(4'd0),
        .bk_rword(v68bk2_rword), .bk_done_t(v68bk2_done_t),
        .clk_108m(vddr_clk_x1),
        .wv2_req(vddr_b_req), .wv2_we(), .wv2_addr(vddr_b_addr),
        .wv2_wdata(), .wv2_wmask(), .wv2_dout(vddr_b_dout), .wv2_done(vddr_b_done)
    );

    v9968_ddr3_backend u_vddr3 (
        .a_req(vddr_a_req), .a_we(vddr_a_we), .a_addr(vddr_a_addr),
        .a_wdata(vddr_a_wdata), .a_wmask(vddr_a_wmask),
        .a_dout(vddr_a_dout), .a_done(vddr_a_done),
        .b_req(vddr_b_req), .b_addr(vddr_b_addr),
        .b_dout(vddr_b_dout), .b_done(vddr_b_done),
        .clk_x1_out(vddr_clk_x1), .clk_7425_out(clk_7425), .ready(vddr_ready), .diag(vddr_diag),
        .dbg_ops(vddr_ops),        // _129b: {lecturas, escrituras} servidas
        .dbg_att(vddr_att), .dbg_calib_10ms(vddr_calib10), .dbg_boot_100ms(vddr_boot100),   // V3.7b
        .recal_req(1'b0),
        .clk_27(clk27_video),      // misma topologia que wave_ddr3/_86
        // _130 FIDELIDAD nand2mario: clk/mdclk del controlador desde el PAD
        // de 50MHz, EXACTAMENTE como su ddr3_framebuffer (probado con imagen
        // en esta placa). (La _128Z probo clk_54m del PLL — tambien calibro;
        // la teoria pad-vs-PLL de alanswx no era LA variable: lo decisivo
        // era darle TIEMPO a la calibracion. Fidelidad total = pad.)
        .clk_g50(ex_clk_27m),
        .pll27_lock(pll27_lock),
        .ddr_addr(ddr_addr), .ddr_bank(ddr_bank), .ddr_cs(ddr_cs),
        .ddr_ras(ddr_ras), .ddr_cas(ddr_cas), .ddr_we(ddr_we),
        .ddr_ck(ddr_ck), .ddr_ck_n(ddr_ck_n), .ddr_cke(ddr_cke),
        .ddr_odt(ddr_odt), .ddr_reset_n(ddr_reset_n), .ddr_dm(ddr_dm),
        .ddr_dq(ddr_dq), .ddr_dqs(ddr_dqs), .ddr_dqs_n(ddr_dqs_n)
    );
`else
    assign vddr_ready_por = 1'b1;          // V3.6g: sin DDR3 no hay que esperar a nadie
    assign vddr_att = 7'd0; assign vddr_calib10 = 8'd0; assign vddr_boot100 = 8'd0;
    // _148 FIX B — CAMINO LEGACY (VRAM en la SDRAM compartida, respaldo _137).
    // memory.v solo sabe escribir 1 BYTE por operacion en wv2/wv3 (SdrDat =
    // {wdata,wdata} con la DQM sacada de addr[0]) y NO se toca. El bridge se
    // instancia con NARROW_BYTE=1: acepta la palabra de 32b del shim y la
    // SERIALIZA en hasta 4 round-trips hacia memory.v, devolviendo bk_done_t
    // solo al terminar la palabra entera. Coste identico al esquema byte-a-byte
    // que este camino ya tenia; el shim ve una escritura atomica.
    // FAR_DW=8 mantiene el bus de datos far del ancho de memory.v (sin
    // conexiones de anchura desigual, que Gowin resuelve mal).
    v9968_sdram_bridge #(.NARROW_BYTE(1), .FAR_DW(8)) u_v68bridge (
        .clk_vdp(clk_86), .rst_n(rst86_n),
        .bk_req(v68bk_req), .bk_we(v68bk_we), .bk_addr(v68bk_addr),
        .bk_wdata(v68bk_wdata), .bk_wmask(v68bk_wmask),
        .bk_rword(v68bk_rword), .bk_done_t(v68bk_done_t),
        .clk_108m(clk_108m),
        .wv2_req(wv2_req), .wv2_we(wv2_we), .wv2_addr(wv2_addr),
        .wv2_wdata(wv2_wdata), .wv2_wmask(),
        .wv2_dout(wv2_dout), .wv2_done(wv2_done)
    );
    v9968_sdram_bridge #(.NARROW_BYTE(1), .FAR_DW(8)) u_v68bridge2 (
        .clk_vdp(clk_86), .rst_n(rst86_n),
        .bk_req(v68bk2_req), .bk_we(1'b0), .bk_addr(v68bk2_addr),
        .bk_wdata(32'd0), .bk_wmask(4'd0),
        .bk_rword(v68bk2_rword), .bk_done_t(v68bk2_done_t),
        .clk_108m(clk_108m),
        .wv2_req(wv3_req), .wv2_we(wv3_we), .wv2_addr(wv3_addr),
        .wv2_wdata(wv3_wdata), .wv2_wmask(),
        .wv2_dout(wv3_dout), .wv2_done(wv3_done)
    );
`endif

    // ---- puente de video 800px -> HDMI 720p (back-end TMDS intacto) ----
    // _127H: telemetria del audio — eventos de reset del HDMI y toggles del
    // lock del puente (pulsos estirados ~30ms; 2FF + flanco a clk_54m). El
    // lock togglea a ~30Hz en regimen: su TASA en el lector delata perdidas.
    // Si los cortes de ~3s del audio coinciden con saltos de rst_cnt, el
    // culpable es el re-arranque del stream HDMI (el receptor silencia).
    wire v68_dbg_lock, v68_dbg_rst;
    wire [31:0] v68_dbg_apkt;        // _127I: contadores del packet_picker
    wire [5:0]  v68_dbg_defer;       // _134: yanks del reset diferidos
    wire [4:0]  v68_dbg_tear;        // _134: assert en silicio (esperado 0)
    reg [2:0]  aud_rst_sy = 3'd0, aud_lock_sy = 3'd0;
    reg [15:0] aud_rst_cnt = 16'd0, aud_lock_cnt = 16'd0;
    always @(posedge clk_54m) begin
        aud_rst_sy  <= {aud_rst_sy[1:0],  v68_dbg_rst};
        aud_lock_sy <= {aud_lock_sy[1:0], v68_dbg_lock};
        if (aud_rst_sy[1]  & ~aud_rst_sy[2])  aud_rst_cnt  <= aud_rst_cnt  + 16'd1;
        if (aud_lock_sy[1] & ~aud_lock_sy[2]) aud_lock_cnt <= aud_lock_cnt + 16'd1;
    end
    // ce de pixel: el V9968 emite 1 pixel cada 2 ciclos de 85.9; un toggle
    // libre muestrea cada pixel exactamente una vez (la fase da igual: el
    // dato es estable 2 ciclos y la captura se auto-alinea con HS).
    reg ce86 = 1'b0;
    always @(posedge clk_86) ce86 <= ~ce86;

    wire [15:0] amp_hdmi;   // _133: vumetro del lado HDMI (ver dbg_uart)

    // ========================================================================
    // V3.1 PELDANO 1 -- iosys de TangCore (nand2mario), enlace UART con el BL616
    // ------------------------------------------------------------------------
    // Que se esta probando aqui, y por que asi:
    //
    //  * EL ENLACE NO NECESITA CABLE. bl616_jtagsel es el pad V14, que top.v ya
    //    documenta como "GPIO28 TX del BL616": exactamente el UART_RXD de la
    //    console.cst de nestang. Y U15 (GPIO27 RX del MCU) quedo libre al mudar
    //    el companion SPI al J10. Son los DOS MISMOS pines que usa TangCore.
    //
    //  * TODAVIA NO HAY FIRMWARE EN EL BL616, asi que nadie va a hablar por esa
    //    UART. Para que el bitstream diga ALGO, la BSRAM del overlay se genera
    //    con texto ya escrito en el buffer de caracteres (tools/gen_iosys_bram.py):
    //    al encender, textdisp lo pinta sin que intervenga nadie.
    //
    //  * Y COMO overlay_reg NACE A 1 en iosys_bl616, sin MCU que lo apague el
    //    overlay taparia la pantalla PARA SIEMPRE. De ahi el temporizador: unos
    //    segundos de overlay y se aparta. Asi un solo .fs contesta dos preguntas
    //    -- si la cadena BSRAM->textdisp->mux->HDMI pinta, y si el MSX sigue
    //    arrancando igual con el iosys dentro. El temporizador se va el dia que
    //    el MCU mande el comando 8.
    // ========================================================================
    wire        iosys_overlay;
    wire [7:0]  iosys_ovl_x, iosys_ovl_y;
    wire [14:0] iosys_ovl_color;

// 16/09: MANDOS HID POR LOS USB-A DEL FABRIC. usb_hid_host saca `game_snes` en
// el MISMO formato SNES de 12 bits que la palabra del BL616 (bit 4 arriba, 5
// abajo, 6 izquierda, 7 derecha, 8 A, 0 B, 9 X, 1 Y, 10/11 hombros), asi que se
// OR-ea con el mando 1 del MCU: cualquier mando en un USB-A cae en el puerto 1
// del MSX. Hasta hoy los USB-A solo servian teclado y raton ("gamepads USB-A =
// pieza futura") y el unico camino para un mando era el USB-C del BL616 con un
// hub con alimentacion; Albert lo descubrio el 16/09 con el panel de F12
// diciendo "USB: nada" y el mando enchufado en el USB-A. Limite: usb_hid_host
// es HID puro y solo entiende el informe de los mandos "SNES USB" (ejes
// 00/7F/FF en los bytes 3-4, botones en 5-6); un mando XInput (Xbox y los
// dongles que lo imitan, como el del Lenovo C01) sigue necesitando el BL616.
// Se asigna en el bloque ENABLE_USB_KBD, ya sincronizado a clk_54m.
wire [11:0] usb_joy_snes;
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
