Papipapito/MSXimus_138/fpga/v9968/vdp_cpu_interface.v

//
//	vdp_cpu_interface.v
//	CPU Interface for VDP
//
//	Copyright (C) 2025 Takayuki Hara
//
//	本ソフトウェアおよび本ソフトウェアに基づいて作成された派生物は、以下の条件を
//	満たす場合に限り、再頒布および使用が許可されます。
//
//	1.ソースコード形式で再頒布する場合、上記の著作権表示、本条件一覧、および下記
//	  免責条項をそのままの形で保持すること。
//	2.バイナリ形式で再頒布する場合、頒布物に付属のドキュメント等の資料に、上記の
//	  著作権表示、本条件一覧、および下記免責条項を含めること。
//	3.書面による事前の許可なしに、本ソフトウェアを販売、および商業的な製品や活動
//	  に使用しないこと。
//
//	本ソフトウェアは、著作権者によって「現状のまま」提供されています。著作権者は、
//	特定目的への適合性の保証、商品性の保証、またそれに限定されない、いかなる明示
//	的もしくは暗黙な保証責任も負いません。著作権者は、事由のいかんを問わず、損害
//	発生の原因いかんを問わず、かつ責任の根拠が契約であるか厳格責任であるか（過失
//	その他の）不法行為であるかを問わず、仮にそのような損害が発生する可能性を知ら
//	されていたとしても、本ソフトウェアの使用によって発生した（代替品または代用サ
//	ービスの調達、使用の喪失、データの喪失、利益の喪失、業務の中断も含め、またそ
//	れに限定されない）直接損害、間接損害、偶発的な損害、特別損害、懲罰的損害、ま
//	たは結果損害について、一切責任を負わないものとします。
//
//	Note that above Japanese version license is the formal document.
//	The following translation is only for reference.
//
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
//	1. Redistributions of source code must retain the above copyright
//	   notice, this list of conditions and the following disclaimer.
//	2. Redistributions in binary form must reproduce the above
//	   copyright notice, this list of conditions and the following
//	   disclaimer in the documentation and/or other materials
//	   provided with the distribution.
//	3. Redistributions may not be sold, nor may they be used in a
//	   commercial product or activity without specific prior written
//	   permission.
//
//	THIS SOFTWARE IS PROVIDED BY THE COPYRIGHT HOLDERS AND CONTRIBUTORS
//	"AS IS" AND ANY EXPRESS OR IMPLIED WARRANTIES, INCLUDING, BUT NOT
//	LIMITED TO, THE IMPLIED WARRANTIES OF MERCHANTABILITY AND FITNESS
//	FOR A PARTICULAR PURPOSE ARE DISCLAIMED. IN NO EVENT SHALL THE
//	COPYRIGHT OWNER OR CONTRIBUTORS BE LIABLE FOR ANY DIRECT, INDIRECT,
//	INCIDENTAL, SPECIAL, EXEMPLARY, OR CONSEQUENTIAL DAMAGES (INCLUDING,
//	BUT NOT LIMITED TO, PROCUREMENT OF SUBSTITUTE GOODS OR SERVICES;
//	LOSS OF USE, DATA, OR PROFITS; OR BUSINESS INTERRUPTION) HOWEVER
//	CAUSED AND ON ANY THEORY OF LIABILITY, WHETHER IN CONTRACT, STRICT
//	LIABILITY, OR TORT (INCLUDING NEGLIGENCE OR OTHERWISE) ARISING IN
//	ANY WAY OUT OF THE USE OF THIS SOFTWARE, EVEN IF ADVISED OF THE
//	POSSIBILITY OF SUCH DAMAGE.
//
//-----------------------------------------------------------------------------

module vdp_cpu_interface (
	input				reset_n,
	input				clk,					//	42.95454MHz

	input	[2:0]		bus_address,
	input				bus_ioreq,
	input				bus_write,
	input				bus_valid,
	output				bus_ready,
	input	[7:0]		bus_wdata,
	output	[7:0]		bus_rdata,
	output				bus_rdata_en,

	output	[17:0]		vram_address,
	output				vram_write,
	output				vram_valid,
	input				vram_ready,
	output	[7:0]		vram_wdata,
	input	[7:0]		vram_rdata,
	input				vram_rdata_en,

	output				palette_valid,
	output		[7:0]	palette_num,
	output		[4:0]	palette_r,
	output		[4:0]	palette_g,
	output		[4:0]	palette_b,

	output				int_n,
	input				intr_line,					//	pulse
	input				intr_frame,					//	pulse
	input				intr_command_end,			//	pulse
	input				clear_line_interrupt,		//	pulse

	output				clear_sprite_collision,		//	pulse
	input				sprite_collision,
	output				clear_sprite_collision_xy,	//	pulse
	input		[8:0]	sprite_collision_x,
	input		[9:0]	sprite_collision_y,
	input				sprite_overmap,
	input		[4:0]	sprite_overmap_id,
	output				clear_border_detect,		//	pulse
	output				read_color,					//	pulse

	output				register_write,
	output		[5:0]	register_num,
	output		[7:0]	register_data,

	input				status_command_execute,		//	S#2 bit0
	input				status_field,				//	S#2 bit1
	input				status_border_detect,		//	S#2 bit4
	input				status_hsync,				//	S#2 bit5
	input				status_vsync,				//	S#2 bit6
	input				status_transfer_ready,		//	S#2 bit7
	input		[7:0]	status_color,				//	S#7
	input		[8:0]	status_border_position,		//	S#8, S#9
	input				vram_access_mask,			//	MXC
	input				force_highspeed,

	output	[4:0]		reg_screen_mode,
	output				reg_sprite_magify,
	output				reg_sprite_16x16,
	output				reg_display_on,
	output	[17:10]		reg_pattern_name_table_base,
	output	[17:6]		reg_color_table_base,
	output	[17:11]		reg_pattern_generator_table_base,
	output	[17:7]		reg_sprite_attribute_table_base,
	output	[17:11]		reg_sprite_pattern_generator_table_base,
	output	[7:0]		reg_backdrop_color,
	output				reg_sprite_disable,
	output				reg_color0_opaque,
	output				reg_50hz_mode,
	output				reg_interleaving_mode,
	output				reg_interlace_mode,
	output				reg_212lines_mode,
	output	[7:0]		reg_text_back_color,
	output	[7:0]		reg_blink_period,
	output	[7:0]		reg_display_adjust,
	output	[7:0]		reg_interrupt_line,
	output	[7:0]		reg_vertical_offset,
	output				reg_scroll_planes,
	output				reg_left_mask,
	output				reg_yjk_mode,
	output				reg_yae_mode,
	output				reg_command_enable,
	output				reg_sprite_priority_shuffle,
	output	[2:0]		reg_horizontal_offset_l,
	output	[8:3]		reg_horizontal_offset_h,
	output				reg_command_high_speed_mode,
	output				reg_sprite_nonR23_mode,
	output				reg_interrupt_line_nonR23_mode,
	output				reg_sprite_mode3,
	output				reg_ext_palette_mode,
	output				reg_ext_command_mode,
	output				reg_vram256k_mode,
	output				reg_sprite16_mode,
	output				reg_flat_interlace_mode,

	input	[1:0]		button,
	output				pulse0,
	output				pulse1,
	output				pulse2,
	output				pulse3,
	output				pulse4,
	output				pulse5,
	output				pulse6,
	output				pulse7
);
	localparam	[4:0]	c_v9958id			= 5'b00010;
	localparam	[4:0]	c_v9968id			= 5'b00011;
	reg					ff_bus_ioreq;
	reg					ff_bus_write;
	reg					ff_bus_valid;
	reg					ff_bus_ready;
	reg		[7:0]		ff_bus_wdata;
	reg		[7:0]		ff_status_register;

	reg					ff_port0;
	reg					ff_port1;
	reg					ff_port2;
	reg					ff_port3;
	reg					ff_port4;
	wire				w_write;
	wire				w_read;
	reg		[7:0]		ff_bus_rdata;
	reg					ff_bus_rdata_en;
	reg		[4:0]		ff_screen_mode;
	reg					ff_line_interrupt_enable = 1'b0;
	reg					ff_frame_interrupt_enable = 1'b0;
	reg					ff_command_end_interrupt_enable = 1'b0;
	reg					ff_sprite_magify;
	reg					ff_sprite_16x16;
	reg					ff_display_on;
	reg		[17:10]		ff_pattern_name_table_base;
	reg		[17:6]		ff_color_table_base;
	reg		[17:11]		ff_pattern_generator_table_base;
	reg		[17:7]		ff_sprite_attribute_table_base;
	reg		[17:11]		ff_sprite_pattern_generator_table_base;
	reg		[7:0]		ff_backdrop_color;
	reg					ff_sprite_disable;
	reg					ff_vram_type;
	reg					ff_color0_opaque;
	reg					ff_50hz_mode;
	reg					ff_interleaving_mode;
	reg					ff_interlace_mode;
	reg					ff_212lines_mode;
	reg		[7:0]		ff_text_back_color;
	reg		[7:0]		ff_blink_period;
	reg		[3:0]		ff_status_register_pointer;
	reg		[7:0]		ff_color_palette_address;
	reg		[1:0]		ff_color_palette_phase;
	reg					ff_color_palette_valid;
	reg		[4:0]		ff_palette_r;
	reg		[4:0]		ff_palette_g;
	reg		[4:0]		ff_palette_b;
	reg		[5:0]		ff_register_pointer;
	reg					ff_not_increment;
	reg		[7:0]		ff_display_adjust;
	reg		[7:0]		ff_interrupt_line;
	reg		[7:0]		ff_vertical_offset;
	reg					ff_scroll_planes;
	reg					ff_left_mask;
	reg					ff_yjk_mode;
	reg					ff_yae_mode;
	reg					ff_command_enable;
	reg					ff_sprite_priority_shuffle;
	reg		[2:0]		ff_horizontal_offset_l;
	reg		[8:3]		ff_horizontal_offset_h;
	reg					ff_command_high_speed_mode;
	reg					ff_sprite_nonR23_mode;
	reg					ff_interrupt_line_nonR23_mode;
	reg					ff_sprite_mode3;
	reg					ff_ext_palette_mode;
	reg					ff_sprite16_mode;
	reg					ff_flat_interlace_mode;
	reg					ff_force_highspeed;
	//	MSXimus _163 (port de 0683e7e): ff_ext_command_mode / ff_vram256k_mode /
	//	ff_fakeID se fusionan en ESTE bit. V58=1 => se comporta como un V9958
	//	(ID de V9958 en S#1, sin comandos extendidos, sin 256K).
	reg					ff_v9958_mode;

	reg					ff_2nd_access;
	reg		[7:0]		ff_1st_byte;
	reg					ff_register_write;
	reg					ff_port3_write;
	reg		[5:0]		ff_register_num;
	reg		[17:0]		ff_vram_address;
	reg					ff_vram_address_noinc;
	wire	[17:0]		w_next_vram_address;
	reg					ff_vram_address_write;		//	アドレス設定が書き込み用に設定されたかどうか
	reg					ff_vram_write;				//	実際のアクセスが書き込みアクセスかどうか
	reg		[7:0]		ff_vram_wdata;
	reg					ff_vram_address_inc;		//	アドレスインクリメント要求
	reg					ff_vram_valid;
	reg					ff_busy;

	//	MSXimus _149: BUFFER DE PRE-LECTURA DE VRAM (comportamiento del V9938 real)
	reg					ff_pf_req;					//	hay que lanzar una pre-lectura
	reg					ff_pf_inflight;				//	la lectura en vuelo es una PRE-lectura
	reg					ff_pf_valid;				//	el buffer tiene un byte listo
	reg		[7:0]		ff_pf_data;
	wire				w_set_vram_address;
	wire				w_set_read_address;
	wire				w_pf_invalidate;
	wire				w_pf_hit;
	//	MSXimus _162: handshake del bus — LA transferencia (la ve el maestro Y la
	//	latchea este modulo en el MISMO ciclo). Ver el comentario del latch.
	wire				w_bus_accept;

	reg					ff_line_interrupt = 1'b0;
	reg					ff_frame_interrupt = 1'b0;
	reg					ff_command_end_interrupt = 1'b0;
	wire				w_line_interrupt;
	wire				w_frame_interrupt;
	wire				w_command_end_interrupt;

	reg		[1:0]		ff_button1 = 2'd0;
	reg		[1:0]		ff_button2 = 2'd0;
	reg					ff_force_page2 = 1'b0;
	//	Upstream gen C (hra1129 ceeecd7, 04/08/2026): R#20 y R#21 quedan BLOQUEADOS tras el
	//	reset y solo se escriben si el software ha puesto a 0 el bit 7 del puerto #4 (9Ch).
	//	Motivo (cazado en la Zynq el 15/09 con el marcador de Xevious): la BIOS MSX2 escribe
	//	R#20..R#23 = 0 por 9Bh en cada init del VDP, y R#21[0]=0 encendia el modo nativo (ID 3,
	//	A17 vivo en las bases de tabla) sin que nadie lo pidiera.
	reg					ff_lock_extregs = 1'b1;

	always @( posedge clk ) begin
		ff_button1 <= button;
		ff_button2 <= ff_button1;
	end

	always @( posedge clk ) begin
		if( ff_button1[0] && !ff_button2[0] ) begin
			ff_force_page2 <= !ff_force_page2;
		end
	end

	assign pulse0		= 1'b0;										// red
	assign pulse1		= ff_vram_valid;							// green
	assign pulse2		= ff_vram_address_inc;						// blue
	assign pulse3		= (bus_valid && bus_address == 3'b000);		// yellow
	assign pulse4		= (bus_valid && bus_address == 3'b001);		// cyan
	assign pulse5		= (bus_valid && bus_address == 3'b010);		// purple
	assign pulse6		= (bus_valid && bus_address == 3'b011);		// pink
	assign pulse7		= 1'b0;

	// --------------------------------------------------------------------
	//	Latch
	// --------------------------------------------------------------------
	always @( posedge clk ) begin
		if( !reset_n ) begin
			ff_bus_ioreq	<= 1'b0;
			ff_bus_write	<= 1'b0;
			ff_bus_wdata	<= 1'b0;
			ff_port0		<= 1'b0;
			ff_port1		<= 1'b0;
			ff_port2		<= 1'b0;
			ff_port3		<= 1'b0;
			ff_port4		<= 1'b0;
			ff_bus_valid	<= 1'b0;
			ff_bus_ready	<= 1'b1;
		end
		//	MSXimus _162 (bug #1 del INFORME_NIQUELADO 26/07): el latch aceptaba
		//	con ff_bus_ready CRUDO, pero el maestro (fpga/src/v9968_cpu_glue.v)
		//	espera el bus_ready GATEADO de abajo. PORQUE del fallo: una
		//	transaccion que llegue DENTRO de una ventana busy / pre-lectura se
		//	latcheaba sin que el maestro viera la transferencia; el glue mantiene
		//	bus_valid, ff_bus_ready vuelve a 1 al ciclo siguiente y la MISMA
		//	transaccion se latchea OTRA VEZ => se ejecuta DOS VECES (dos avances
		//	del contador de direccion en un IN del puerto 0 — el "salto +1" —,
		//	dos toggles de ff_2nd_access en un OUT al puerto 1, doble escritura
		//	en VRAM...). Se acepta EXACTAMENTE en el ciclo en que el maestro da
		//	la transferencia por hecha: misma condicion que bus_ready.
		else if( w_bus_accept ) begin
			ff_bus_ioreq	<= bus_ioreq;
			ff_bus_write	<= bus_write;
			ff_bus_wdata	<= bus_wdata;
			ff_port0		<= (!bus_address[2] && !bus_address[1] && !bus_address[0]);
			ff_port1		<= (!bus_address[2] && !bus_address[1] &&  bus_address[0]);
			ff_port2		<= (!bus_address[2] &&  bus_address[1] && !bus_address[0]);
			ff_port3		<= (!bus_address[2] &&  bus_address[1] &&  bus_address[0]);
			ff_port4		<= ( bus_address[2] && !bus_address[1] && !bus_address[0]);
			ff_bus_valid	<= 1'b1;
			ff_bus_ready	<= 1'b0;
		end
		else begin
			ff_bus_valid	<= 1'b0;
			ff_bus_ready	<= bus_ioreq;
		end
	end

	//	MSXimus _149: mientras una PRE-lectura esta EN VUELO el puerto de VRAM
	//	esta ocupado — se retiene al maestro igual que con ff_busy (el maestro
	//	reintenta solo: ff_bus_ready vuelve a 1 con bus_ioreq). Sin esto, un
	//	acceso al puerto 0 durante la pre-lectura lanzaria un SEGUNDO
	//	ff_vram_valid y las dos respuestas se confundirian.
	assign bus_ready	= ff_bus_ready & ~ff_busy & ~ff_pf_inflight;
	//	MSXimus _162: la MISMA condicion, mas bus_valid — es el unico ciclo en el
	//	que la transferencia existe para los dos lados del handshake.
	assign w_bus_accept	= bus_valid & bus_ready;

	assign w_write		= ff_bus_valid &  ff_bus_write & ~ff_busy & ~ff_pf_inflight;
	assign w_read		= ff_bus_valid & ~ff_bus_write & ~ff_busy & ~ff_pf_inflight;

	//	MSXimus _149: pulsos de 1 ciclo del ajuste de direccion de VRAM
	//	(2o acceso al puerto 1 con bit7=0; bit6 = 0 lectura / 1 escritura)
	assign w_set_vram_address	= w_write & ff_port1 & ff_2nd_access & ~ff_bus_wdata[7];
	assign w_set_read_address	= w_set_vram_address & ~ff_bus_wdata[6];
	//	el buffer deja de ser valido si se re-apunta la direccion para ESCRIBIR,
	//	si se cambia el banco (R#14) o si la CPU ESCRIBE en VRAM (el contador
	//	avanza y el byte guardado ya no corresponde a la direccion actual)
	assign w_pf_invalidate		= w_set_vram_address |
								  (ff_register_write & (ff_register_num == 6'd14)) |
								  (w_write & ff_port0);
	assign w_pf_hit				= w_read & ff_port0 & ff_pf_valid;

	// --------------------------------------------------------------------
	//	VRAM Read/Write access
	// --------------------------------------------------------------------
	always @( posedge clk ) begin
		if( !reset_n ) begin
			ff_2nd_access			<= 1'b0;
			ff_1st_byte				<= 8'd0;
			ff_vram_address_write	<= 1'b0;
			ff_register_write		<= 1'b0;
			ff_port3_write			<= 1'b0;
			ff_register_num			<= 6'd0;
		end
		else if( w_read || (w_write && ff_port0) ) begin
			//	_185 (caza Fleet/DQ2 05/08, intuicion de Albert "funciones del
			//	TMS9918 no heredadas"): en el TMS9918 y en el V9938 (appmanual)
			//	LEER el registro de status RESETEA el latch del par de bytes
			//	del puerto 1. El software MSX1/old-school depende de ello (leer
			//	status antes de poner direccion, por si una ISR dejo un par a
			//	medias). Sin esto, un par desincronizado NO se re-sincroniza
			//	JAMAS: los selects de R#15 no aterrizan (Fleet: la BIOS poleando
			//	el registro EQUIVOCADO = un S#2 "fosil" eterno; reproducido
			//	determinista en tb_s2fossil FASE4: 8/8 mal sin esto, 1/8 con
			//	esto) y las puestas de direccion de VRAM se corren. Identico
			//	agujero en el upstream.
			ff_2nd_access	<= 1'b0;
			//	30/09/2026 (upstream HRA 05f9806): en el V9938/V9958 (y en openMSX, VDP.cc: registerDataStored) el par a
			//	medias se cancela con CUALQUIER lectura (98h-9Bh) y con una ESCRITURA al puerto 0, no solo con la lectura
			//	de status del _185. Fleet Commander II escribe un numero IMPAR de bytes en 99h (00,22,81,0F,86,00,88) y
			//	cuenta con que las escrituras a 98h del CLRSPR lo resincronicen; sin esto todos los registros siguientes
			//	quedaban corridos y acababa esperando un CE eterno. Banco: tools/v9968_sim/tb_port1_latch.sv (el de HRA).
			ff_register_write	<= 1'b0;
			ff_port3_write		<= 1'b0;
		end
		else if( ff_busy ) begin
			//	hold
		end
		else if( w_write && ff_port1 ) begin
			ff_2nd_access	<= ~ff_2nd_access;
			if( !ff_2nd_access ) begin
				//	1st write access
				ff_1st_byte		<= ff_bus_wdata;
			end
			else begin
				//	2nd write access
				ff_register_num	<= ff_bus_wdata[5:0];
				if( !ff_bus_wdata[7] ) begin
					//	Set VRAM Address
					ff_register_write		<= 1'b0;
					ff_port3_write			<= 1'b0;
					ff_vram_address_write	<= ff_bus_wdata[6];
				end
				else begin
					ff_register_write		<= 1'b1;
					ff_port3_write			<= 1'b0;
				end
			end
		end
		else if( w_write && ff_port3 ) begin
			ff_register_write	<= 1'b1;
			ff_port3_write		<= 1'b1;
			ff_register_num		<= ff_register_pointer;
			ff_1st_byte			<= ff_bus_wdata;
		end
		else if( w_write && ff_port2 && !ff_ext_palette_mode && ff_color_palette_phase == 2'd0 ) begin
			//	30/09/2026 (upstream HRA 05f9806): el 1er byte de la paleta V9938 (R/B) comparte el latch de datos con
			//	los puertos 1 y 3 (openMSX: dataLatch); el 2o byte saca de ahi R y B. La paleta extendida (3 bytes) no.
			ff_1st_byte			<= ff_bus_wdata;
			ff_register_write	<= 1'b0;
			ff_port3_write		<= 1'b0;
		end
		else begin
			ff_register_write	<= 1'b0;
			ff_port3_write		<= 1'b0;
		end
	end

	always @( posedge clk ) begin
		if( !reset_n ) begin
			ff_register_pointer	<= 5'd0;
			ff_not_increment	<= 1'b0;
		end
		else if( w_write && ff_port3 ) begin
			if( !ff_not_increment ) begin
				ff_register_pointer <= ff_register_pointer + 5'd1;
			end
		end
		else if( ff_register_write ) begin
			if( ff_register_num == 8'd17 && !ff_port3_write ) begin
				//	R#17 = [AII][N/A][R5][R4][R3][R2][R1][R0]
				ff_register_pointer	<= ff_1st_byte[5:0];
				ff_not_increment	<= ff_1st_byte[7];
			end
		end
	end

	// ------------------------------------------------------------------------
	//	write
	//		ff_address_inc=1 --> ff_vram_valid=1 --> ff_busy=0
	//	read
	//		ff_vram_valid=1 --> vram_rdata_en=1 --> ff_address_inc=1 --> ff_busy=0
	always @( posedge clk ) begin
		if( !reset_n ) begin
			ff_vram_valid		<= 1'b0;
			ff_vram_write		<= 1'b0;
			ff_vram_wdata		<= 8'd0;
			ff_vram_address_inc	<= 1'b0;
			ff_busy				<= 1'b0;
			ff_pf_req			<= 1'b0;
			ff_pf_inflight		<= 1'b0;
		end
		else begin
			if( vram_rdata_en ) begin
				ff_vram_address_inc	<= 1'b1;
				ff_pf_inflight		<= 1'b0;
			end
			else if( ff_vram_valid ) begin
				if( vram_ready ) begin
					ff_vram_valid		<= 1'b0;
					if( ff_vram_write ) begin
						ff_busy			<= 1'b0;
					end
				end
			end
			else if( ff_vram_address_inc ) begin
				ff_vram_address_inc	<= 1'b0;
				if( ff_vram_write && !vram_access_mask ) begin
					//	Write Access
					ff_vram_valid	<= 1'b1;
				end
				else begin
					//	Read access or vram_access_mask
					ff_busy			<= 1'b0;
				end
			end
			else if( w_write && ff_port0 ) begin
				//	VRAM write access
				ff_vram_valid		<= 1'b0;
				ff_vram_write		<= 1'b1;
				ff_vram_wdata		<= ff_bus_wdata;
				ff_vram_address_inc <= 1'b1;
				ff_busy				<= 1'b1;
				ff_pf_req			<= 1'b0;
			end
			else if( w_read && ff_port0 ) begin
				if( ff_pf_valid ) begin
					//	MSXimus _149: ACIERTO del buffer de pre-lectura — se
					//	responde en el MISMO ciclo (sin ff_busy, sin acceso a
					//	VRAM) y se arma la pre-lectura del byte siguiente. La
					//	direccion ya la adelanto la pre-lectura anterior.
					ff_pf_req			<= 1'b1;
				end
				else begin
					//	buffer vacio: lectura BLOQUEANTE como el upstream
					ff_vram_valid		<= 1'b1;
					ff_vram_write		<= 1'b0;
					ff_vram_wdata		<= 8'd0;
					ff_vram_address_inc <= 1'b0;
					ff_busy				<= 1'b1;
					ff_pf_req			<= 1'b1;	//	y encadena la siguiente
				end
			end
			//	MSXimus _162 (correccion del verificador): sin `!w_bus_accept` este
			//	parche cambiaba 115 dobles ejecuciones por 101 PERDIDAS silenciosas
			//	(mismo sintoma: par de bytes desincronizado). Medido a LAT=200 (la
			//	de placa ~190): con la linea, 230/230 aciertos, 0 perdidas, 0 dobles.
			else if( ff_pf_req && !ff_busy && !ff_pf_valid && !w_set_vram_address && !w_bus_accept ) begin
				//	(!w_set_vram_address: si en ESTE ciclo se esta re-apuntando la
				//	direccion, ff_vram_address todavia es la VIEJA — se espera un
				//	ciclo para pre-leer la nueva)
				//	MSXimus _149: lanzar la PRE-LECTURA. NO pone ff_busy: la CPU
				//	no espera por ella; solo ff_pf_inflight retiene el puerto.
				ff_vram_valid		<= 1'b1;
				ff_vram_write		<= 1'b0;
				ff_vram_wdata		<= 8'd0;
				ff_vram_address_inc <= 1'b0;
				ff_pf_inflight		<= 1'b1;
				ff_pf_req			<= 1'b0;
			end

			//	el ajuste de direccion de LECTURA arma la pre-lectura, y el de
			//	ESCRITURA / R#14 / una escritura en VRAM la cancela. Van al FINAL
			//	para ganar a las ramas de arriba si coinciden en el mismo ciclo.
			if( w_set_read_address ) begin
				ff_pf_req			<= 1'b1;
			end
			else if( w_pf_invalidate ) begin
				ff_pf_req			<= 1'b0;
			end
		end
	end

	assign w_next_vram_address	= ff_vram_address + 18'd1;

	always @( posedge clk ) begin
		if( !reset_n ) begin
			ff_vram_address			<= 18'd0;
			ff_vram_address_noinc	<= 1'b0;
		end
		else if( ff_vram_address_inc ) begin		//	1clock pulse
			if( ff_vram_address_noinc ) begin
				ff_vram_address_noinc	<= 1'b0;
			end
			//	MSXimus _125 (re-aplicado sobre th9958): VR=0 (R#8 bit3) NO
			//	bloquea el acarreo del contador al banco — en silicio real y
			//	openMSX VR solo elige el tipo de DRAM para el refresh. Con el
			//	gate, un stream de escritura >16KB (soft_vdp_test2 escribe
			//	R#8=0x02) envolvia en el banco 0: "media pantalla" en HW _124.
			//	El wrap de 14 bits queda SOLO para los modos TMS9918.
			else if( ff_screen_mode[4:3] == 2'b00 ) begin
				ff_vram_address[13:0]	<= w_next_vram_address[13:0];
			end
			else if( !ff_v9958_mode ) begin
				ff_vram_address			<= w_next_vram_address;
			end
			else begin
				ff_vram_address			<= { 1'b0, w_next_vram_address[16:0] };
			end
		end
		else if( ff_register_write && ff_register_num == 6'd14 ) begin
			//	R#14 = [N/A][N/A][N/A][N/A][A17][A16][A15][A14]
			//	MSXimus _125: VR=0 tampoco fuerza aqui el banco a 0
			//	(misma justificacion que arriba).
			if( !ff_v9958_mode ) begin
				ff_vram_address[17:14]	<= ff_1st_byte[3:0];
			end
			else begin
				ff_vram_address[17:14]	<= { 1'b0, ff_1st_byte[2:0] };
			end
		end
		else if( w_write && ff_port1 ) begin
			if( ff_2nd_access ) begin
				//	2nd write access
				case( ff_bus_wdata[7:6] )
				2'd0:			//	Set VRAM Read Address
					begin
						ff_vram_address[7:0]	<= ff_1st_byte;
						ff_vram_address[13:8]	<= ff_bus_wdata[5:0];
						ff_vram_address_noinc	<= 1'b0;
					end
				2'd1:			//	Set VRAM Write Address
					begin
						ff_vram_address[7:0]	<= ff_1st_byte;
						ff_vram_address[13:8]	<= ff_bus_wdata[5:0];
						ff_vram_address_noinc	<= 1'b1;
					end
				default:
					begin
						//	none
					end
				endcase
			end
		end
	end

	// --------------------------------------------------------------------
	//	Control registers
	// --------------------------------------------------------------------
	always @( posedge clk ) begin
		if( !reset_n ) begin
			ff_screen_mode <= 5'd0;
			ff_line_interrupt_enable <= 1'b0;
			ff_sprite_magify <= 1'b0;
			ff_sprite_16x16 <= 1'b0;
			ff_frame_interrupt_enable <= 1'b0;
			ff_display_on <= 1'b0;
			ff_pattern_name_table_base <= 8'd0;
			ff_color_table_base <= 12'd0;
			ff_pattern_generator_table_base <= 7'd0;
			ff_sprite_attribute_table_base <= 11'd0;
			ff_sprite_pattern_generator_table_base <= 7'd0;
			ff_backdrop_color <= 8'd0;
			ff_sprite_disable <= 1'b0;
			ff_vram_type <= 1'b1;
			ff_color0_opaque <= 1'b0;
			ff_50hz_mode <= 1'b0;
			ff_interleaving_mode <= 1'b0;
			ff_interlace_mode <= 1'b0;
			ff_212lines_mode <= 1'b0;
			ff_text_back_color <= 8'd0;
			ff_blink_period <= 8'd0;
			ff_status_register_pointer <= 4'd0;
			ff_display_adjust <= 8'd0;
			ff_interrupt_line <= 8'd0;
			ff_vertical_offset <= 8'd0;
			ff_scroll_planes <= 1'b0;
			ff_left_mask <= 1'b0;
			ff_yjk_mode <= 1'b0;
			ff_yae_mode <= 1'b0;
			ff_command_enable <= 1'b0;
			ff_sprite_priority_shuffle <= 1'b0;
			ff_horizontal_offset_l <= 3'd0;
			ff_horizontal_offset_h <= 6'd0;
			ff_command_high_speed_mode <= 1'b0;
			ff_sprite_nonR23_mode <= 1'b0;
			ff_interrupt_line_nonR23_mode <= 1'b0;
			ff_sprite_mode3 <= 1'b0;
			ff_ext_palette_mode <= 1'b0;
			ff_sprite16_mode <= 1'b0;
			ff_command_end_interrupt_enable <= 1'b0;
			ff_flat_interlace_mode <= 1'b0;
			//	_163: arranca en modo V9958 (igual que el ff_fakeID <= 1 de antes)
			//	=> comandos extendidos y 256K DESACTIVADOS tras el reset, que es
			//	el comportamiento que ya teniamos.
			ff_v9958_mode <= 1'b1;
		end
		else if( ff_register_write ) begin
			case( ff_register_num )
			6'd0:	//	R#0 = [N/A][N/A][N/A][IE1][M5][M4][M3][N/A]
				begin
					ff_screen_mode[4:2] <= ff_1st_byte[3:1];
					ff_line_interrupt_enable <= ff_1st_byte[4];
				end
			6'd1:	//	R#1 = [N/A][BL][IE0][M1][M2][N/A][SI][MAG]
				begin
					ff_sprite_magify <= ff_1st_byte[0];
					ff_sprite_16x16 <= ff_1st_byte[1];
					ff_screen_mode[1] <= ff_1st_byte[3];
					ff_screen_mode[0] <= ff_1st_byte[4];
					ff_frame_interrupt_enable <= ff_1st_byte[5];
					ff_display_on <= ff_1st_byte[6];
				end
			6'd2:	//	R#2 = [A17][A16][A15][A14][A13][A12][A11][A10]
				begin
					ff_pattern_name_table_base <= ff_1st_byte;
				end
			6'd3:	//	R#3 = [A13][A12][A11][A10][A9][A8][A7][A6]
				begin
					ff_color_table_base[13:6] <= ff_1st_byte;
				end
			6'd4:	//	R#4 = [N/A][A17][A16][A15][A14][A13][A12][A11]
				begin
					ff_pattern_generator_table_base <= ff_1st_byte[6:0];
				end
			6'd5:	//	R#5 = [A14][A13][A12][A11][A10][A9][A8][A7]
				begin
					ff_sprite_attribute_table_base[14:7] <= ff_1st_byte;
				end
			6'd6:	//	R#6 = [N/A][A17][A16][A15][A14][A13][A12][A11]
				begin
					ff_sprite_pattern_generator_table_base <= ff_1st_byte[6:0];
				end
			6'd7:	//	R#7 = [BD7][BD6][BD5][BD4][BD3][BD2][BD1][BD0]
				begin
					ff_backdrop_color <= ff_1st_byte;
				end
			6'd8:	//	R#8 = [N/A][N/A][TP][N/A][VR][N/A][SPD][N/A]
				begin
					ff_sprite_disable <= ff_1st_byte[1];
					ff_vram_type <= ff_1st_byte[3];
					ff_color0_opaque <= ff_1st_byte[5];
				end
			6'd9:	//	R#9 = [LN][N/A][N/A][N/A][IL][EO][NT][N/A]
				begin
					//	MSXimus _125 (v1): NTSC-only — el puente HDMI es
					//	60Hz/525 fijo; con NT=1 el core cambiaba a 625 lineas
					//	y la imagen quedaba negra/descompuesta (PAL TEST de
					//	HRA, HW _124). El bit se IGNORA: software PAL se ve a
					//	60Hz. PAL real = pendiente.
					ff_50hz_mode <= 1'b0;
					ff_interleaving_mode <= ff_1st_byte[2];
					ff_interlace_mode <= ff_1st_byte[3];
					ff_212lines_mode <= ff_1st_byte[7];
				end
			6'd10:	//	R#10 = [N/A][N/A][N/A][N/A][A17][A16][A15][A14]
				begin
					ff_color_table_base[17:14] <= ff_1st_byte[3:0];
				end
			6'd11:	//	R#11 = [N/A][N/A][N/A][N/A][N/A][A17][A16][A15]
				begin
					ff_sprite_attribute_table_base[17:15] <= ff_1st_byte[2:0];
				end
			6'd12:	//	R#12 = [T23][T22][T1][T20][BC3][BC2][BC1][BC0]
				begin
					ff_text_back_color <= ff_1st_byte;
				end
			6'd13:	//	R#13 = [CN3][CN2][CN1][CN0][CF3][CF2][CF1][CF0]
				begin
					ff_blink_period <= ff_1st_byte;
				end

			//	6'd14 は、ff_vram_address の always文にある

			6'd15:	//	R#15 = [N/A][N/A][N/A][N/A][S3][S2][S1][S0]
				begin
					ff_status_register_pointer <= ff_1st_byte[3:0];
				end

			//	6'd16 は、color palette interface の always文にある

			//	6'd17 は、register pointer の always文にある

			8'd18:	//	R#18 = [V3][V2][V1][V0][H3][H2][H1][H0]
				begin
					ff_display_adjust <= ff_1st_byte;
				end
			8'd19:	//	R#19 = [IL7][IL6][IL5][IL4][IL3][IL2][IL1][IL0]
				begin
					ff_interrupt_line <= ff_1st_byte;
				end
			//	MSXimus _163: MAPA NUEVO de R#20/R#21 — port del commit 0683e7e de
			//	HRA ("Register R#20, R#21 Modified", tag v0.6). Un solo bit
			//	(R#21[0] = V58) conmuta las TRES cosas de golpe: el ID que
			//	devuelve S#1, los comandos extendidos y el direccionamiento de
			//	256K. Eso libera R#20[5] y R#20[6], que pasan a llevar el
			//	entrelazado plano y la interrupcion de fin de comando.
			//	⚠️ El comentario de cabecera de R#20 del upstream NO se actualizo
			//	y por eso alli MIENTE; aqui va corregido.
			//	⚠️ Requiere el byte 14 de DEVCON.COM a 0x9F (era 0xFF) y el
			//	offset 0x377 de V9968DM.COM. Sin eso las dos herramientas de
			//	diagnostico de HRA programan el VDP con el mapa viejo.
			8'd20:	//	R#20 = [S16][CEIE][ILN][EPAL][SCOL][ILNS][SVNS][HS]
				begin
					if( !ff_lock_extregs ) begin	//	gen C: solo desbloqueado por el puerto #4
						ff_command_high_speed_mode <= ff_1st_byte[0];
						ff_sprite_nonR23_mode <= ff_1st_byte[1];
						ff_interrupt_line_nonR23_mode <= ff_1st_byte[2];
						ff_sprite_mode3 <= ff_1st_byte[3];
						ff_ext_palette_mode <= ff_1st_byte[4];
						ff_flat_interlace_mode <= ff_1st_byte[5];
						ff_command_end_interrupt_enable <= ff_1st_byte[6];
						ff_sprite16_mode <= ff_1st_byte[7];
					end
				end
			8'd21:	//	R#21 = [N/A][N/A][N/A][N/A][N/A][N/A][N/A][V58]
				begin
					if( !ff_lock_extregs ) begin	//	gen C: la BIOS escribe R#21=0 en cada init y NO debe cambiar el modo
						ff_v9958_mode <= ff_1st_byte[0];
					end
				end
			8'd23:	//	R#23 = [DO7][DO6][DO5][DO4][DO3][DO2][DO1][DO0]
				begin
					ff_vertical_offset <= ff_1st_byte;
				end
			8'd25:	//	R#25 = [N/A][CMD][N/A][YAE][YJK][N/A][MSK][SP2]
				begin
					ff_scroll_planes <= ff_1st_byte[0];
					ff_left_mask <= ff_1st_byte[1];
					ff_yjk_mode <= ff_1st_byte[3];
					ff_yae_mode <= ff_1st_byte[4];
					ff_command_enable <= ff_1st_byte[6];
					ff_sprite_priority_shuffle <= ff_1st_byte[7];
				end
			8'd26:	//	R#26 = [N/A][N/A][HO8][HO7][HO6][HO5][HO4][HO3]
				begin
					ff_horizontal_offset_h <= ff_1st_byte[5:0];
				end
			8'd27:	//	R#27 = [N/A][N/A][N/A][N/A][N/A][HO2][HO1][HO0]
				begin
					ff_horizontal_offset_l <= ff_1st_byte[2:0];
				end
			default:
				begin
					//	hold
				end
			endcase
		end
	end

	// --------------------------------------------------------------------
	//	Color palette interface
	// --------------------------------------------------------------------
	always @( posedge clk ) begin
		if( !reset_n ) begin
			ff_color_palette_address	<= 8'd0;
			ff_color_palette_valid		<= 1'b0;
			ff_color_palette_phase		<= 2'd0;
		end
		else if( ff_register_write ) begin
			if( ff_register_num == 6'd16 ) begin
				//	R#16 = [C7][C6][C5][C4][C3][C2][C1][C0]
				if( ff_ext_palette_mode ) begin
					ff_color_palette_address	<= ff_1st_byte;
				end
				else begin
					ff_color_palette_address	<= { 4'd0, ff_1st_byte[3:0] };
				end
				ff_color_palette_phase		<= 2'd0;
			end
		end
		else if( w_write && ff_port2 ) begin
			if( ff_ext_palette_mode ) begin
				if( ff_color_palette_phase == 2'd0 ) begin
					//	P#2 = [N/A][N/A][N/A][R][R][R][R][R]
					ff_palette_r				<= ff_bus_wdata[4:0];
					ff_color_palette_phase		<= 2'd1;
					ff_color_palette_valid		<= 1'b0;
				end
				else if( ff_color_palette_phase == 2'd1 ) begin
					//	P#2 = [N/A][N/A][N/A][G][G][G][G][G]
					ff_palette_g				<= ff_bus_wdata[4:0];
					ff_color_palette_phase		<= 2'd2;
					ff_color_palette_valid		<= 1'b0;
				end
				else begin
					//	P#2 = [N/A][N/A][N/A][B][B][B][B][B]
					ff_palette_b				<= ff_bus_wdata[4:0];
					ff_color_palette_phase		<= 2'd0;
					ff_color_palette_valid		<= 1'b1;
				end
			end
			else begin
				if( ff_color_palette_phase == 2'd0 ) begin
					//	P#2 = [0][R][R][R][0][B][B][B]  (30/09: se guarda en ff_1st_byte, el latch compartido)
					ff_color_palette_phase		<= 2'd1;
					ff_color_palette_valid		<= 1'b0;
				end
				else begin
					//	P#2 = [0][0][0][0][0][G][G][G]
					ff_palette_r				<= { ff_1st_byte[6:4], ff_1st_byte[6:5] };
					ff_palette_b				<= { ff_1st_byte[2:0], ff_1st_byte[2:1] };
					ff_palette_g				<= { ff_bus_wdata[2:0], ff_bus_wdata[2:1] };
					ff_color_palette_phase		<= 2'd0;
					ff_color_palette_valid		<= 1'b1;
				end
			end
		end
		else if( ff_color_palette_valid ) begin
			if( ff_ext_palette_mode ) begin
				ff_color_palette_address		<= ff_color_palette_address + 8'd1;
			end
			else begin
				ff_color_palette_address[3:0]	<= ff_color_palette_address[3:0] + 4'd1;
				ff_color_palette_address[7:4]	<= 4'd0;
			end
			ff_color_palette_valid		<= 1'b0;
		end
	end

	// --------------------------------------------------------------------
	//	Read data latch
	// --------------------------------------------------------------------

	always @( posedge clk ) begin
		case( ff_status_register_pointer )
		4'd0:		ff_status_register <= { ff_frame_interrupt, sprite_overmap, sprite_collision, sprite_overmap_id };
		4'd1:		ff_status_register <= { 2'd0, ff_v9958_mode ? c_v9958id: c_v9968id, ff_line_interrupt };
		4'd2:		ff_status_register <= { status_transfer_ready, status_vsync, status_hsync, status_border_detect, 2'b11, status_field, status_command_execute };
		4'd3:		ff_status_register <= sprite_collision_x[7:0];
		4'd4:		ff_status_register <= { 7'b1111111, sprite_collision_x[8] };
		4'd5:		ff_status_register <= sprite_collision_y[7:0];
		4'd6:		ff_status_register <= { 6'b111111, sprite_collision_y[9:8] };
		4'd7:		ff_status_register <= status_color;
		4'd8:		ff_status_register <= status_border_position[7:0];
		4'd9:		ff_status_register <= { 7'b1111111, status_border_position[8] };
		default:	ff_status_register <= 8'b11111111;
		endcase
	end

	// --------------------------------------------------------------------
	//	MSXimus _149: buffer de PRE-LECTURA de VRAM
	// --------------------------------------------------------------------
	always @( posedge clk ) begin
		if( !reset_n ) begin
			ff_pf_valid	<= 1'b0;
			ff_pf_data	<= 8'd0;
		end
		else if( vram_rdata_en && ff_pf_inflight ) begin
			ff_pf_data	<= vram_rdata;
			ff_pf_valid	<= 1'b1;
		end
		else if( w_pf_hit || w_pf_invalidate ) begin
			ff_pf_valid	<= 1'b0;
		end
	end

	always @( posedge clk ) begin
		if( !reset_n ) begin
			ff_bus_rdata_en		<= 1'b0;
		end
		//	MSXimus _149: si la lectura completada era una PRE-lectura, su dato NO
		//	va al bus (va al buffer, mas abajo) — el bus lo recoge en el IN.
		else if( vram_rdata_en && !ff_pf_inflight ) begin
			if( vram_access_mask ) begin
				ff_bus_rdata		<= 8'b11111111;
			end
			else begin
				ff_bus_rdata		<= vram_rdata;
			end
			ff_bus_rdata_en		<= 1'b1;
		end
		else if( w_read ) begin
			if( ff_port0 ) begin
				if( ff_pf_valid ) begin
					//	MSXimus _149: ACIERTO — el byte ya estaba pre-leido
					ff_bus_rdata	<= vram_access_mask ? 8'b11111111 : ff_pf_data;
					ff_bus_rdata_en	<= 1'b1;
				end
				else begin
					ff_bus_rdata	<= 8'b11111111;
					ff_bus_rdata_en	<= 1'b0;
				end
			end
			else if( ff_port1 ) begin
				ff_bus_rdata	<= ff_status_register;
				ff_bus_rdata_en	<= 1'b1;
			end
			else if( ff_port4 ) begin
				ff_bus_rdata	<= { ff_lock_extregs, 4'd0, ff_command_end_interrupt, ff_line_interrupt, ff_frame_interrupt };
				ff_bus_rdata_en	<= 1'b1;
			end
			else begin
				ff_bus_rdata	<= 8'b11111111;
				ff_bus_rdata_en	<= 1'b1;
			end
		end
		else begin
			ff_bus_rdata	<= 8'd0;
			ff_bus_rdata_en	<= 1'b0;
		end
	end

	assign clear_sprite_collision		= (w_read && ff_port1 && ff_status_register_pointer == 4'd0);
	assign clear_sprite_collision_xy	= (w_read && ff_port1 && ff_status_register_pointer == 4'd5);
	assign read_color					= (w_read && ff_port1 && ff_status_register_pointer == 4'd7);
	assign clear_border_detect			= (w_read && ff_port1 && ff_status_register_pointer == 4'd9);

	// --------------------------------------------------------------------
	//	Interrupt
	// --------------------------------------------------------------------
	//	_188 (la novena caza, Fleet, 05/08): LA INT TRAGADA POR EL POLL.
	//	La cadena if/else original tenia dos agujeros contra el silicio:
	//	 (1) si el pulso de evento (intr_frame/line) coincidia con el ciclo
	//	     del clear-por-lectura, el clear GANABA y el evento se PERDIA;
	//	 (2) peor: durante el ciclo de CUALQUIER lectura de status (aunque
	//	     fuera S#2) o escritura al puerto 4, la rama de los sets no se
	//	     ejecutaba => apagon de los TRES sets. Un juego poleando S#2 a
	//	     ~20k lecturas/s (la espera de fin de comando de la escuela TMS
	//	     — Fleet en su carga) se traga una INT de frame una vez cada
	//	     ~70-80 s: la ventana exacta de sus muertes. En el chip real el
	//	     evento JAMAS se pierde. Ahora sets y clears van en PARALELO por
	//	     flag y el SET DOMINA sobre los clears de software (el software
	//	     leyo el valor VIEJO; el evento nuevo arma el flag y el
	//	     siguiente poll/ISR lo ve — semantica del silicio). El orden
	//	     entre señales de HARDWARE (clear_line_interrupt/intr_frame
	//	     sobre intr_line) se conserva tal cual del upstream.
	always @( posedge clk ) begin
		if( !reset_n ) begin
			ff_frame_interrupt			<= 1'b0;
			ff_line_interrupt			<= 1'b0;
			ff_command_end_interrupt	<= 1'b0;
			ff_lock_extregs				<= 1'b1;
		end
		else begin
			//	---- frame (F) ----
			if( intr_frame ) begin
				ff_frame_interrupt <= 1'b1;
			end
			else if( (w_read  && ff_port1 && ff_status_register_pointer == 4'd0)
			      || (w_write && ff_port4 && ff_bus_wdata[0] == 1'b1) ) begin
				//	Clear frame interrupt flag (lectura de S#0 o puerto 4 bit0)
				ff_frame_interrupt <= 1'b0;
			end

			//	---- line (FH) ----
			if( clear_line_interrupt || intr_frame ) begin
				ff_line_interrupt <= 1'b0;
			end
			else if( intr_line ) begin
				ff_line_interrupt <= 1'b1;
			end
			else if( (w_read  && ff_port1 && ff_status_register_pointer == 4'd1)
			      || (w_write && ff_port4 && ff_bus_wdata[1] == 1'b1)
			      || (ff_register_write && (ff_register_num == 6'd0 || ff_register_num == 6'd19)) ) begin
				//	Clear line interrupt flag (lectura de S#1, puerto 4 bit1,
				//	o escritura de R#0/R#19)
				ff_line_interrupt <= 1'b0;
			end

			//	---- bloqueo de R#20/R#21 (gen C): bit 7 de cada escritura al puerto #4 ----
			if( w_write && ff_port4 ) begin
				ff_lock_extregs <= ff_bus_wdata[7];
			end

			//	---- fin de comando (CE-int) ----
			//	upstream 7298638: quedaba una rama legada que borraba el
			//	interrupt de FIN DE COMANDO al leer S#10. El unico clear
			//	legitimo es la escritura en el puerto 4 con bit2=1.
			if( intr_command_end ) begin
				ff_command_end_interrupt <= 1'b1;
			end
			else if( w_write && ff_port4 && ff_bus_wdata[2] == 1'b1 ) begin
				ff_command_end_interrupt <= 1'b0;
			end
		end
	end

	assign w_line_interrupt			= ff_line_interrupt			& ff_line_interrupt_enable;
	assign w_frame_interrupt		= ff_frame_interrupt		& ff_frame_interrupt_enable;
	assign w_command_end_interrupt	= ff_command_end_interrupt	& ff_command_end_interrupt_enable;
	assign int_n = ~(w_line_interrupt | w_frame_interrupt | w_command_end_interrupt);

	always @( posedge clk ) begin
		ff_force_highspeed <= force_highspeed;
	end

	// --------------------------------------------------------------------
	//	Output assignment
	// --------------------------------------------------------------------
	assign register_write							= ff_register_write;
	assign register_num								= ff_register_num;
	assign register_data							= ff_1st_byte;

	assign bus_rdata								= ff_bus_rdata;
	assign bus_rdata_en								= ff_bus_rdata_en;

	assign vram_address								= ff_vram_address;
	assign vram_write								= ff_vram_write;
	assign vram_valid								= ff_vram_valid;
	assign vram_wdata								= ff_vram_wdata;

	assign palette_valid							= ff_color_palette_valid;
	assign palette_num								= ff_color_palette_address;
	assign palette_r								= ff_palette_r;
	assign palette_g								= ff_palette_g;
	assign palette_b								= ff_palette_b;

	assign reg_screen_mode							= ff_screen_mode;
	assign reg_sprite_magify						= ff_sprite_magify;
	assign reg_sprite_16x16							= ff_sprite_16x16;
	assign reg_display_on							= ff_display_on;
	//	MSXimus 15/09/2026 (Xevious Fardraut Saga, marcador en blanco en la 60K y en la Zynq):
	//	en modo V9958 (R#21[0]=1, el de arranque) el bit A17 de las CINCO bases de tabla se
	//	IGNORA, como ya hace el puerto de VRAM de la CPU (ff_vram_address <= {1'b0, ...}).
	//	El V9968 lo define como A17 para los 256 KB (R#2[7], R#4[6], R#6[6], R#10[3],
	//	R#11[2]), pero en un V9938/V9958 esos bits no existen y el software los pone a 1
	//	sin mas: el Xevious muestra su marcador con R#2=FFh (pagina 3) durante las 13
	//	primeras lineas y aqui se buscaba en 38000h, que esta vacio. Con R#21[0]=0
	//	(modo V9968 nativo) se conserva el direccionamiento completo.
	wire	w_a17_ok = ~ff_v9958_mode;
	assign reg_pattern_name_table_base				= ff_force_page2 ? 8'h5F : { ff_pattern_name_table_base[17] & w_a17_ok, ff_pattern_name_table_base[16:10] };
	assign reg_color_table_base						= { ff_color_table_base[17] & w_a17_ok, ff_color_table_base[16:6] };
	assign reg_pattern_generator_table_base			= { ff_pattern_generator_table_base[17] & w_a17_ok, ff_pattern_generator_table_base[16:11] };
	assign reg_sprite_attribute_table_base			= { ff_sprite_attribute_table_base[17] & w_a17_ok, ff_sprite_attribute_table_base[16:7] };
	assign reg_sprite_pattern_generator_table_base	= { ff_sprite_pattern_generator_table_base[17] & w_a17_ok, ff_sprite_pattern_generator_table_base[16:11] };
	assign reg_backdrop_color						= ff_backdrop_color;
	assign reg_sprite_disable						= ff_sprite_disable;
	assign reg_color0_opaque						= ff_color0_opaque;
	assign reg_50hz_mode							= ff_50hz_mode;
	assign reg_interleaving_mode					= ff_interleaving_mode;
	assign reg_interlace_mode						= ff_interlace_mode;
	assign reg_212lines_mode						= ff_212lines_mode;
	assign reg_text_back_color						= ff_text_back_color;
	assign reg_blink_period							= ff_blink_period;
	assign reg_display_adjust						= ff_display_adjust;
	assign reg_interrupt_line						= ff_interrupt_line;
	assign reg_vertical_offset						= ff_vertical_offset;
	assign reg_scroll_planes						= ff_scroll_planes;
	assign reg_left_mask							= ff_left_mask;
	assign reg_yjk_mode								= ff_yjk_mode;
	assign reg_yae_mode								= ff_yae_mode;
	assign reg_command_enable						= ff_command_enable;
	assign reg_sprite_priority_shuffle				= ff_sprite_priority_shuffle;
	assign reg_horizontal_offset_l					= ff_horizontal_offset_l;
	assign reg_horizontal_offset_h					= ff_horizontal_offset_h;
	assign reg_command_high_speed_mode				= ff_command_high_speed_mode | ff_force_highspeed;
	assign reg_sprite_nonR23_mode					= ff_sprite_nonR23_mode;
	assign reg_interrupt_line_nonR23_mode			= ff_interrupt_line_nonR23_mode;
	assign reg_sprite_mode3							= ff_sprite_mode3;
	assign reg_ext_palette_mode						= ff_ext_palette_mode;
	assign reg_ext_command_mode						= ~ff_v9958_mode;
	assign reg_vram256k_mode						= ~ff_v9958_mode;
	assign reg_sprite16_mode						= ff_sprite16_mode;
	assign reg_flat_interlace_mode					= ff_flat_interlace_mode;
endmodule
